WarreDV2004/UCD/Images/testen prototype 2 test 3.jpeg

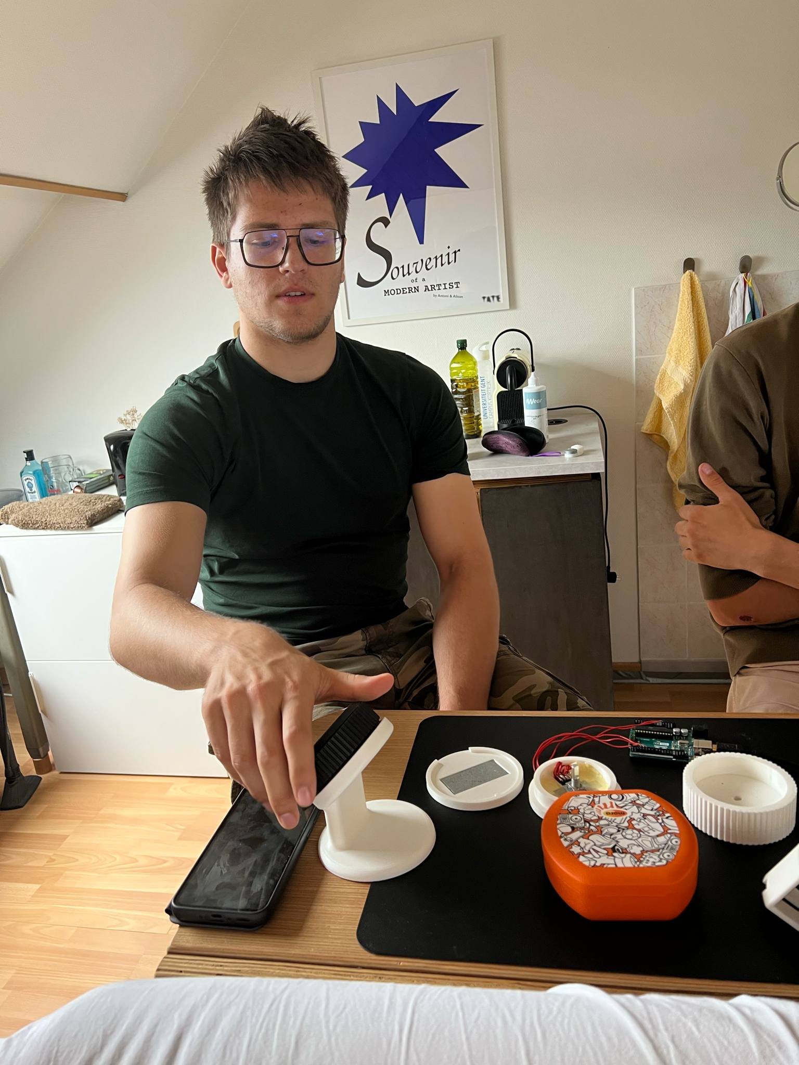
Images/testen prototype 2 test 3.jpeg
