WarreDV2004/UCD/Images/testen prototype test 3.jpeg

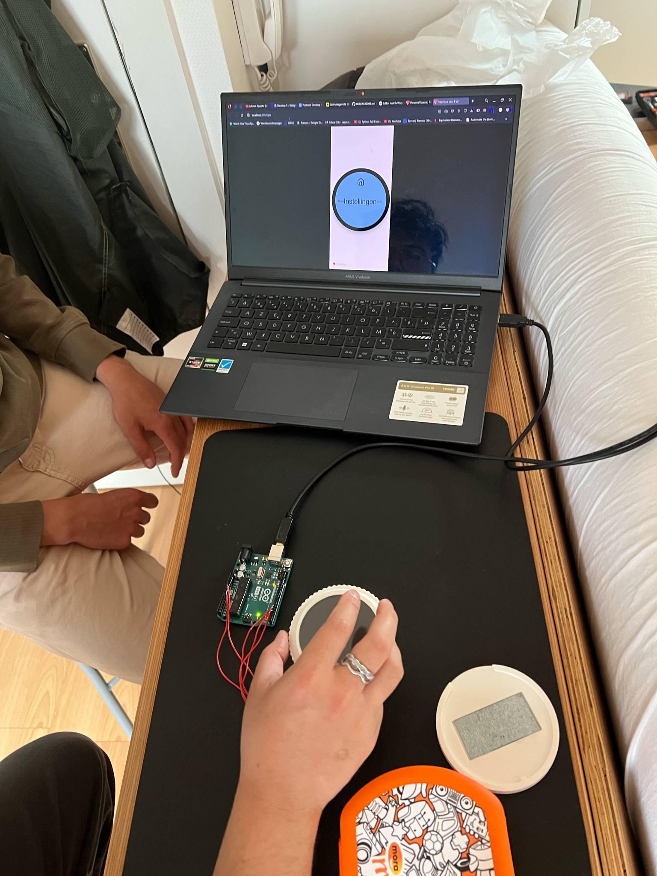
Images/testen prototype test 3.jpeg
