WarreDV2004/UCD/Images/0b0f451a-5053-4762-9009-be1f7eaaebb7.jpeg

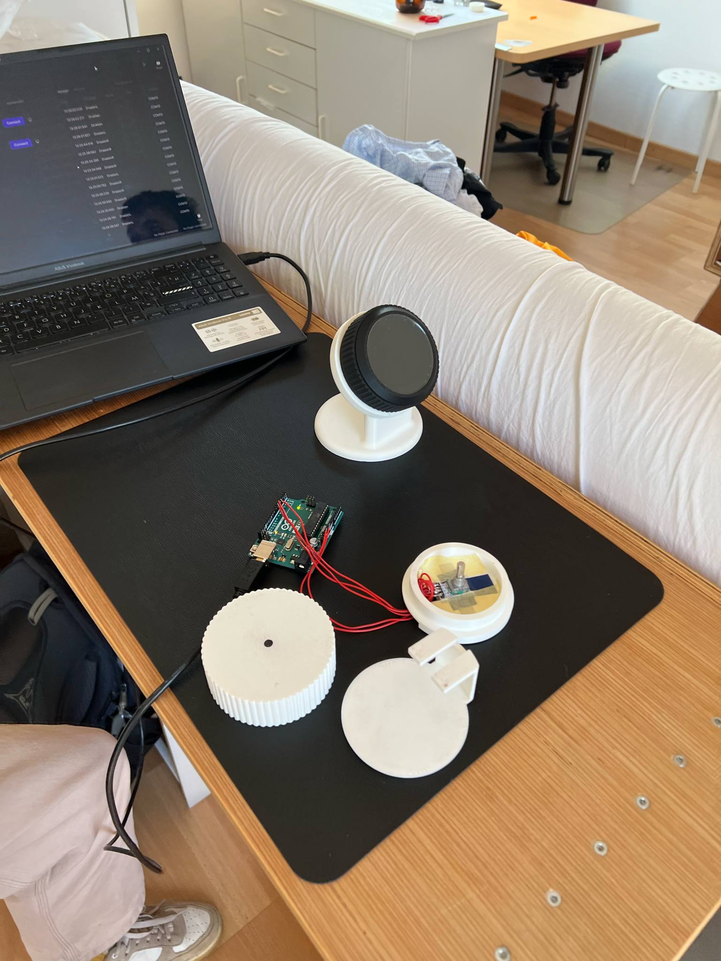
Images/0b0f451a-5053-4762-9009-be1f7eaaebb7.jpeg
