WarreDV2004/UCD/Images/2bf49bff-31a4-4e18-b3c8-147d3d34425b.jpeg

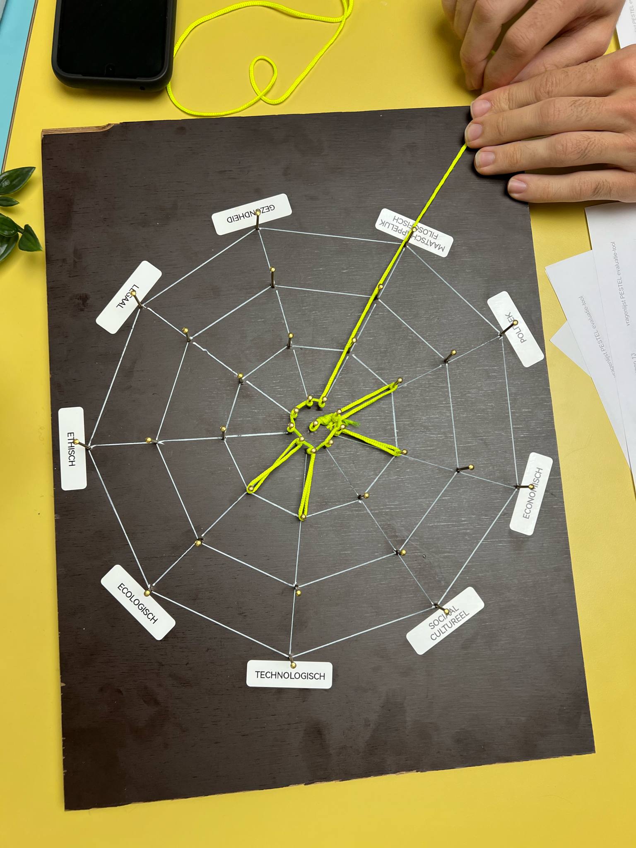
Images/2bf49bff-31a4-4e18-b3c8-147d3d34425b.jpeg
