WarreDV2004/UCD/Images/2db6f0e0-078a-4a34-bcfe-8d26bea21af6.jpeg

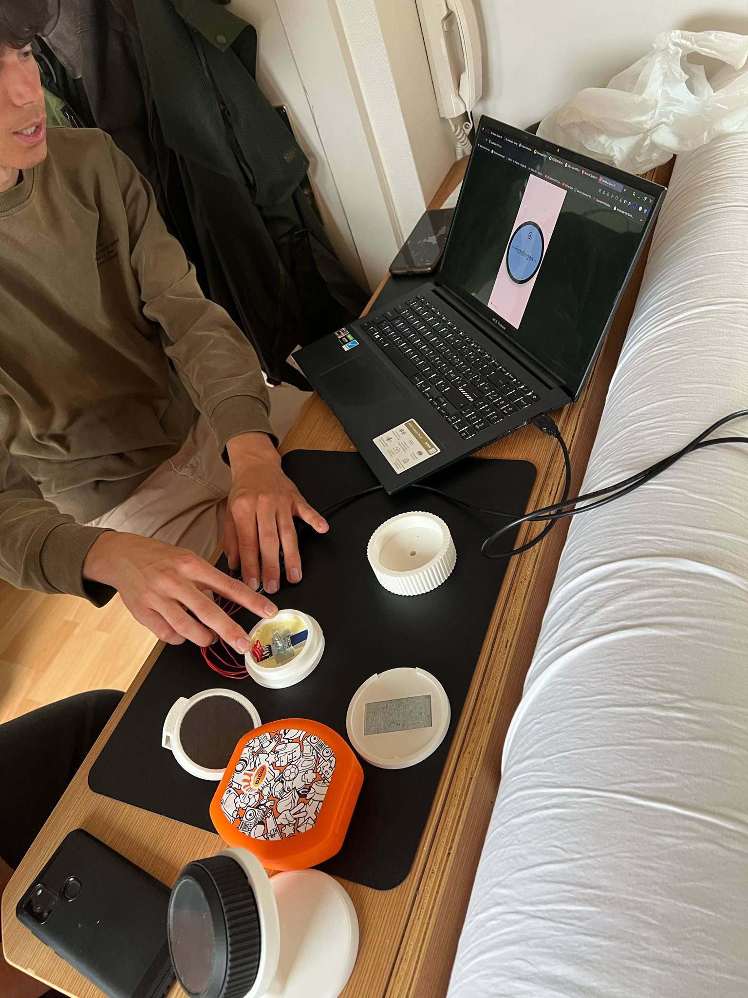
Images/2db6f0e0-078a-4a34-bcfe-8d26bea21af6.jpeg
