WarreDV2004/UCD/Images/4b927118-f5e4-4843-87f0-c27fd5104562.jpeg

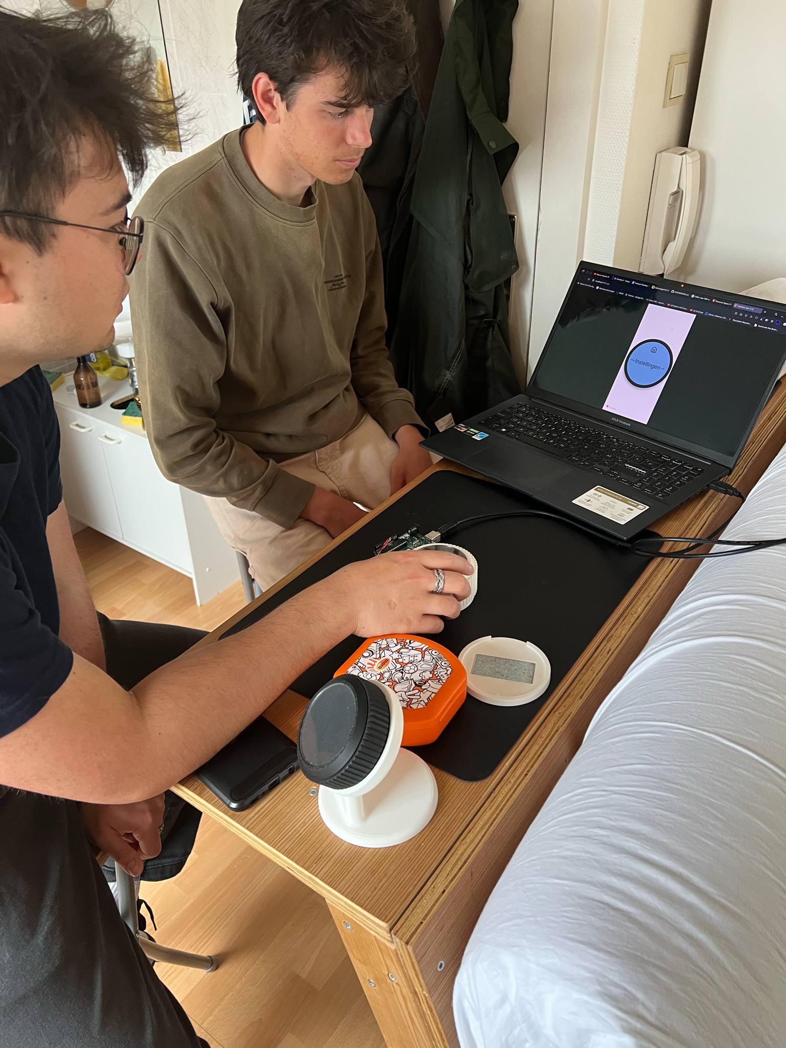
Images/4b927118-f5e4-4843-87f0-c27fd5104562.jpeg
