WarreDV2004/UCD/Images/4e render exploded view.jpg

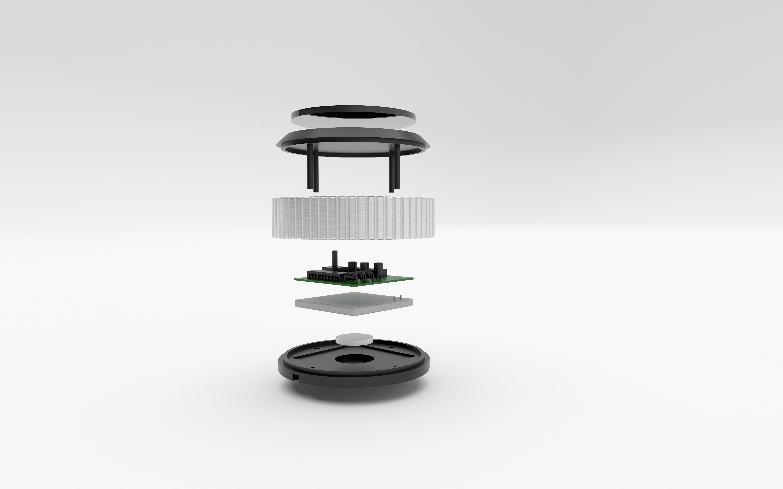
Images/4e render exploded view.jpg
