WarreDV2004/UCD/Images/4fdb726b-e008-48d0-8b07-4f853df536ba.jpeg

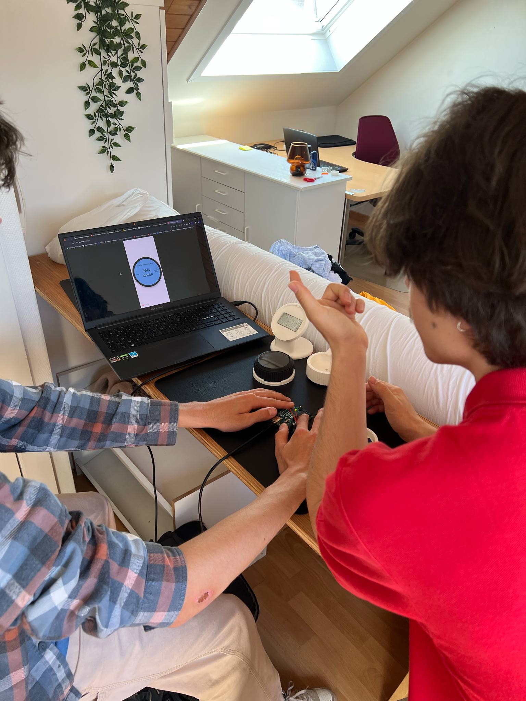
Images/4fdb726b-e008-48d0-8b07-4f853df536ba.jpeg
