WarreDV2004/UCD/Images/8ac05575-f322-4f7c-a051-7a8421dc1b2e.jpeg

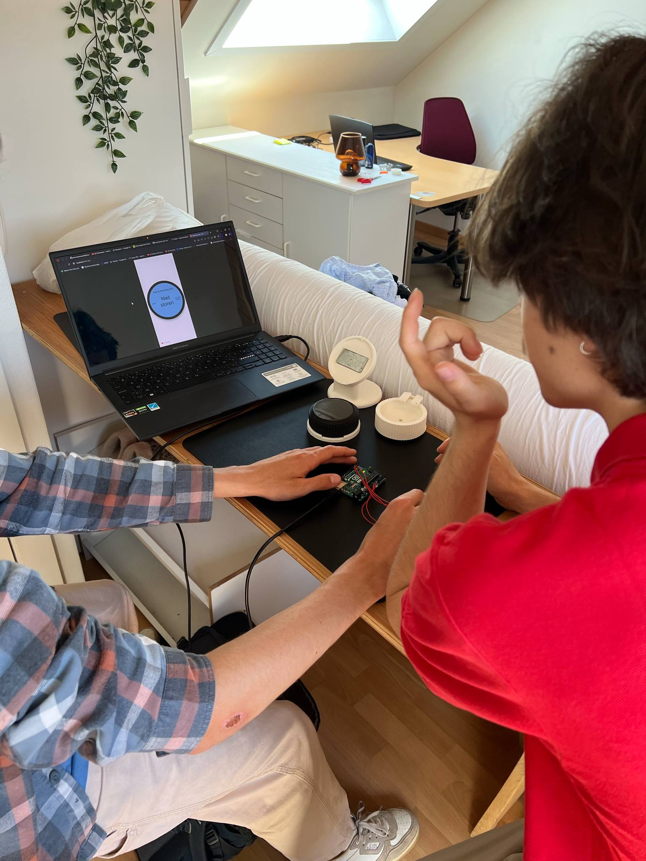
Images/8ac05575-f322-4f7c-a051-7a8421dc1b2e.jpeg
