WarreDV2004/UCD/Images/13f31a89-18ec-47ce-9137-7a15a04f8204.jpeg

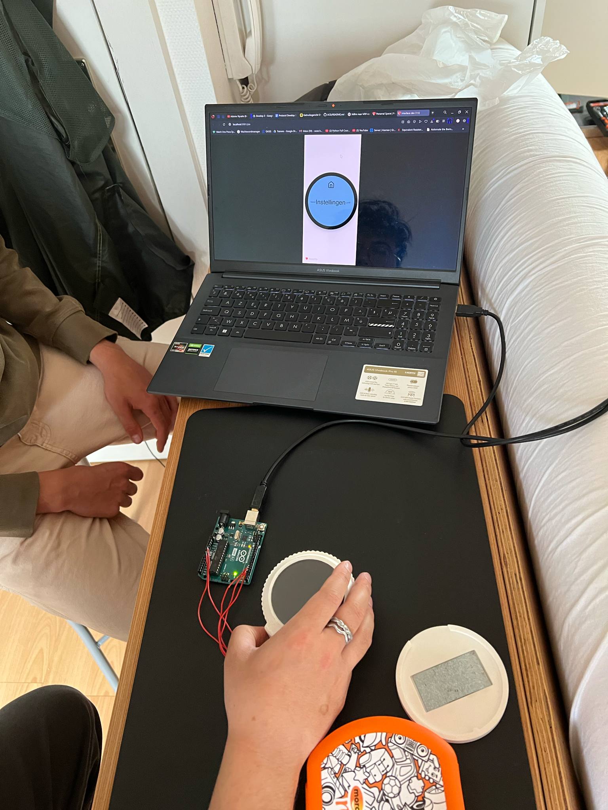
Images/13f31a89-18ec-47ce-9137-7a15a04f8204.jpeg
