WarreDV2004/UCD/Images/45c63ba8-a671-4e61-bb3f-2d00b8ac04eb.jpeg

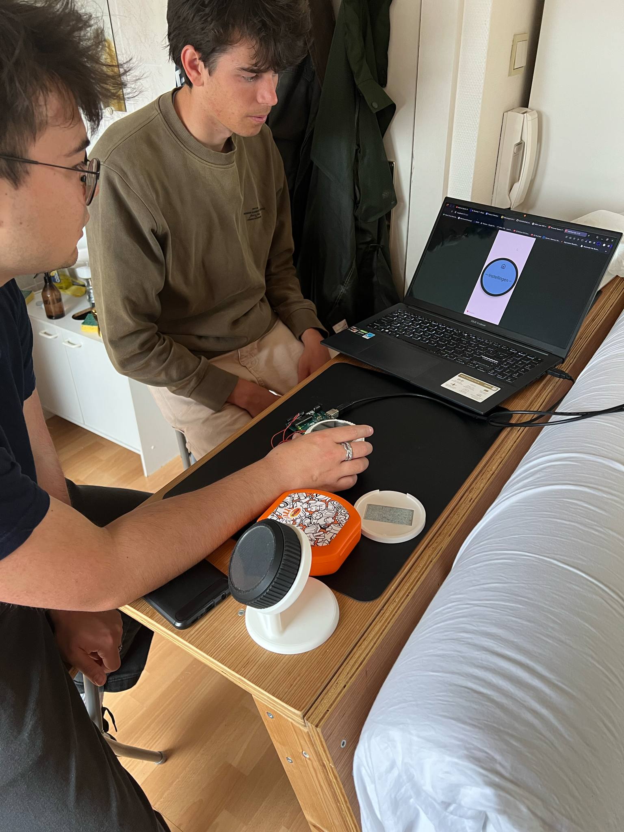
Images/45c63ba8-a671-4e61-bb3f-2d00b8ac04eb.jpeg
