WarreDV2004/UCD/Images/81fb5b29-8a82-44d0-8cb8-3fc07b8e7cfb.jpeg

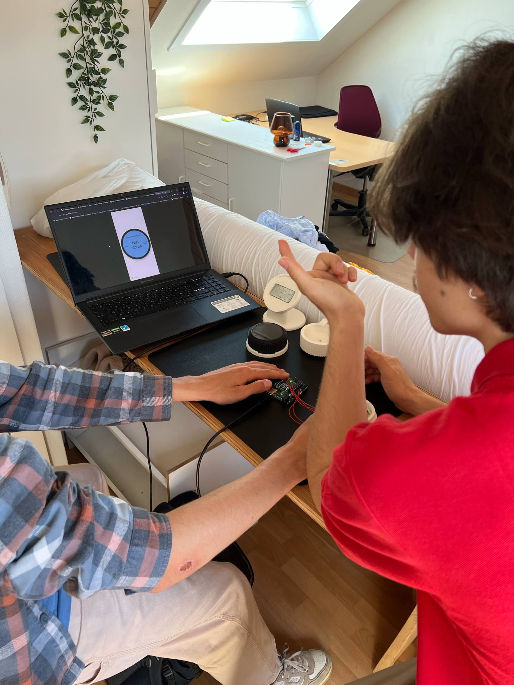
Images/81fb5b29-8a82-44d0-8cb8-3fc07b8e7cfb.jpeg
