WarreDV2004/UCD/Images/103dc806-d890-496e-9fd0-2eff75873912.jpeg

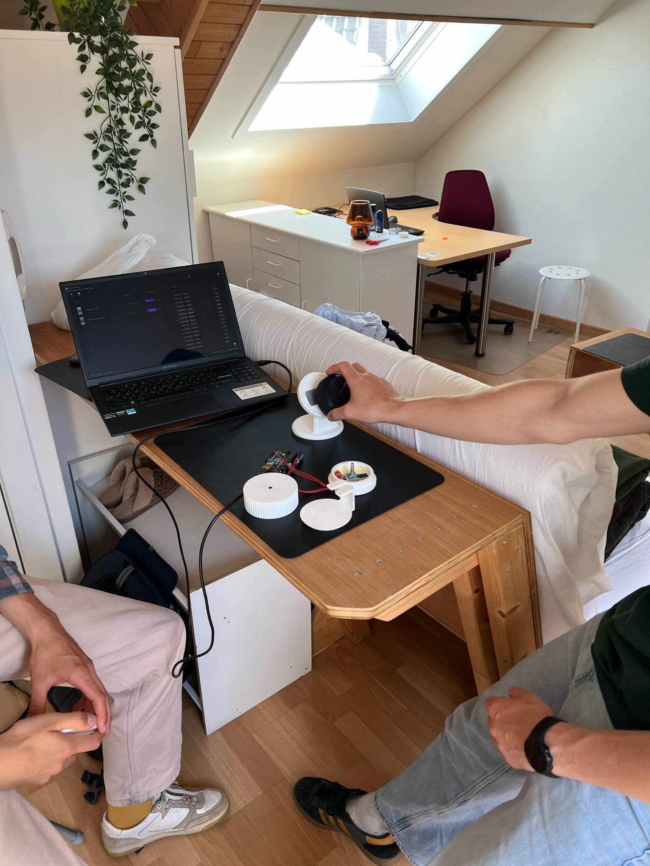
Images/103dc806-d890-496e-9fd0-2eff75873912.jpeg
