WarreDV2004/UCD/Images/169db717-07ae-4d13-a04f-ba3e3b913fad.jpeg

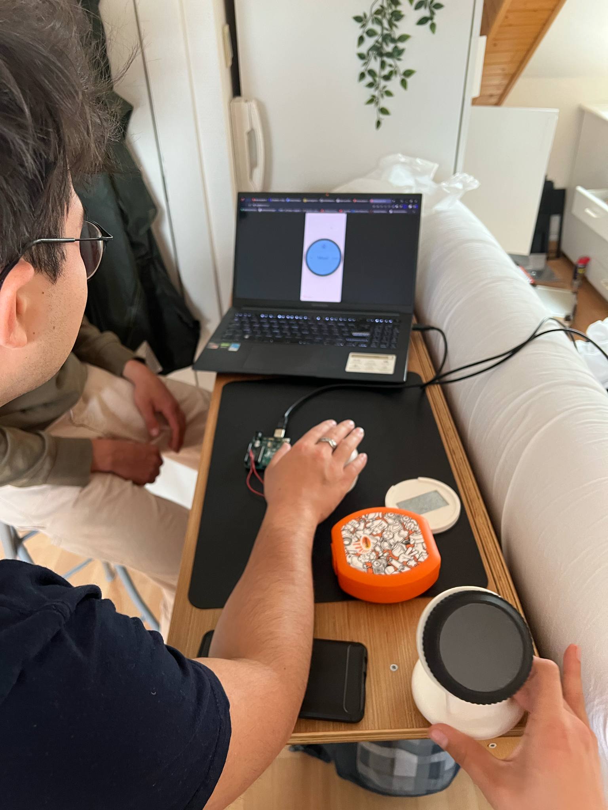
Images/169db717-07ae-4d13-a04f-ba3e3b913fad.jpeg
