WarreDV2004/UCD/Images/230cefa4-2b14-4361-b15c-a140190fd961.jpeg

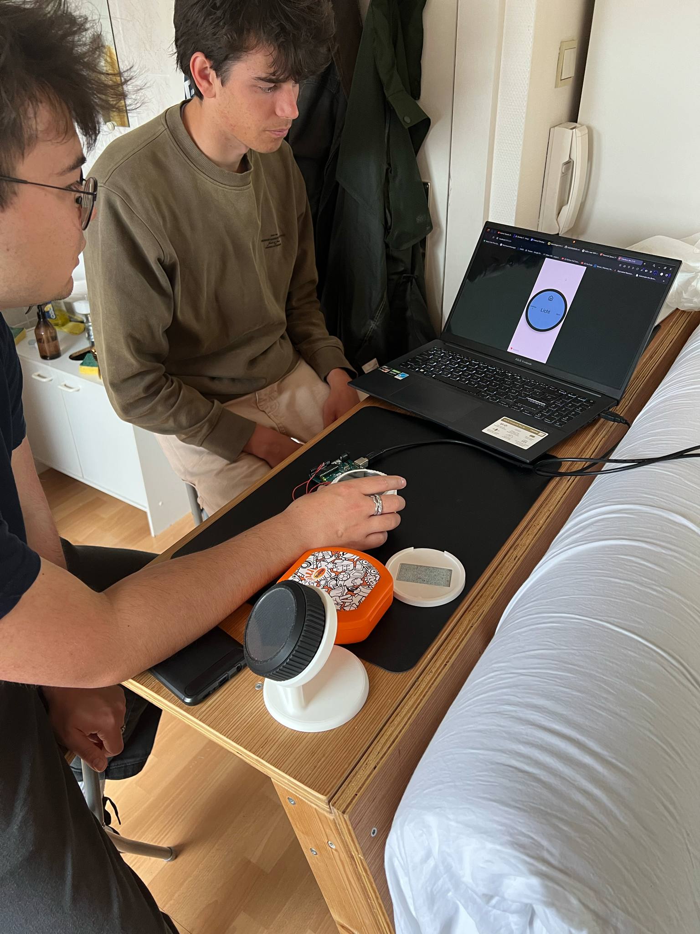
Images/230cefa4-2b14-4361-b15c-a140190fd961.jpeg
