WarreDV2004/UCD/Images/235fdd10-d258-4962-a08e-ac36dd64d68d.jpeg

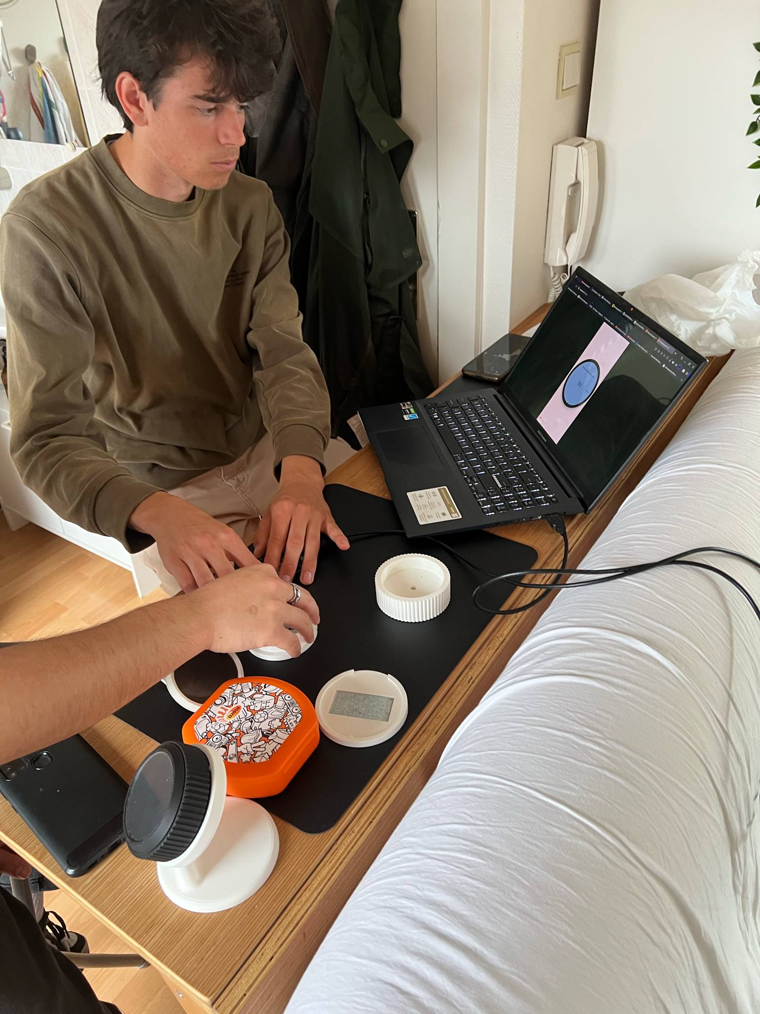
Images/235fdd10-d258-4962-a08e-ac36dd64d68d.jpeg
