WarreDV2004/UCD/Images/516b5541-f568-4937-b32e-dc914a8df41c.jpeg

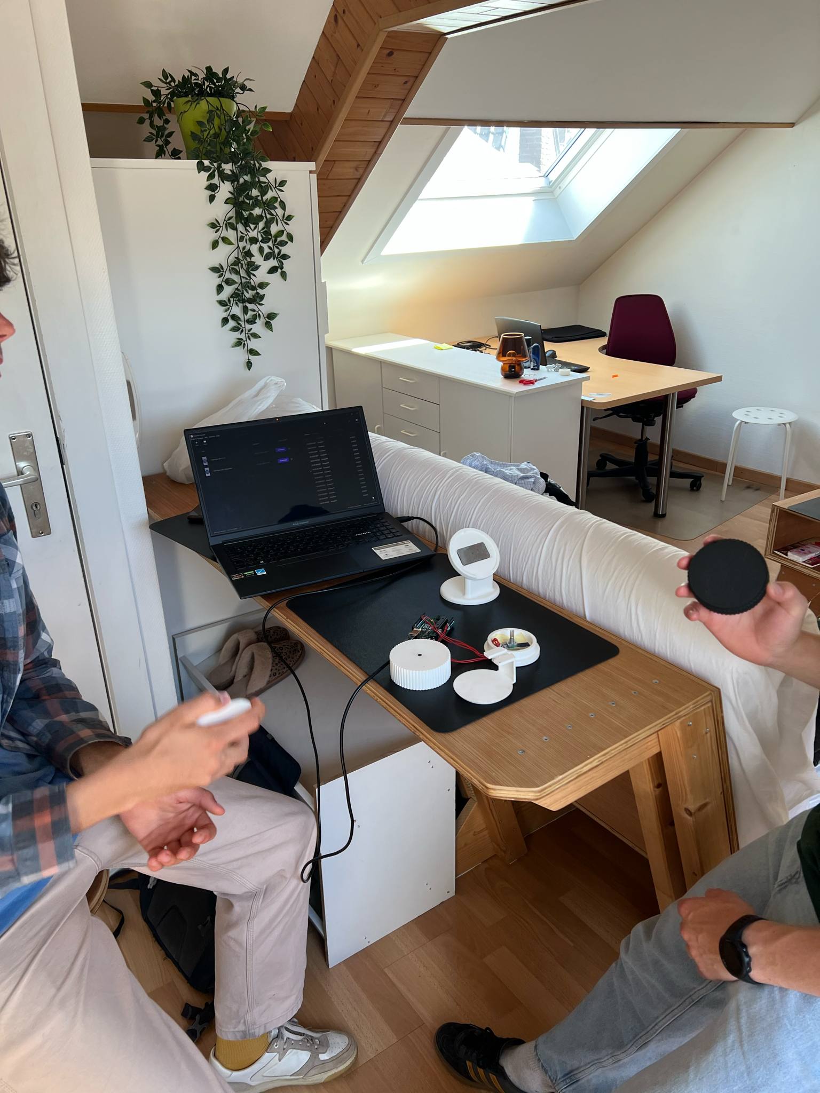
Images/516b5541-f568-4937-b32e-dc914a8df41c.jpeg
