WarreDV2004/UCD/Images/696e4ac5-deb2-44e5-8a80-ce5050431351.jpeg

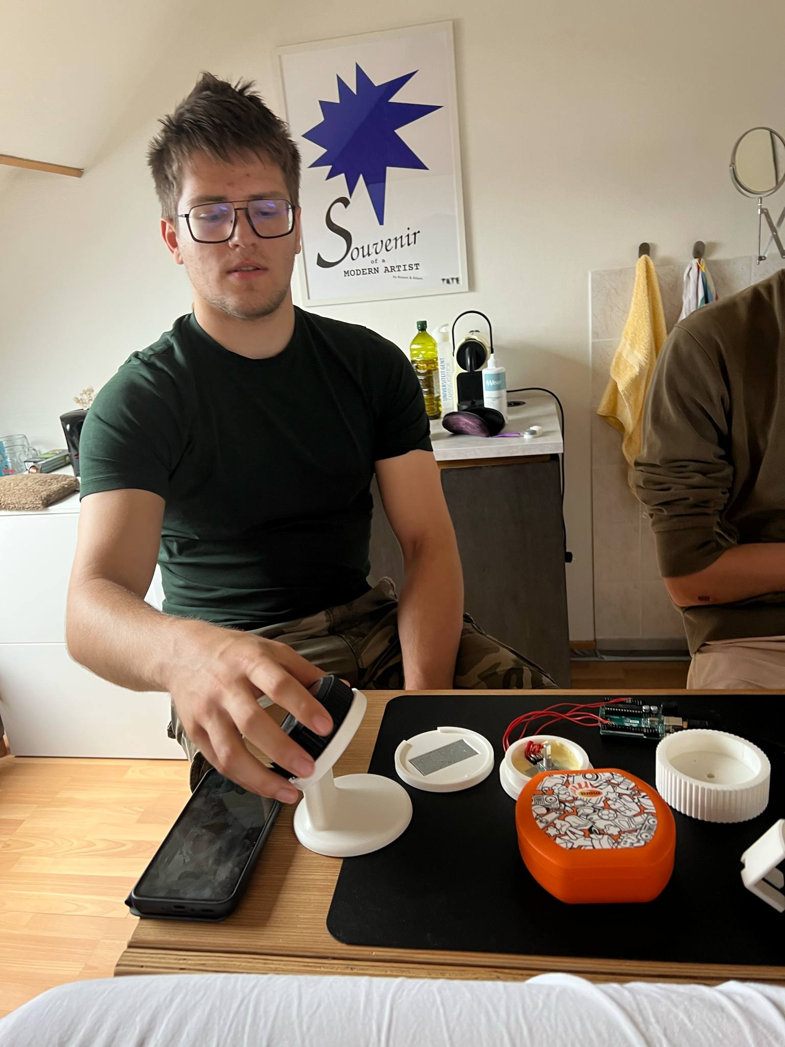
Images/696e4ac5-deb2-44e5-8a80-ce5050431351.jpeg
