WarreDV2004/UCD/Images/876d89a1-647a-4278-9378-e442717ffbb1.jpeg

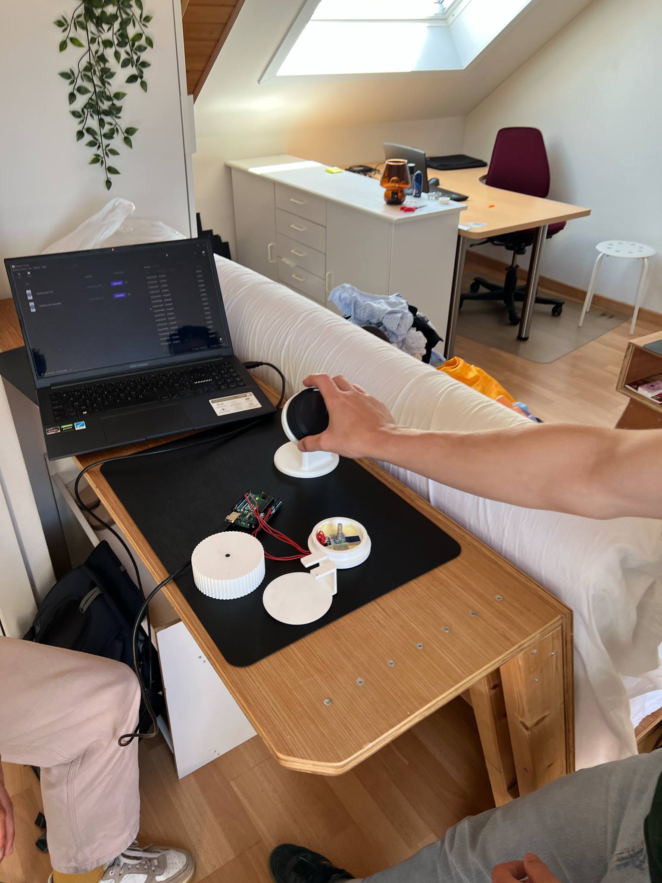
Images/876d89a1-647a-4278-9378-e442717ffbb1.jpeg
