WarreDV2004/UCD/Images/32217a44-98ed-48ee-934f-d554f41f827a.jpeg

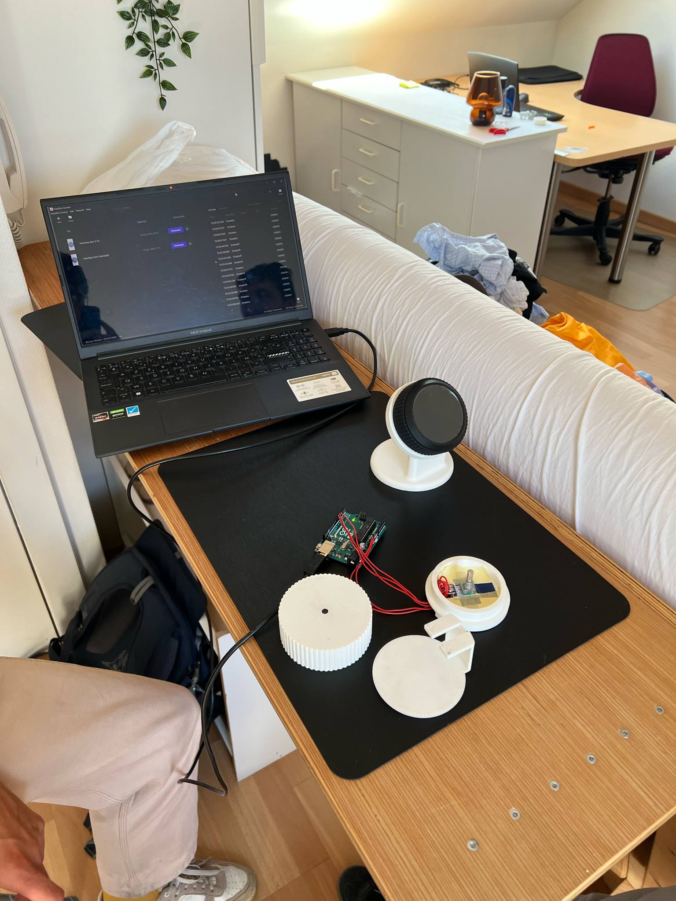
Images/32217a44-98ed-48ee-934f-d554f41f827a.jpeg
