WarreDV2004/UCD/Images/a9bcda80-063e-4bb6-8cd2-c2ead3fb787c.jpeg

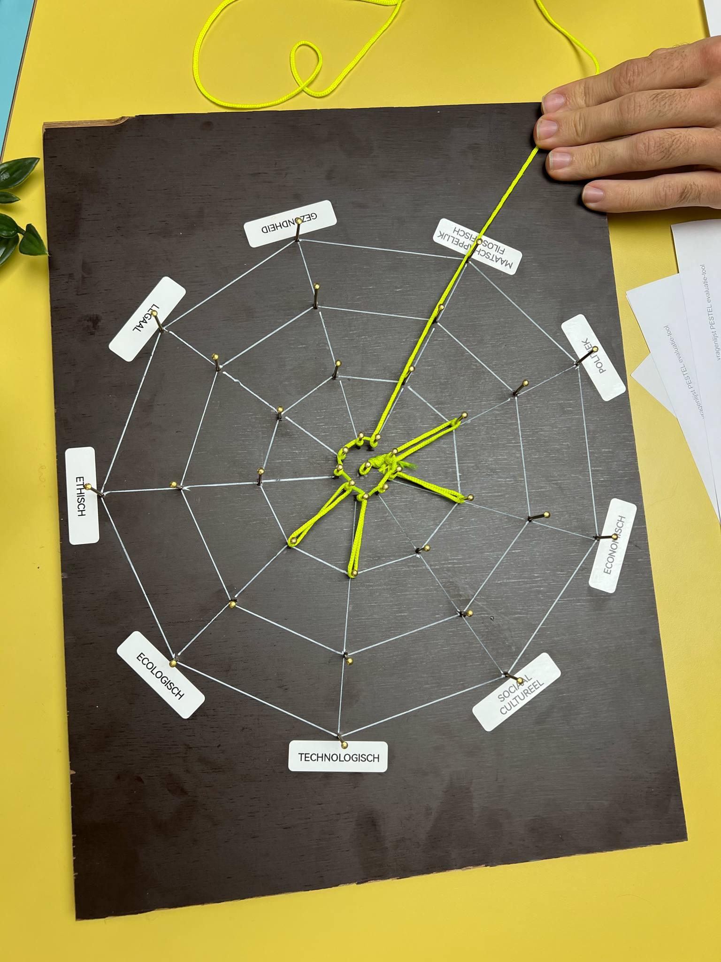
Images/a9bcda80-063e-4bb6-8cd2-c2ead3fb787c.jpeg
