WarreDV2004/UCD/Images/Afbeelding van WhatsApp op 2024-12-26 om 10.37.26_5b0e7dce.jpg

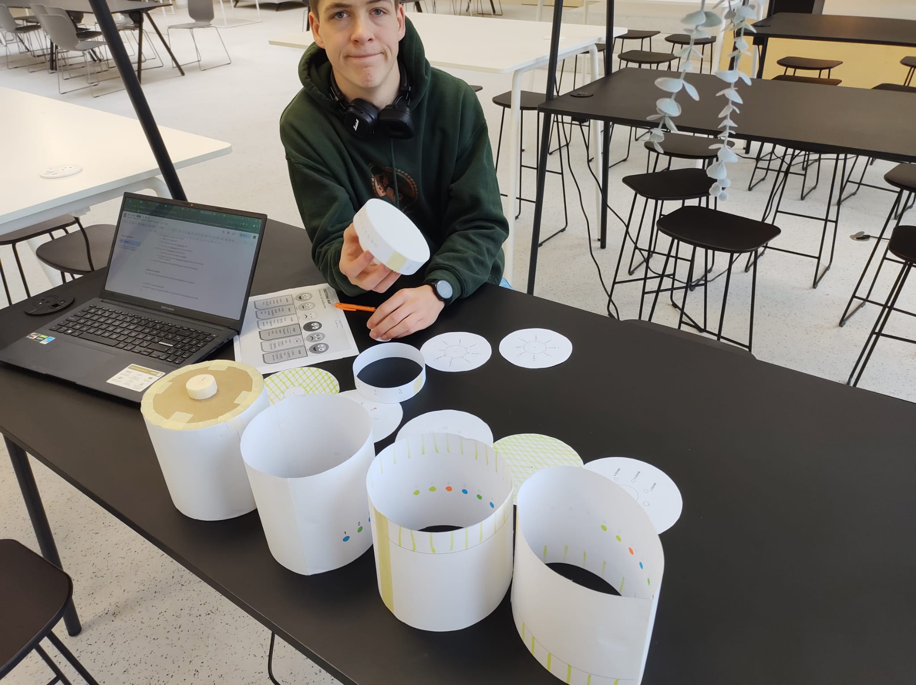
Images/Afbeelding van WhatsApp op 2024-12-26 om 10.37.26_5b0e7dce.jpg
