WarreDV2004/UCD/Images/Afbeelding van WhatsApp op 2025-03-13 om 10.50.53_343796fd.jpg

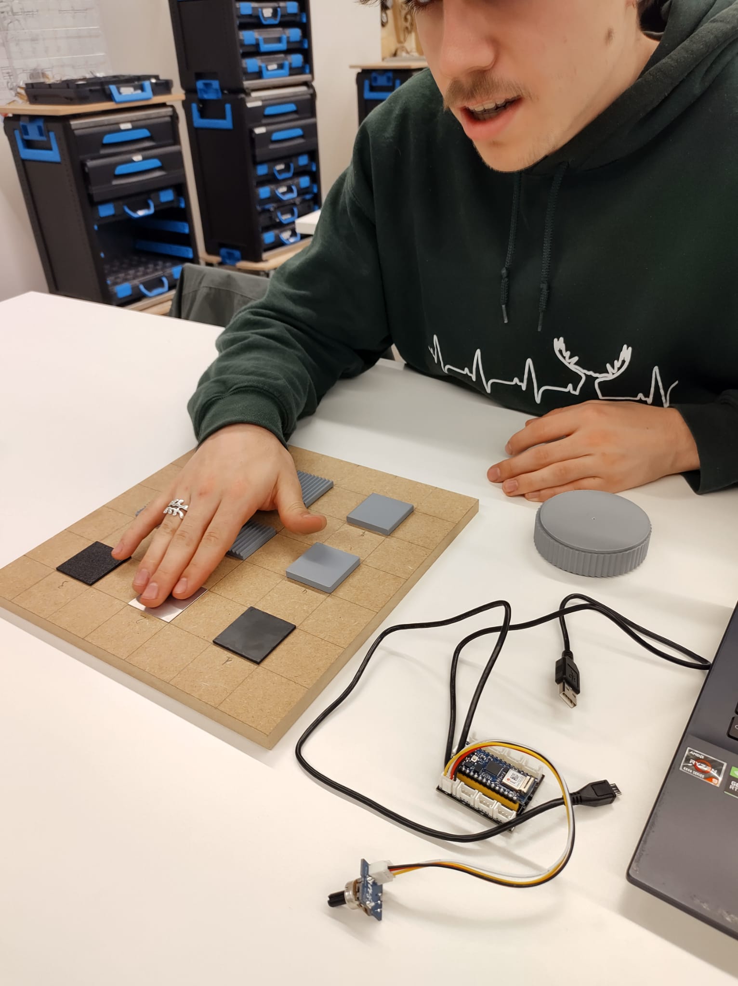
Images/Afbeelding van WhatsApp op 2025-03-13 om 10.50.53_343796fd.jpg
