WarreDV2004/UCD/Images/comfort analyse Met kader.png

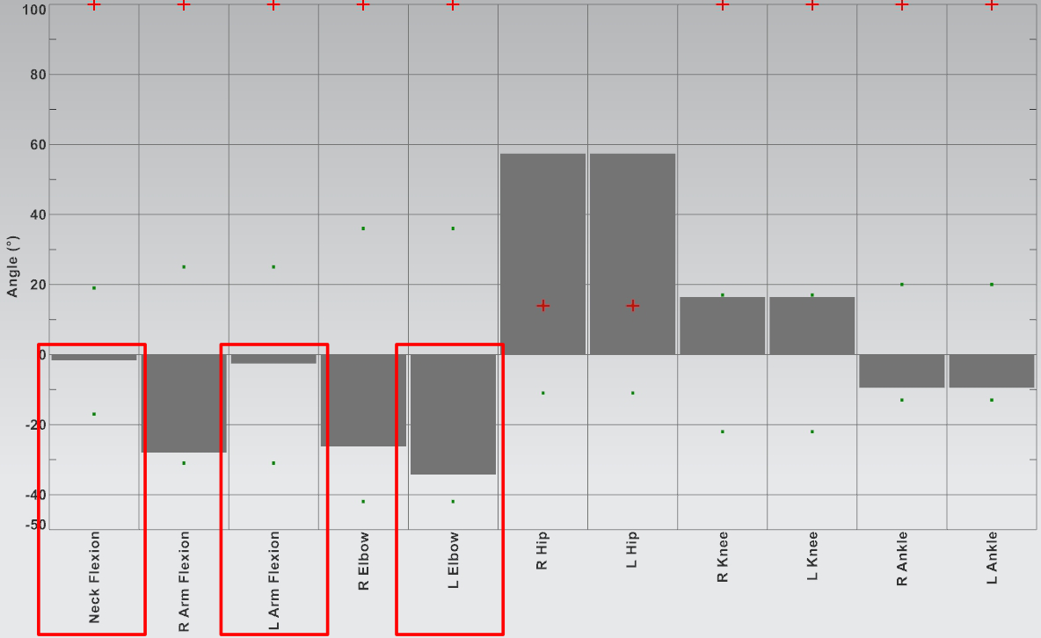
Images/comfort analyse Met kader.png
