WarreDV2004/UCD/Images/e36cca00-fef1-404c-8d76-1b665b50a3e8.jpeg

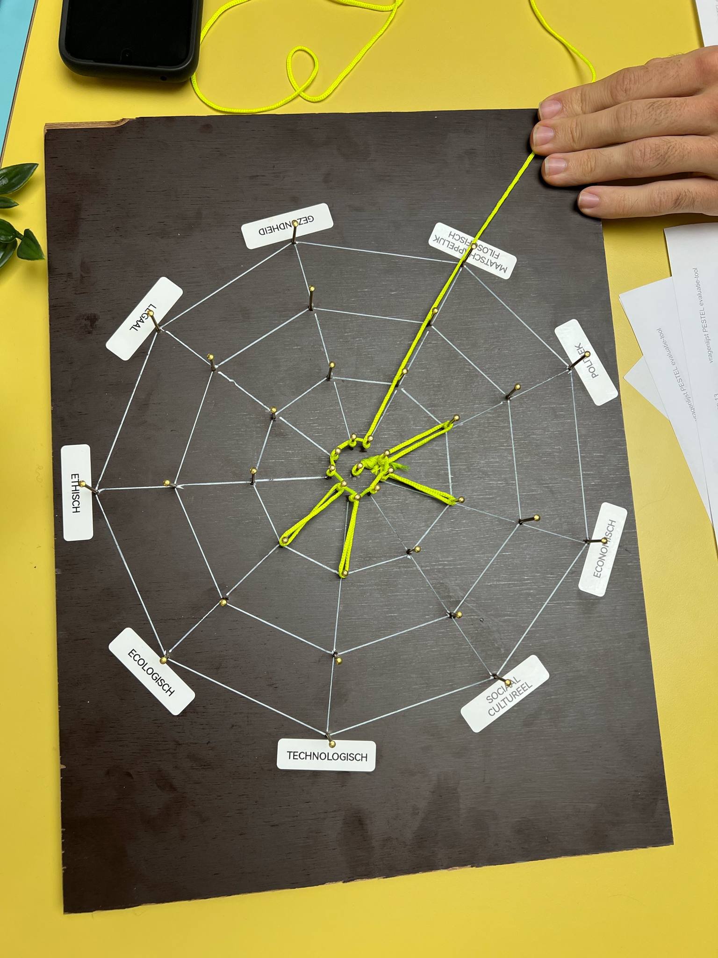
Images/e36cca00-fef1-404c-8d76-1b665b50a3e8.jpeg
