WarreDV2004/UCD/Images/e7774b88-3000-45da-9ccf-a76e1e3f5f13.jpeg

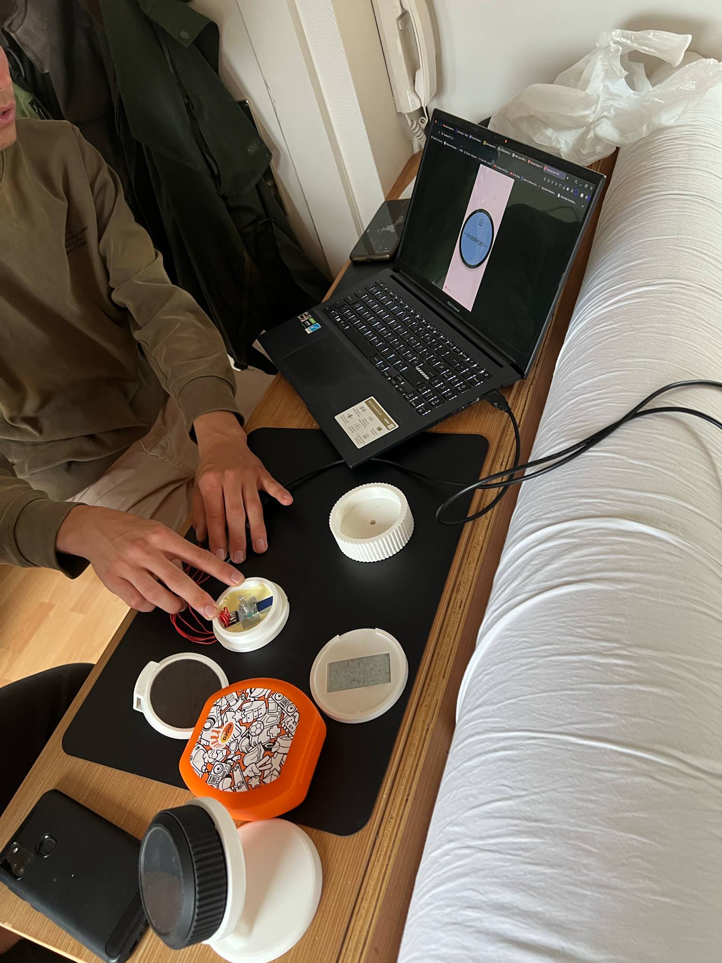
Images/e7774b88-3000-45da-9ccf-a76e1e3f5f13.jpeg
