WarreDV2004/UCD/Images/IMG-20241212-WA0003.jpg

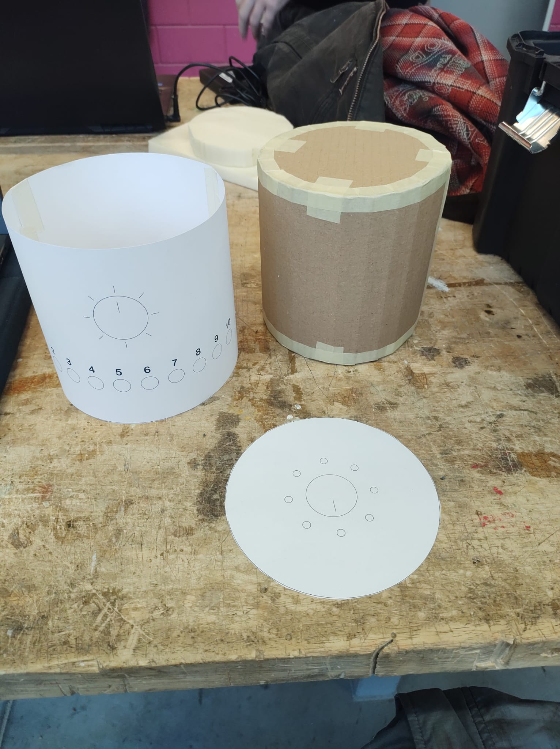
Images/IMG-20241212-WA0003.jpg
