WarreDV2004/UCD/Images/IMG-20241226-WA0004.jpg

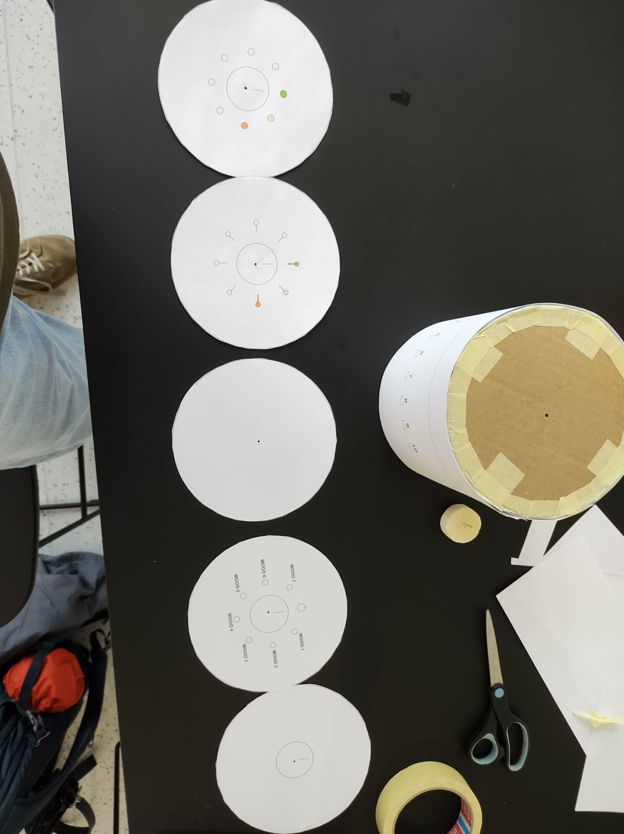
Images/IMG-20241226-WA0004.jpg
