WarreDV2004/UCD/Images/IMG-20241226-WA0006.jpg

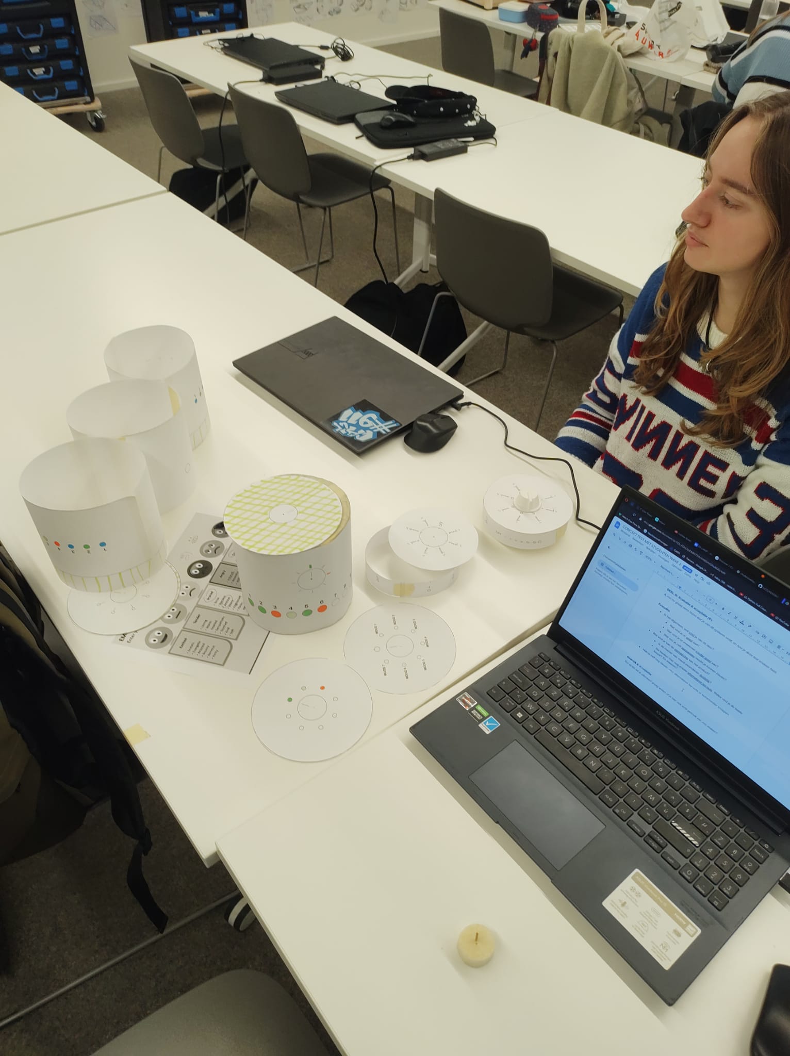
Images/IMG-20241226-WA0006.jpg
