WarreDV2004/UCD/Images/IMG-20241226-WA0007.jpg

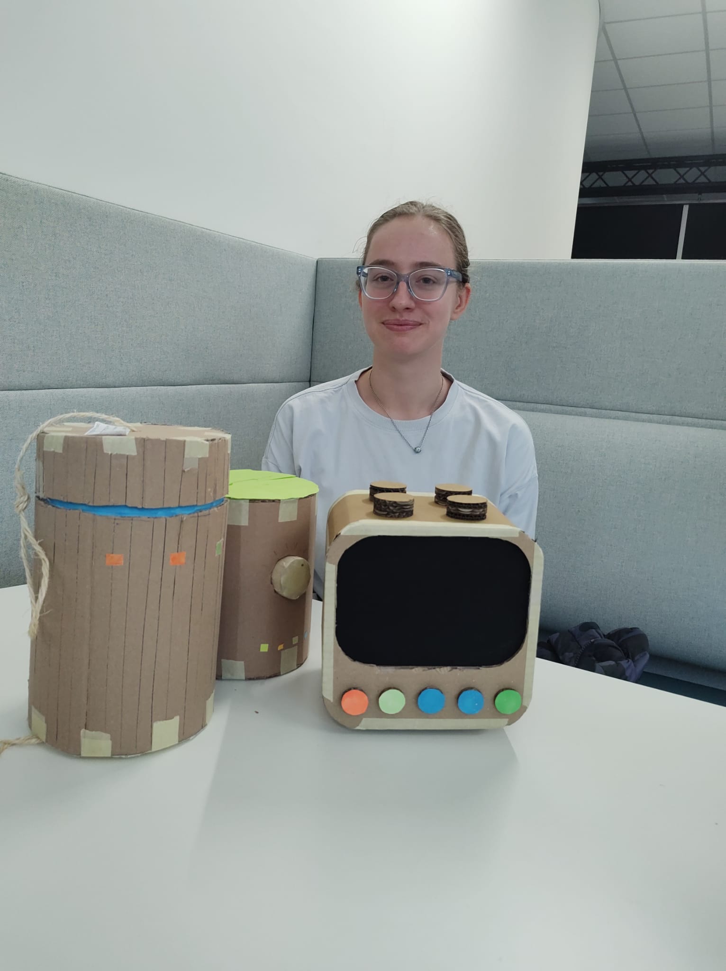
Images/IMG-20241226-WA0007.jpg
