WarreDV2004/UCD/Images/IMG-20241226-WA0008.jpg

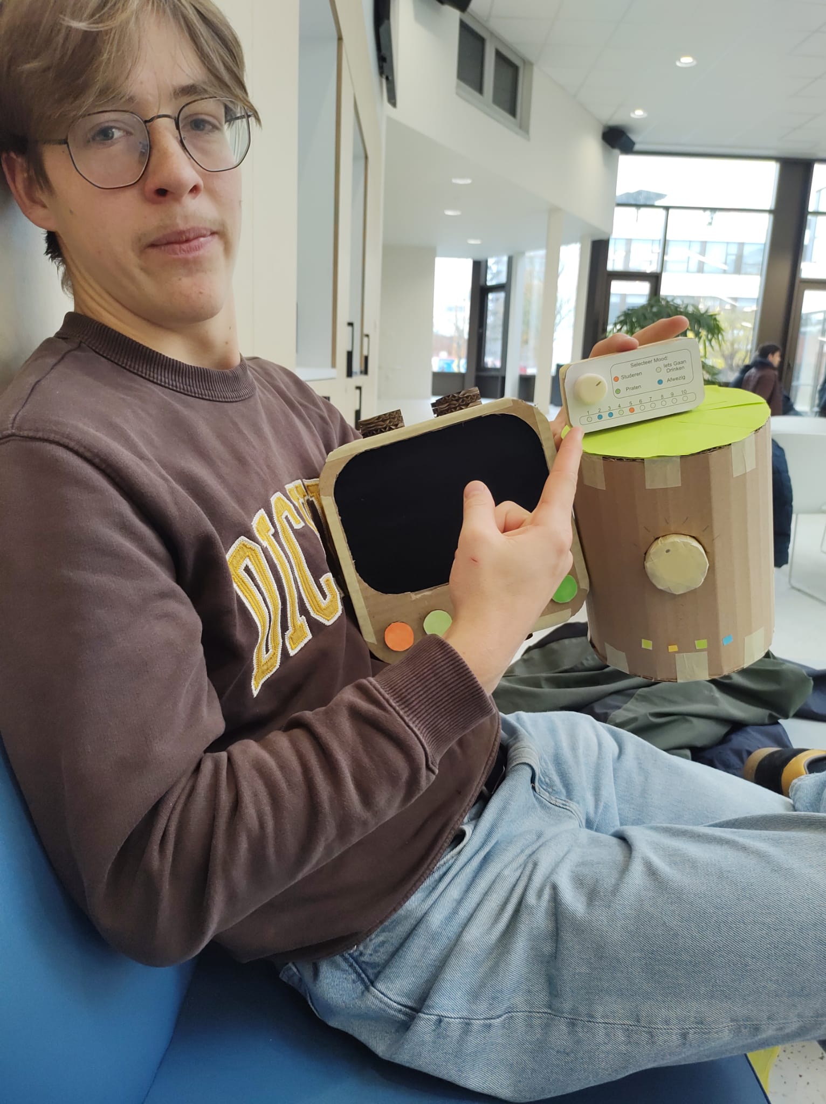
Images/IMG-20241226-WA0008.jpg
