WarreDV2004/UCD/Images/IMG-20250311-WA0006.jpg

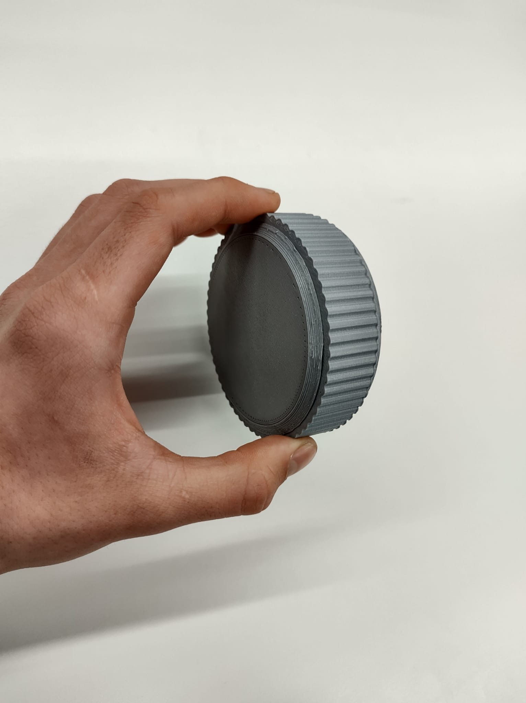
Images/IMG-20250311-WA0006.jpg
