WarreDV2004/UCD/Images/IMG-20250311-WA0008.jpg

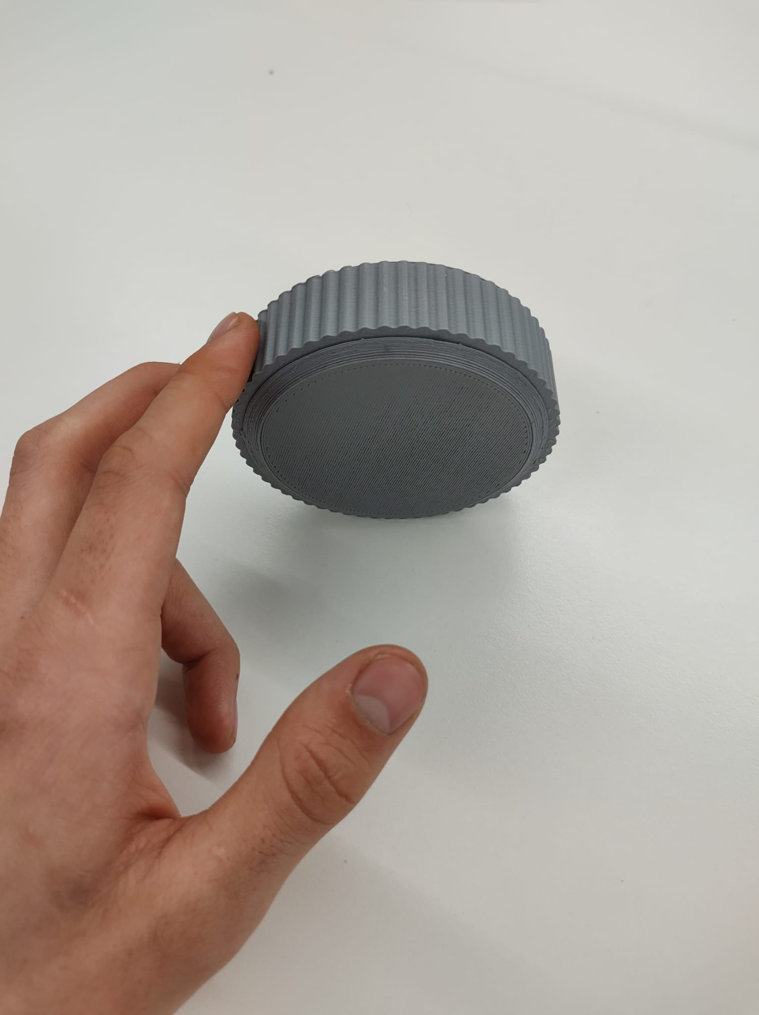
Images/IMG-20250311-WA0008.jpg
