WarreDV2004/UCD/Images/IMG-20250313-WA0004.jpg

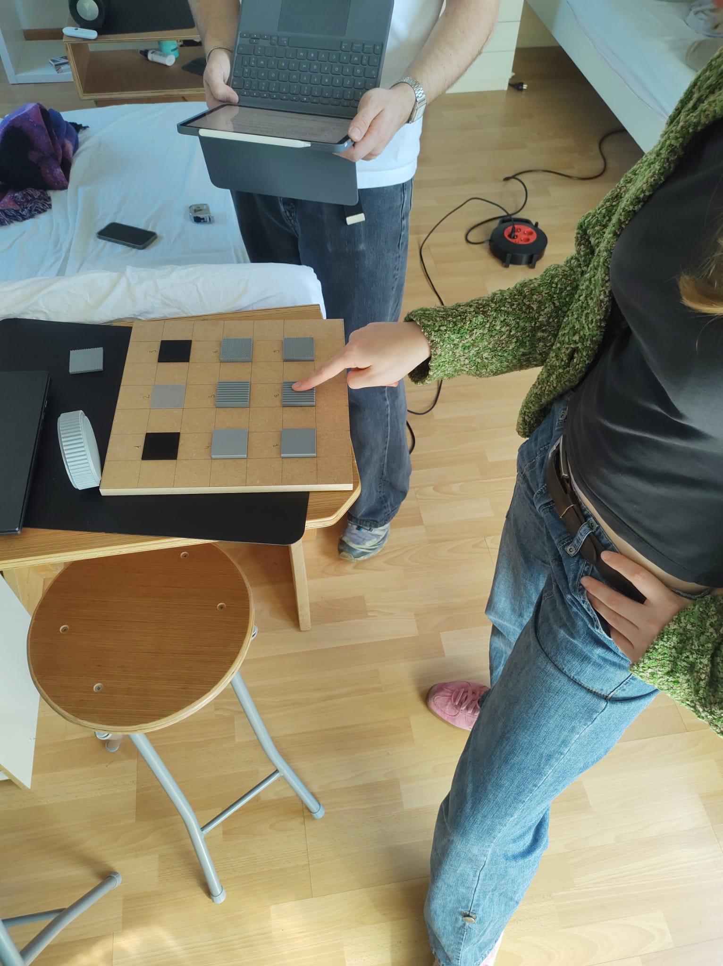
Images/IMG-20250313-WA0004.jpg
