WarreDV2004/UCD/Images/IMG-20250313-WA0005.jpg

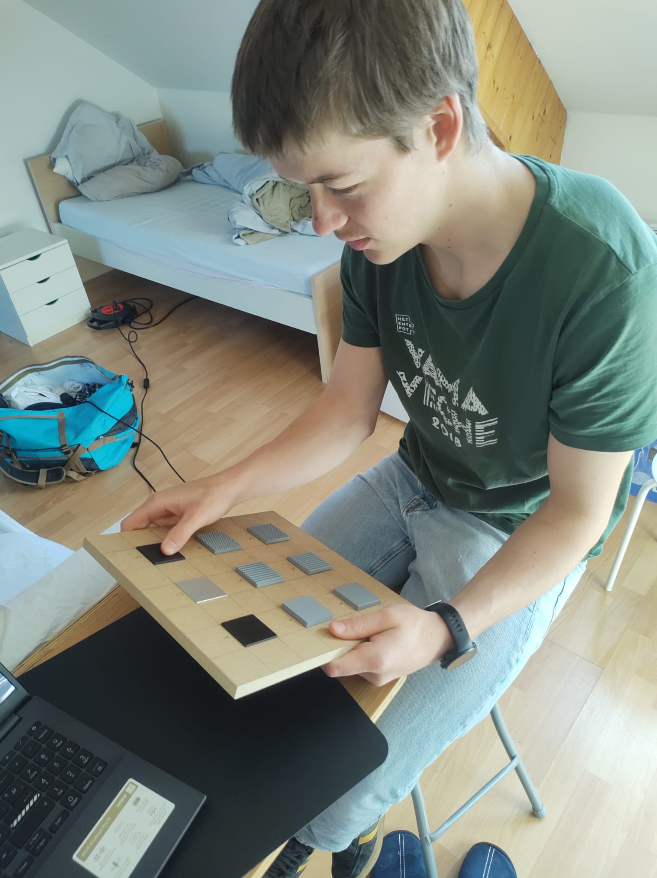
Images/IMG-20250313-WA0005.jpg
