WarreDV2004/UCD/Images/IMG-20250522-WA0004.jpg

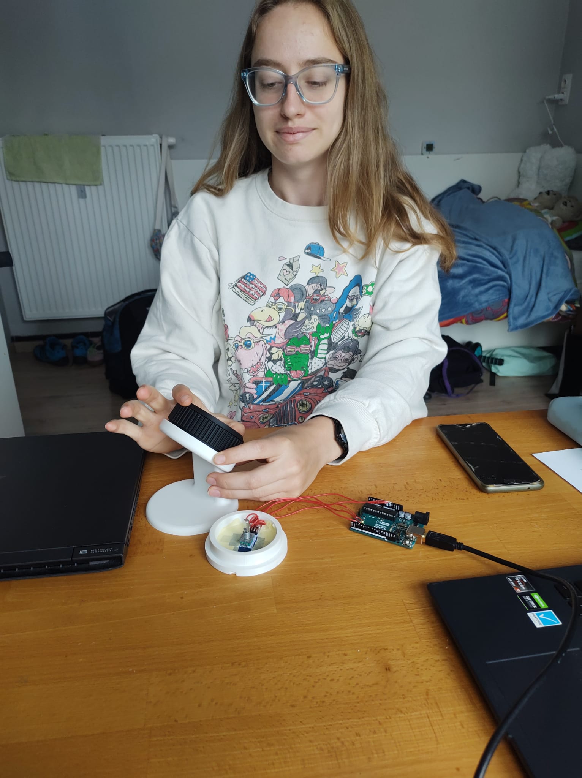
Images/IMG-20250522-WA0004.jpg
