WarreDV2004/UCD/Images/IMG-20250522-WA0005.jpg

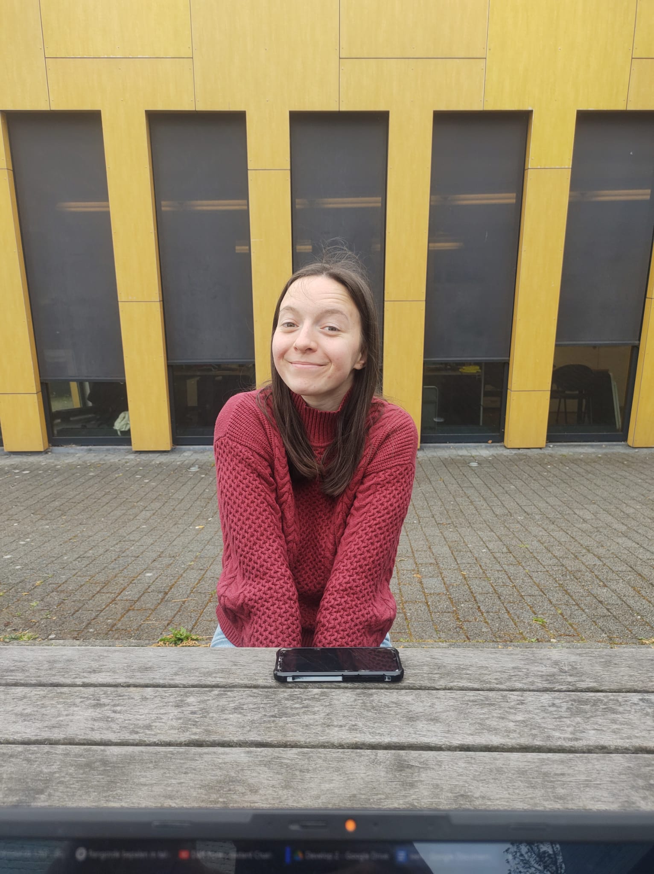
Images/IMG-20250522-WA0005.jpg
