WarreDV2004/UCD/Images/IMG_6328.jpg

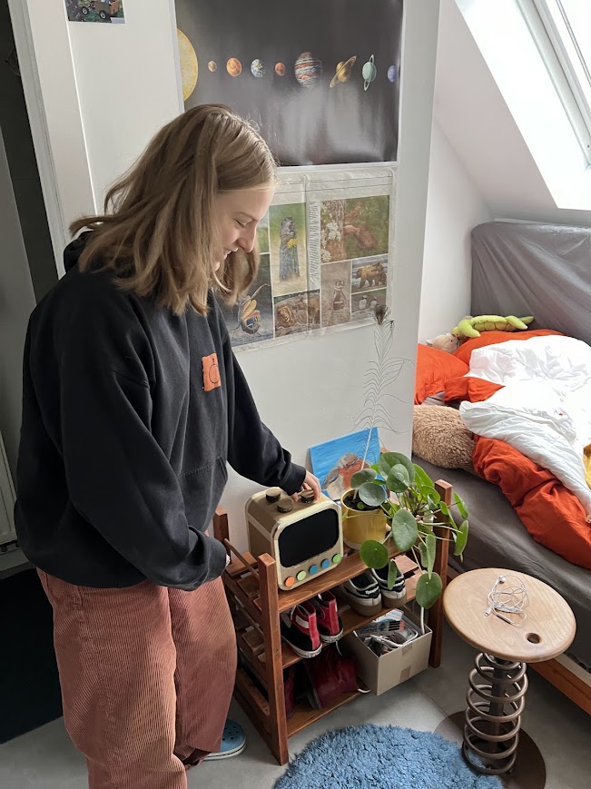
Images/IMG_6328.jpg
