WarreDV2004/UCD/Images/IMG_6329.jpg

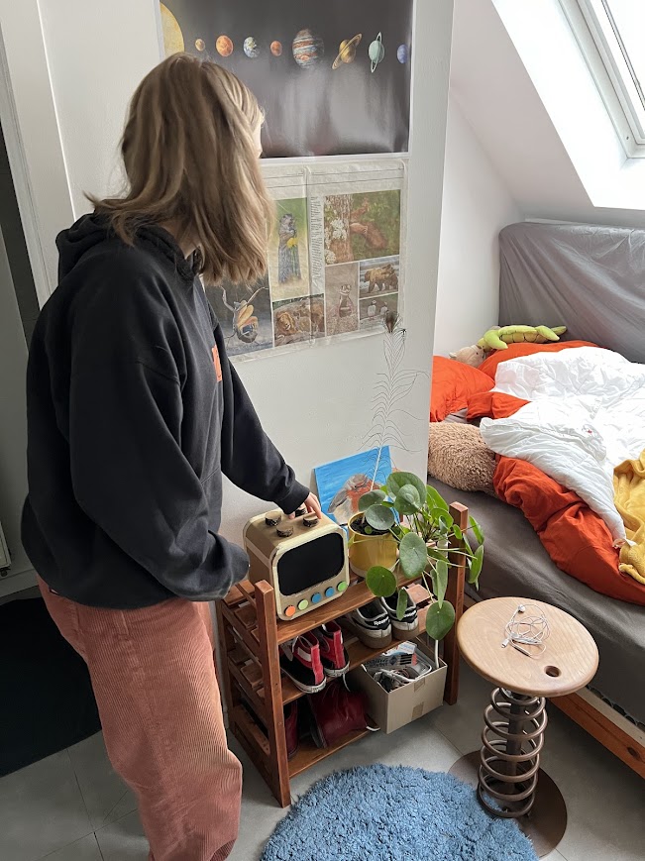
Images/IMG_6329.jpg
