WarreDV2004/UCD/Images/IMG_6330.jpg

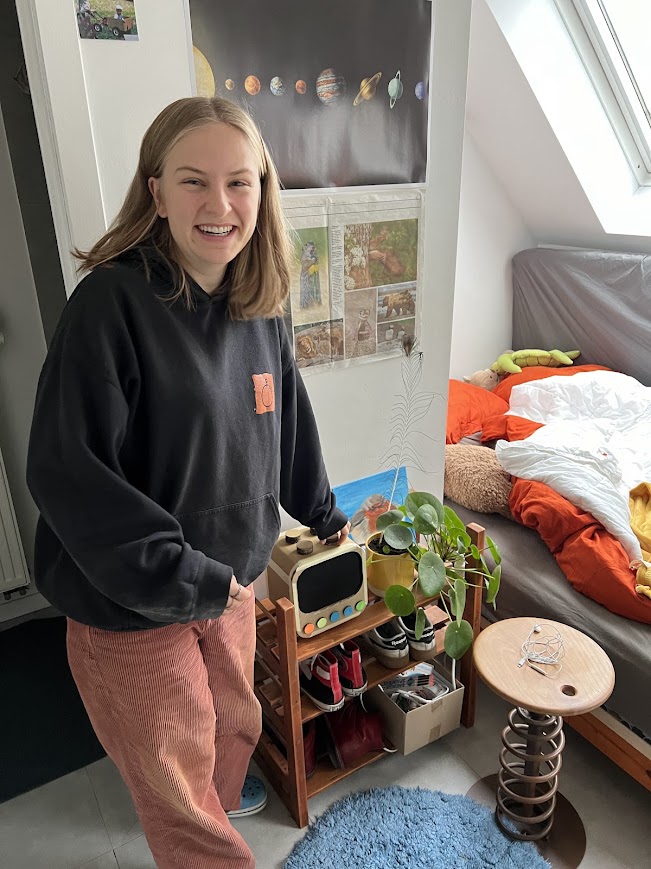
Images/IMG_6330.jpg
