WarreDV2004/UCD/Images/IMG_6331.jpg

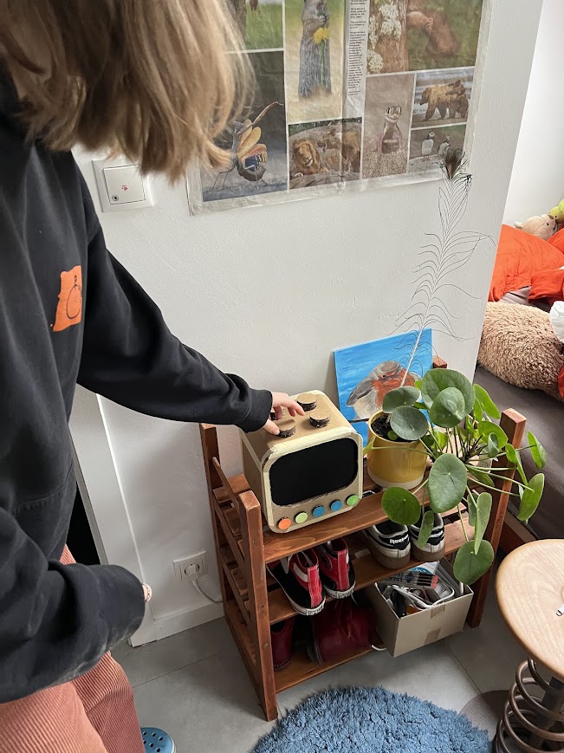
Images/IMG_6331.jpg
