WarreDV2004/UCD/Images/IMG_6332.jpg

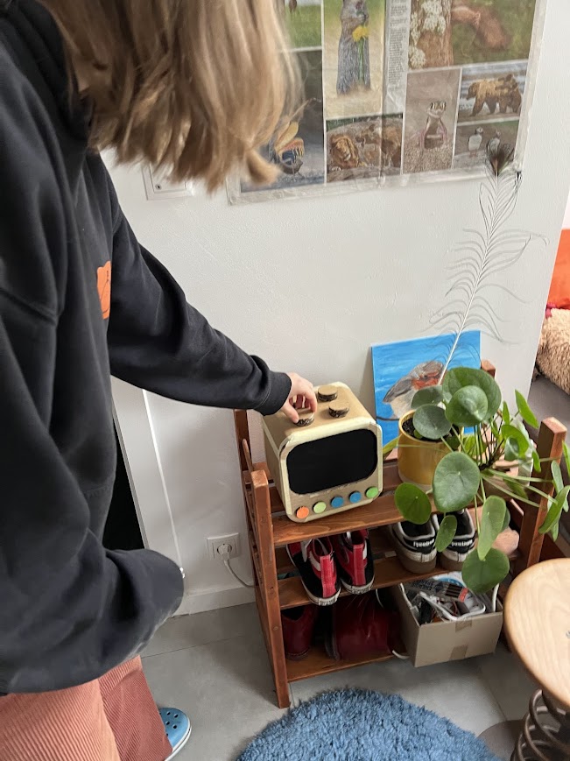
Images/IMG_6332.jpg
