WarreDV2004/UCD/Images/IMG_6333.jpg

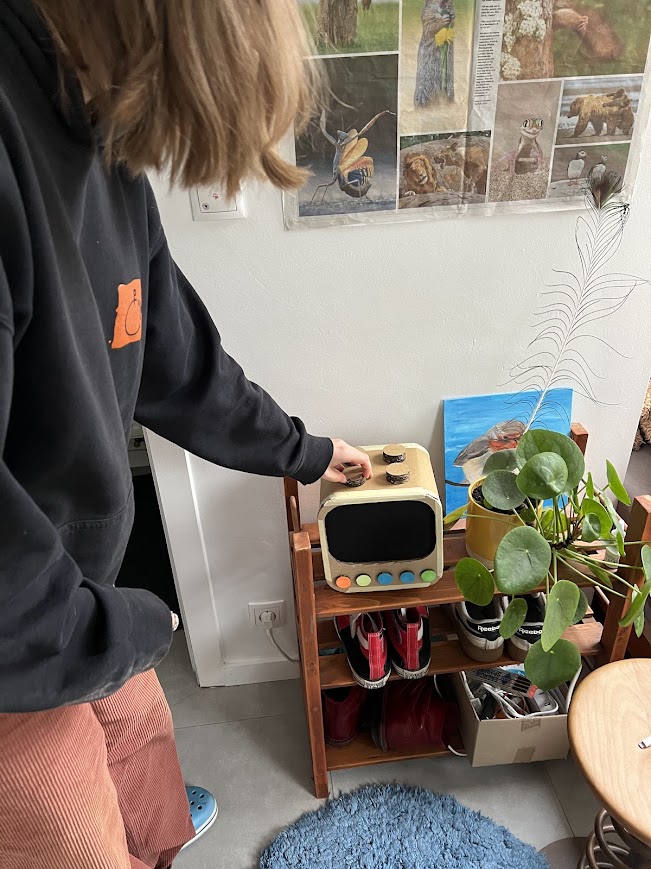
Images/IMG_6333.jpg
