WarreDV2004/UCD/Images/IMG_6334.jpg

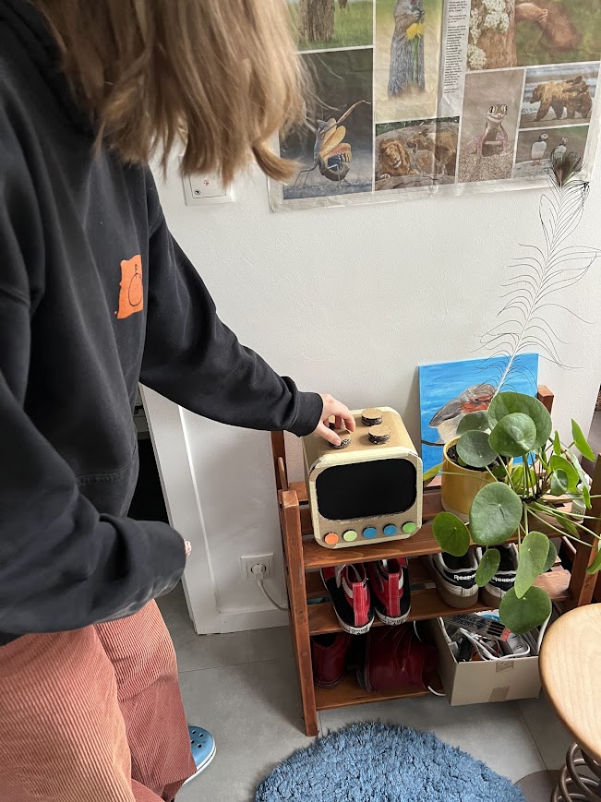
Images/IMG_6334.jpg
