WarreDV2004/UCD/Images/IMG_6335.jpg

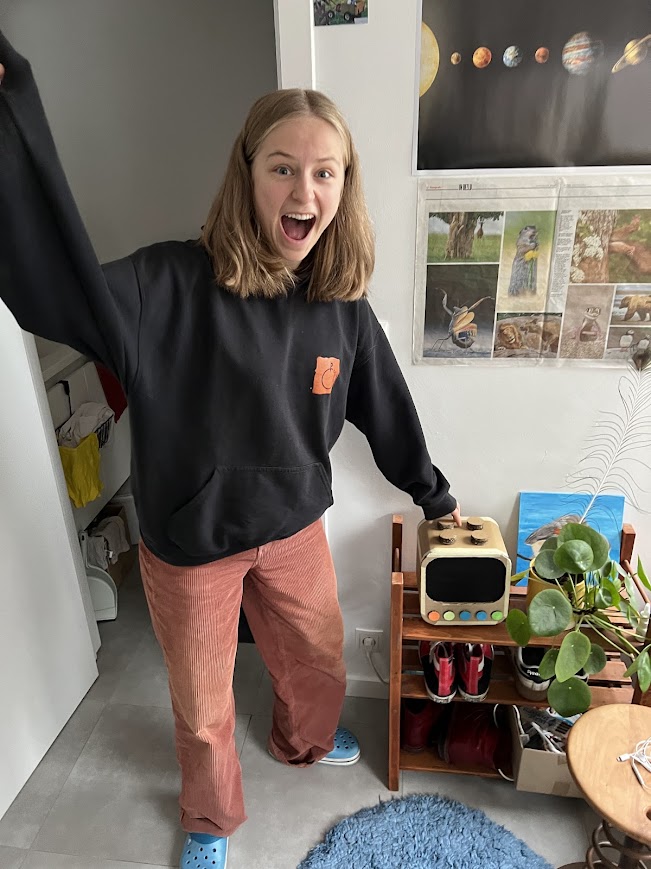
Images/IMG_6335.jpg
