WarreDV2004/UCD/Images/IMG_6336.jpg

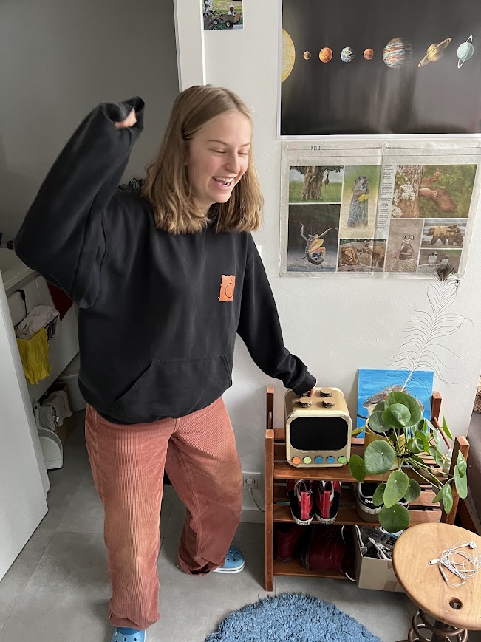
Images/IMG_6336.jpg
