WarreDV2004/UCD/Images/IMG_6337.jpg

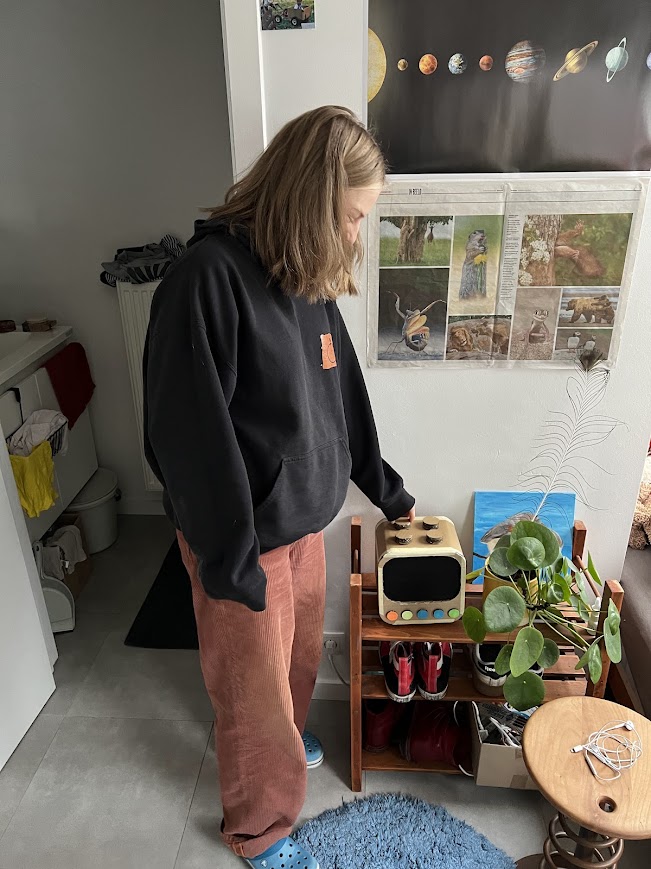
Images/IMG_6337.jpg
