WarreDV2004/UCD/Images/IMG_6338.jpg

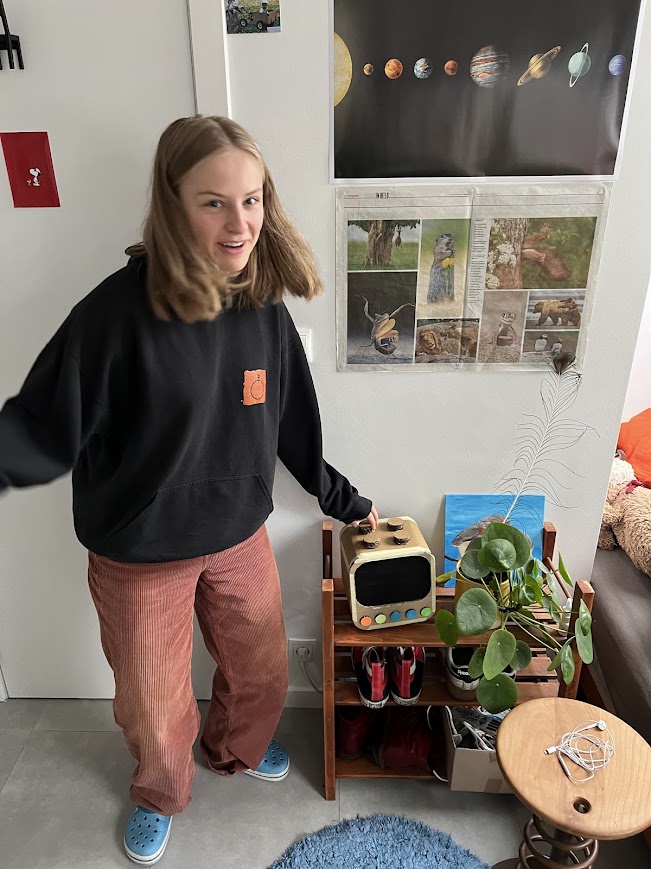
Images/IMG_6338.jpg
