WarreDV2004/UCD/Images/IMG_6339.jpg

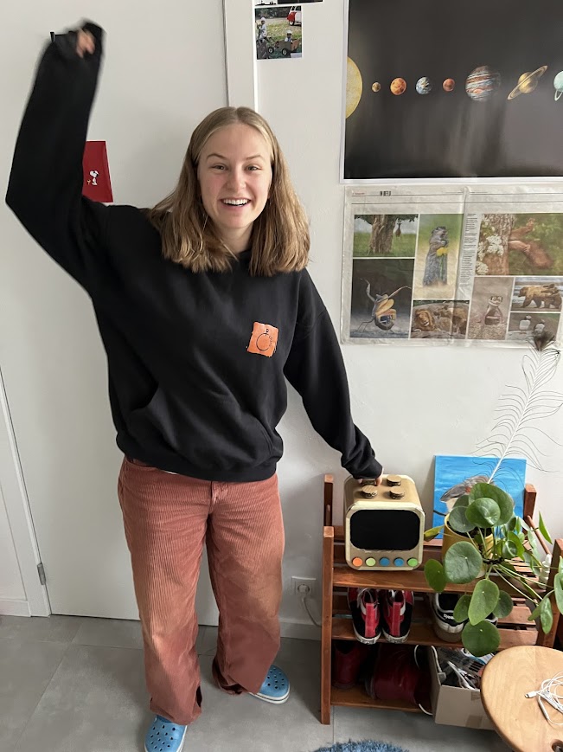
Images/IMG_6339.jpg
