WarreDV2004/UCD/Images/IMG_6340.jpg

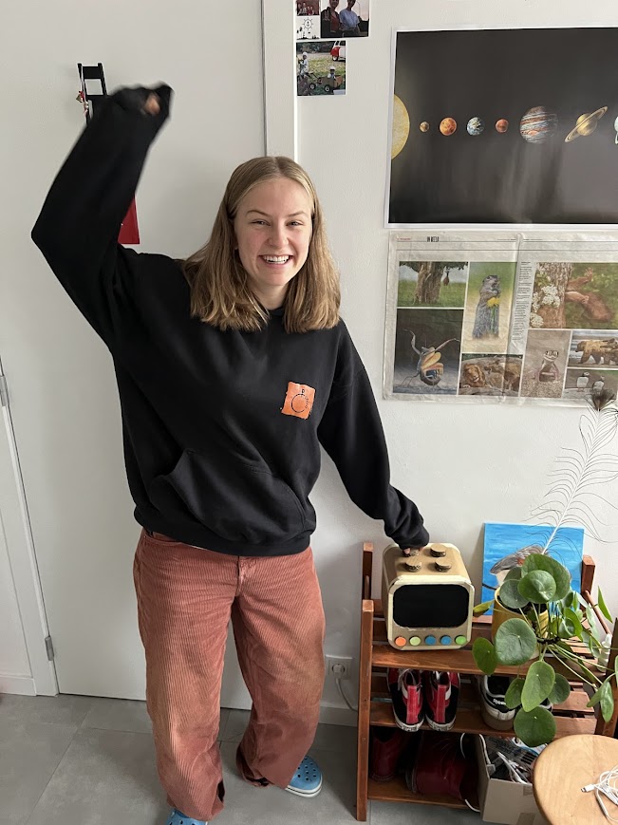
Images/IMG_6340.jpg
