WarreDV2004/UCD/Images/IMG_6341.jpg

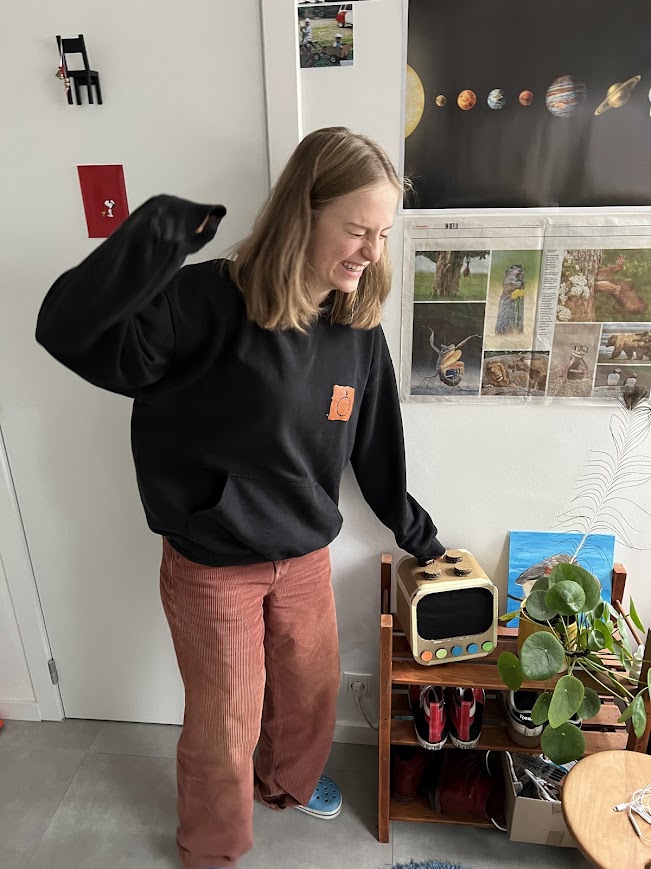
Images/IMG_6341.jpg
