WarreDV2004/UCD/Images/IMG_6342.jpg

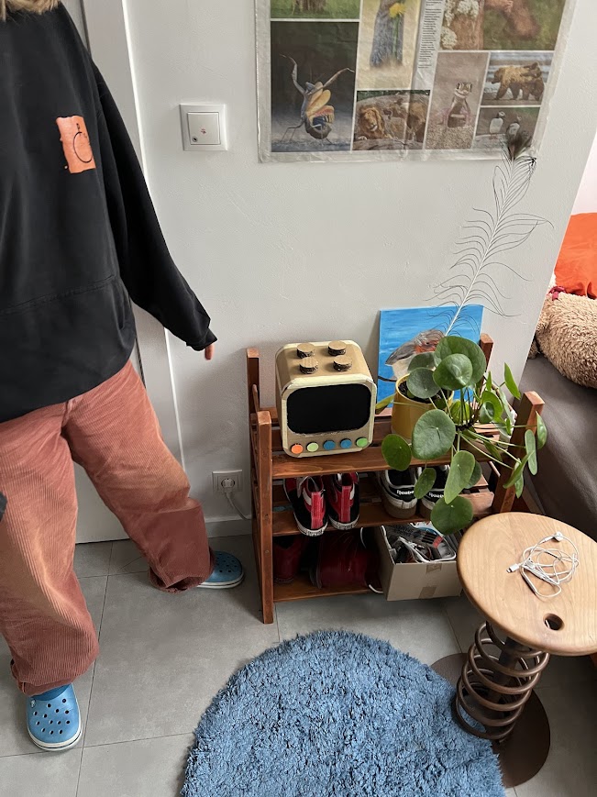
Images/IMG_6342.jpg
