WarreDV2004/UCD/Images/IMG_6343.jpg

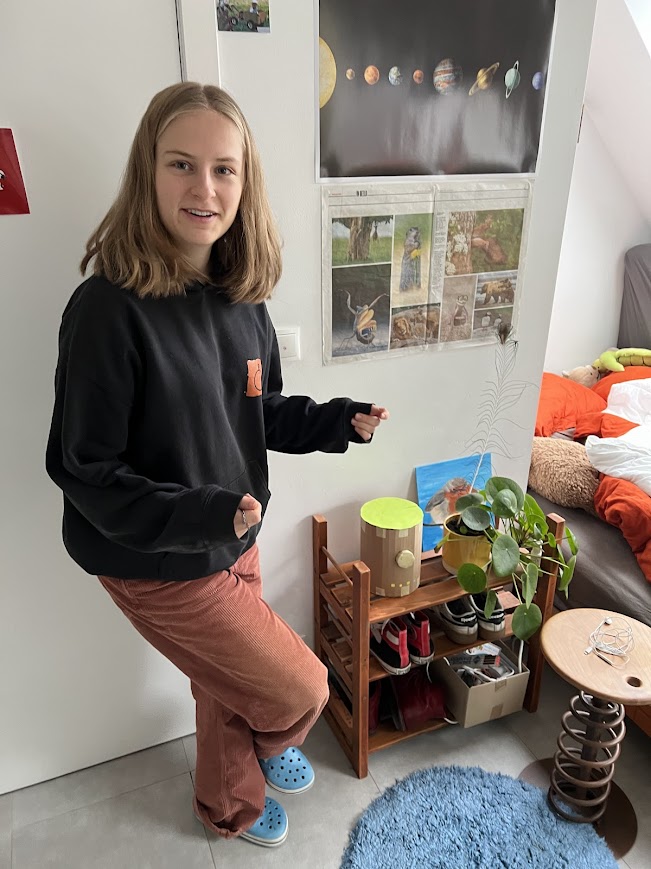
Images/IMG_6343.jpg
