WarreDV2004/UCD/Images/IMG_6344.jpg

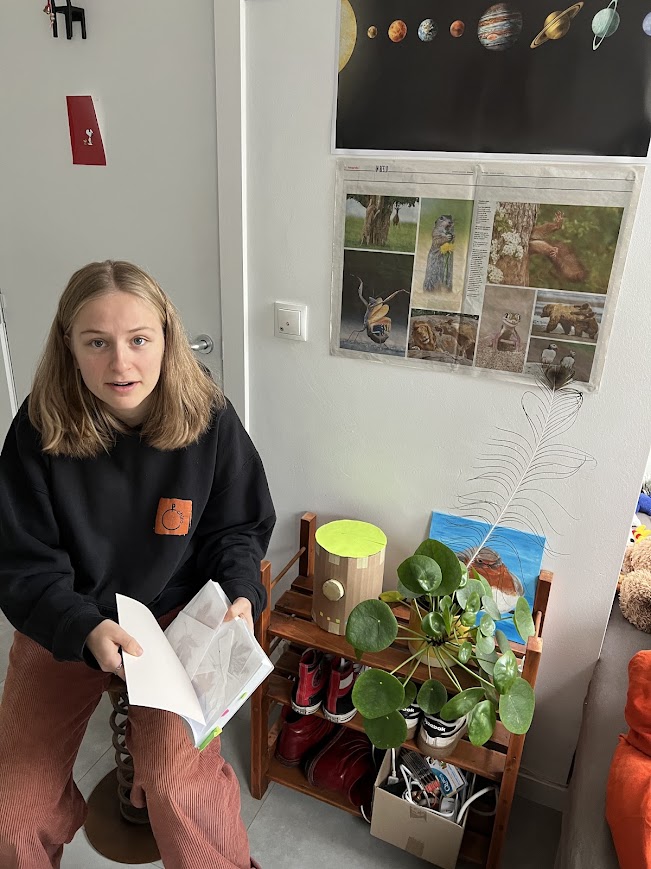
Images/IMG_6344.jpg
