WarreDV2004/UCD/Images/IMG_6345.jpg

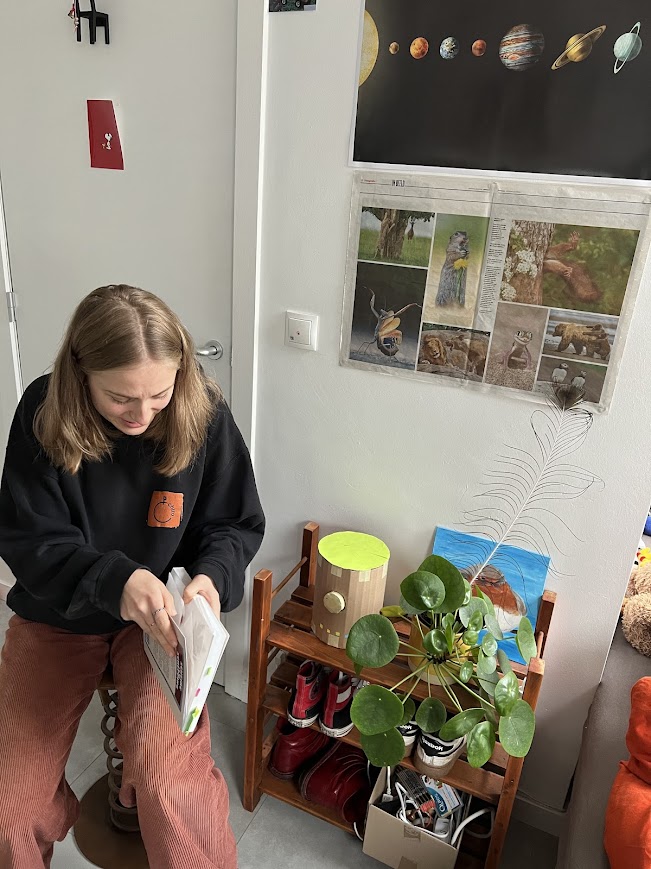
Images/IMG_6345.jpg
