WarreDV2004/UCD/Images/IMG_6346.jpg

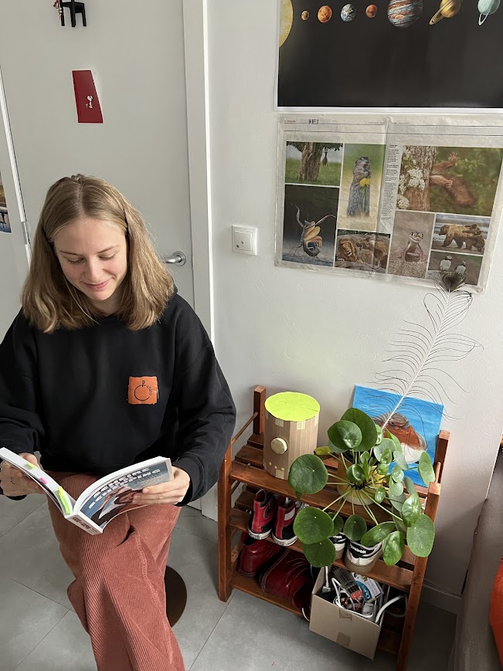
Images/IMG_6346.jpg
