WarreDV2004/UCD/Images/IMG_6347.jpg

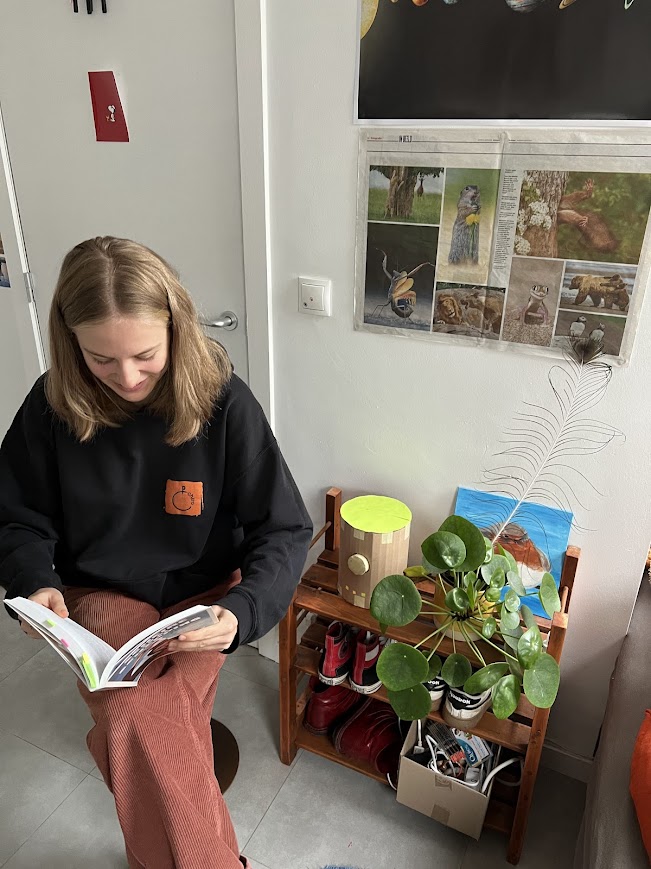
Images/IMG_6347.jpg
