WarreDV2004/UCD/Images/IMG_6348.jpg

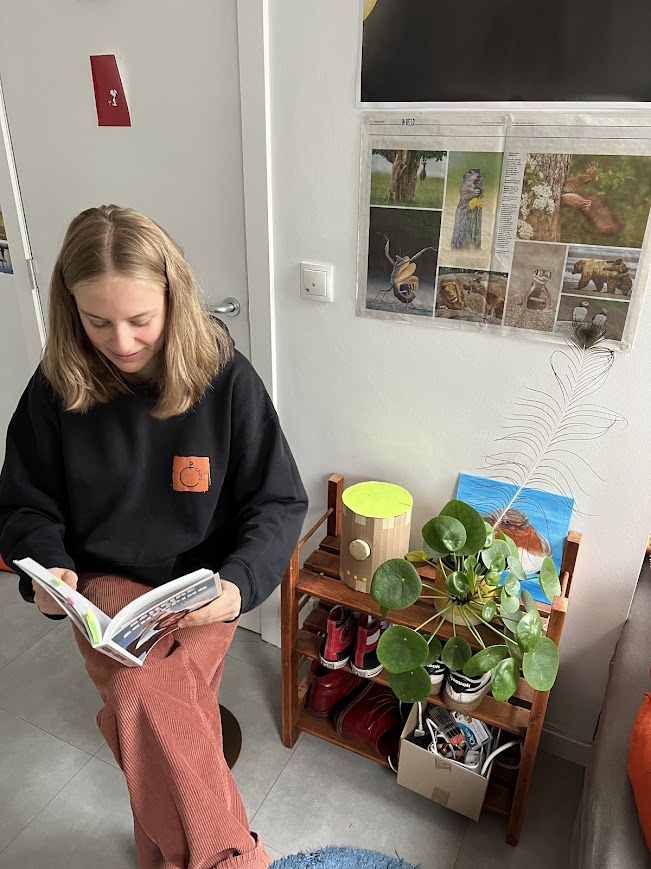
Images/IMG_6348.jpg
