WarreDV2004/UCD/Images/IMG_6349.jpg

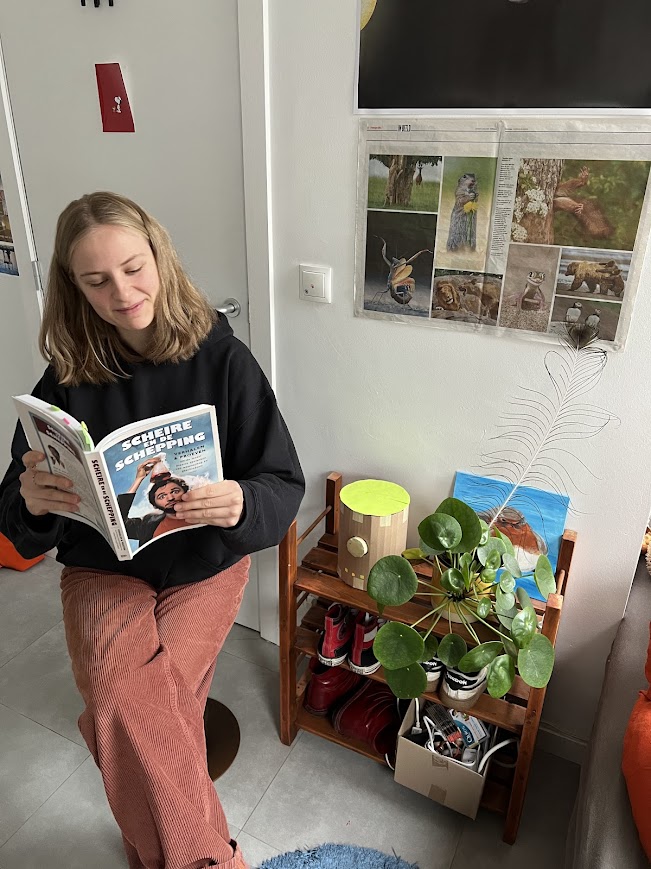
Images/IMG_6349.jpg
