WarreDV2004/UCD/Images/IMG_6351.jpg

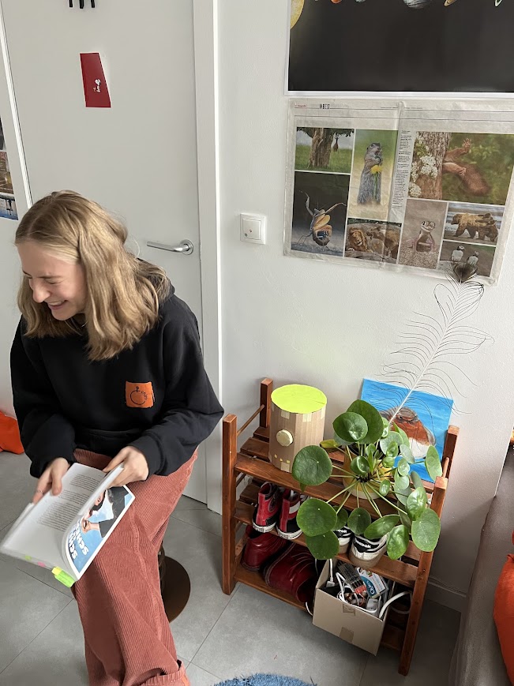
Images/IMG_6351.jpg
