WarreDV2004/UCD/Images/IMG_6352.jpg

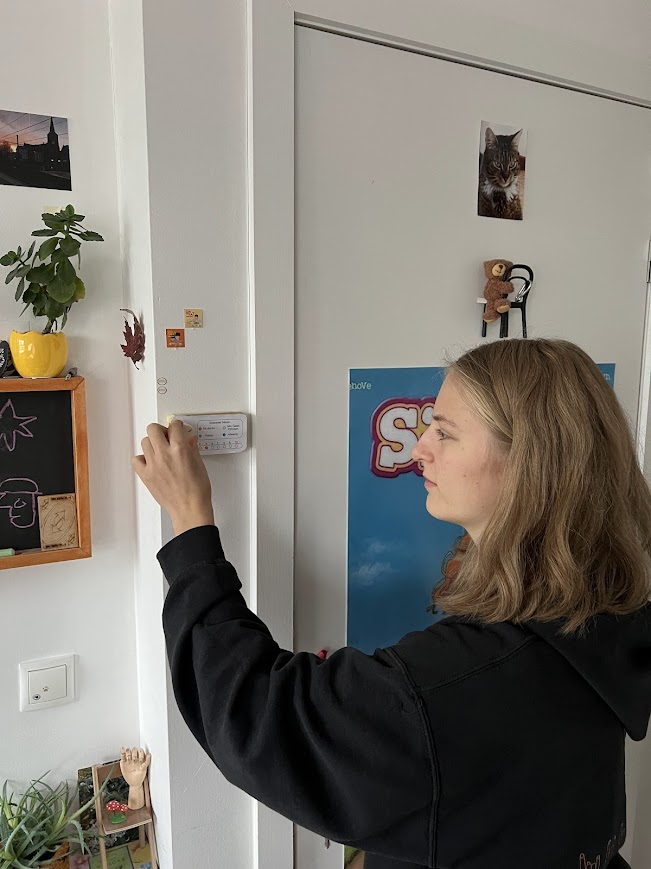
Images/IMG_6352.jpg
