WarreDV2004/UCD/Images/IMG_6353.jpg

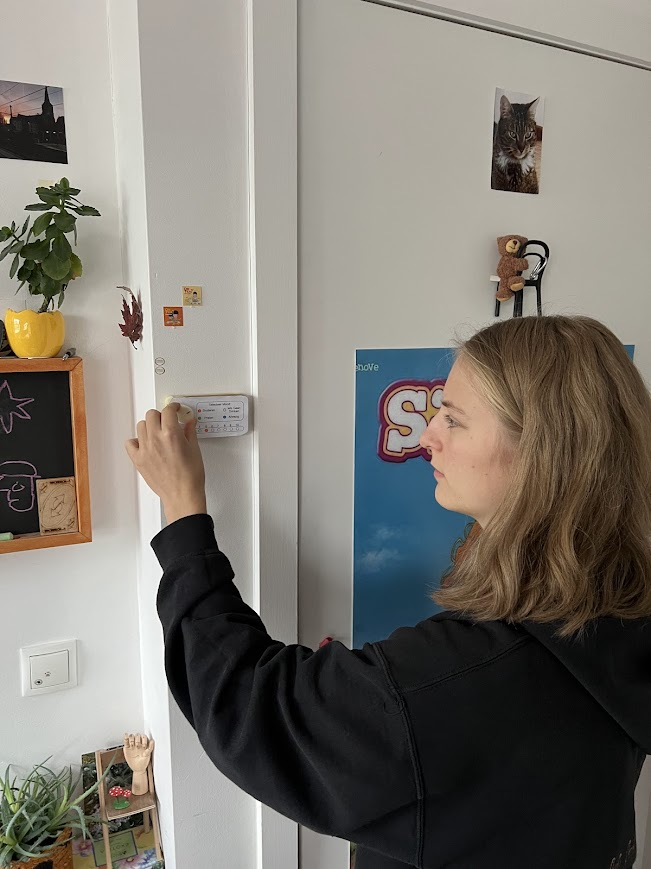
Images/IMG_6353.jpg
