WarreDV2004/UCD/Images/IMG_6354.jpg

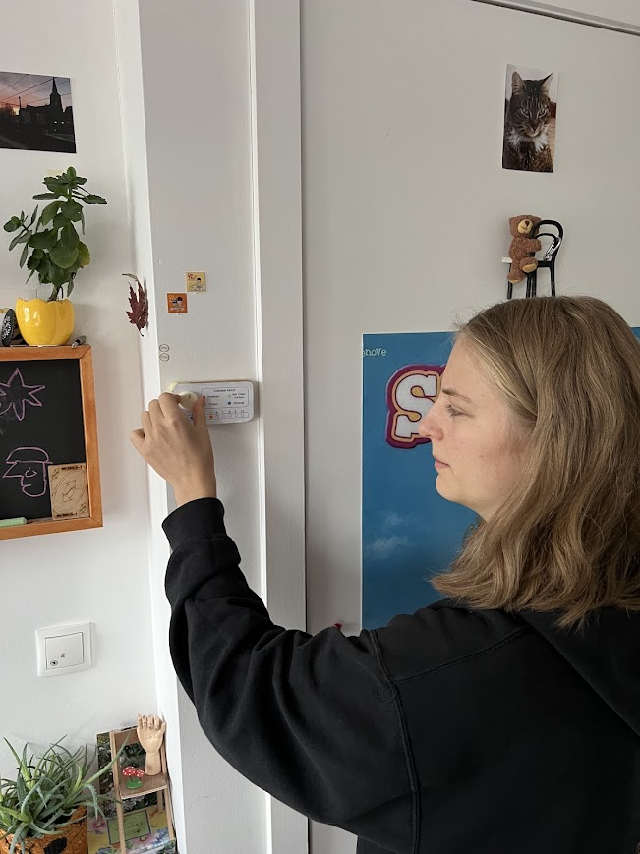
Images/IMG_6354.jpg
