WarreDV2004/UCD/Images/IMG_6355.jpg

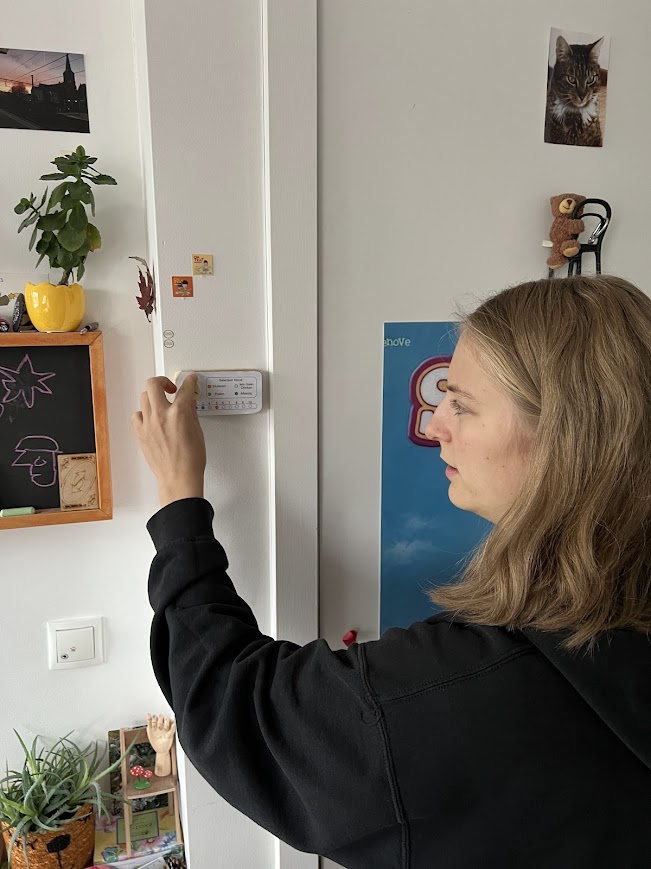
Images/IMG_6355.jpg
