WarreDV2004/UCD/Images/IMG_6356.jpg

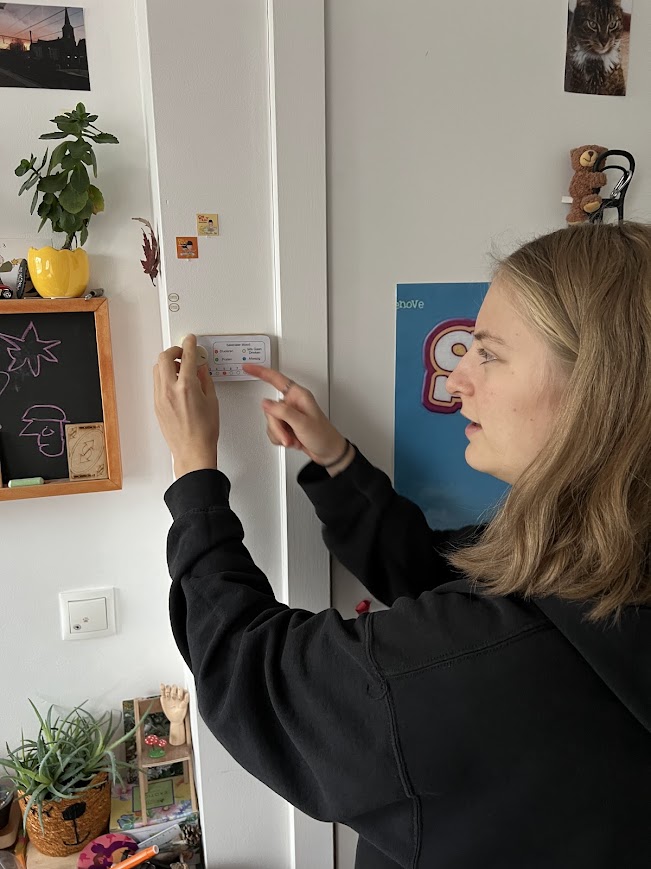
Images/IMG_6356.jpg
