WarreDV2004/UCD/Images/IMG_6357.jpg

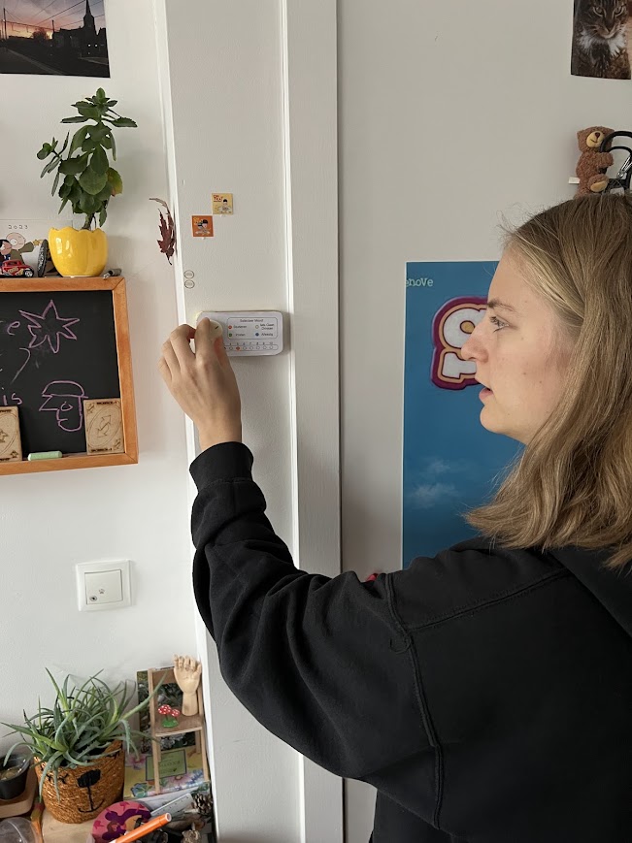
Images/IMG_6357.jpg
