WarreDV2004/UCD/Images/IMG_6358.jpg

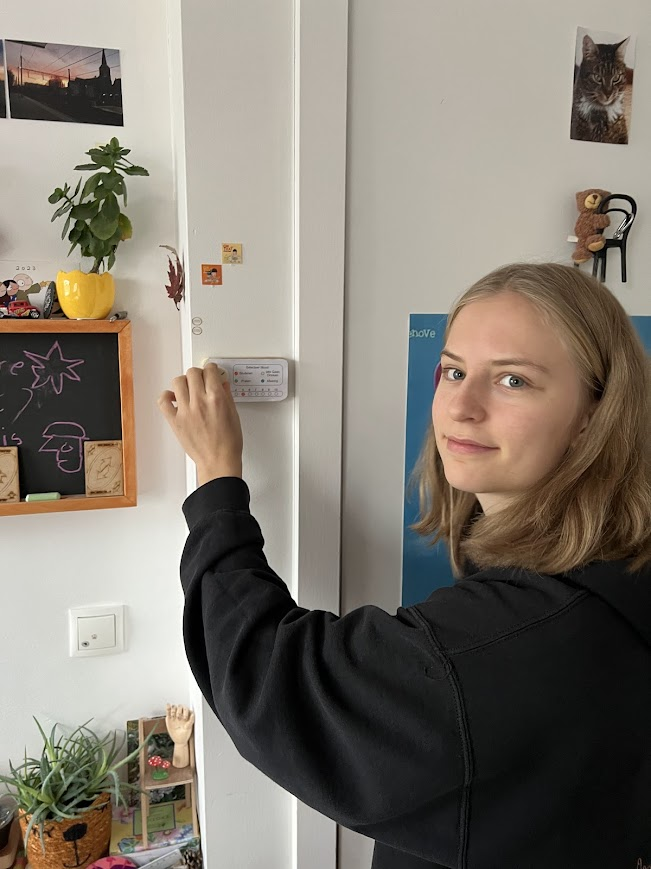
Images/IMG_6358.jpg
