WarreDV2004/UCD/Images/IMG_6359.jpg

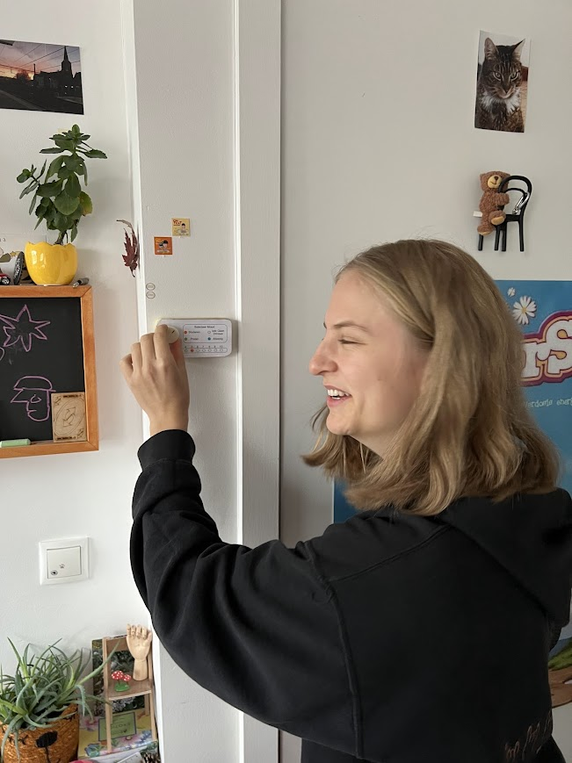
Images/IMG_6359.jpg
