WarreDV2004/UCD/Images/IMG_6360.jpg

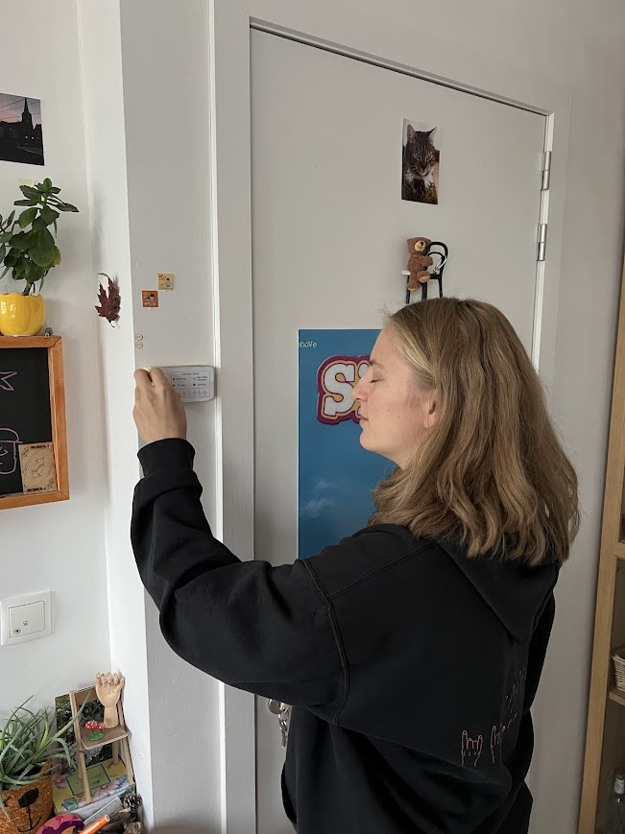
Images/IMG_6360.jpg
