WarreDV2004/UCD/Images/IMG_6361.jpg

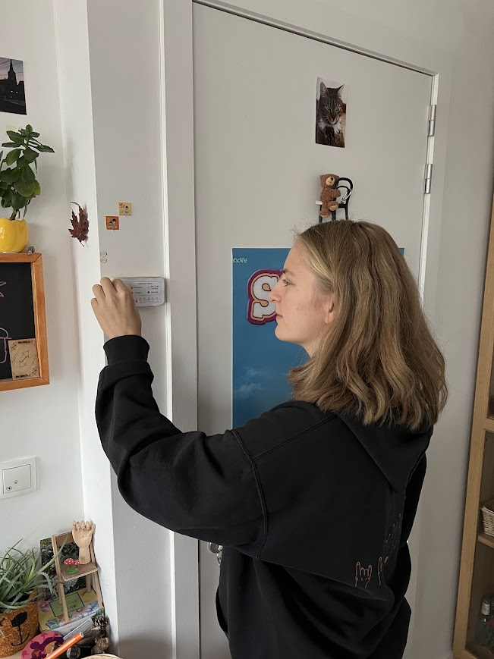
Images/IMG_6361.jpg
