WarreDV2004/UCD/Images/IMG_6362.jpg

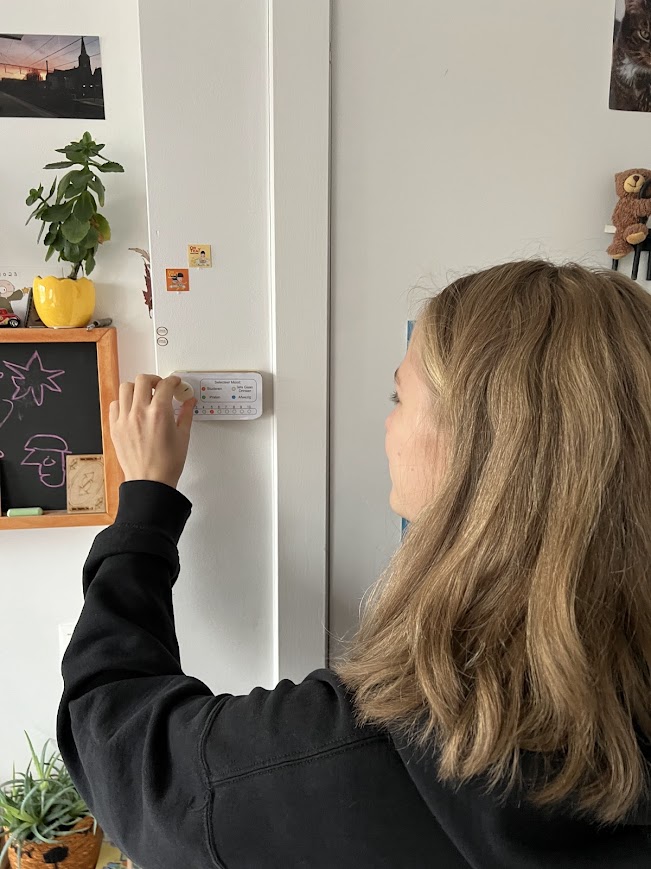
Images/IMG_6362.jpg
