WarreDV2004/UCD/Images/IMG_6363.jpg

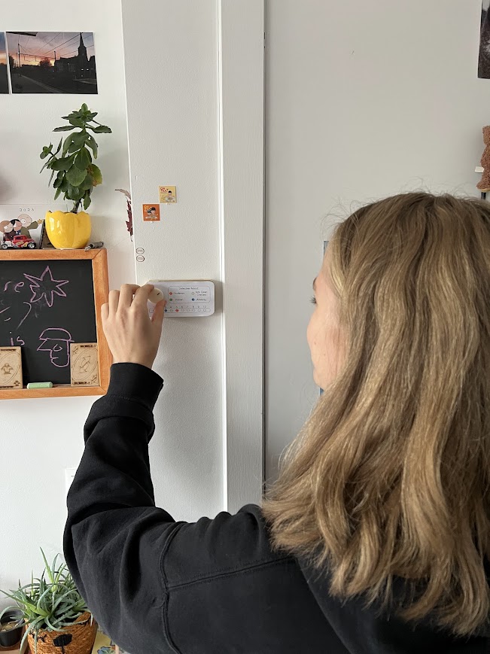
Images/IMG_6363.jpg
