WarreDV2004/UCD/Images/IMG_6365.jpg

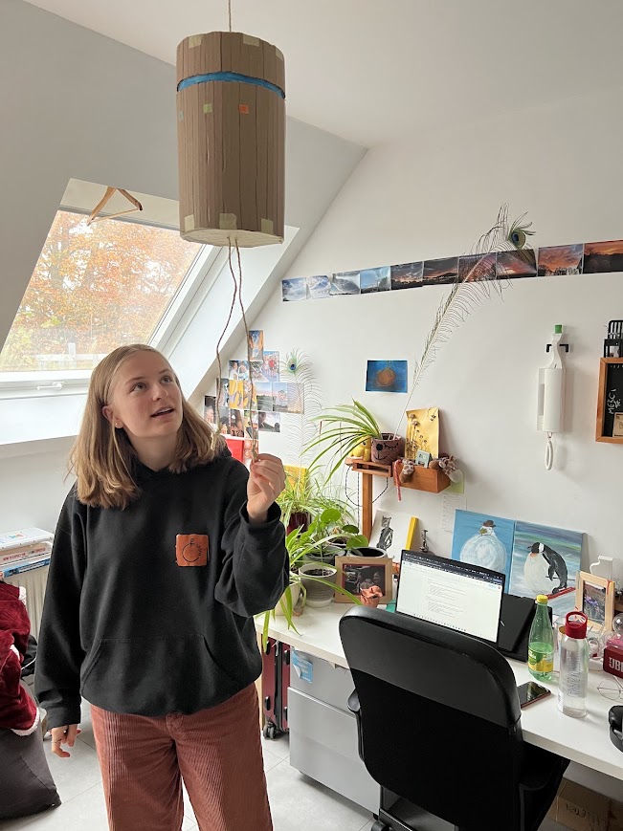
Images/IMG_6365.jpg
