WarreDV2004/UCD/Images/IMG_6367.jpg

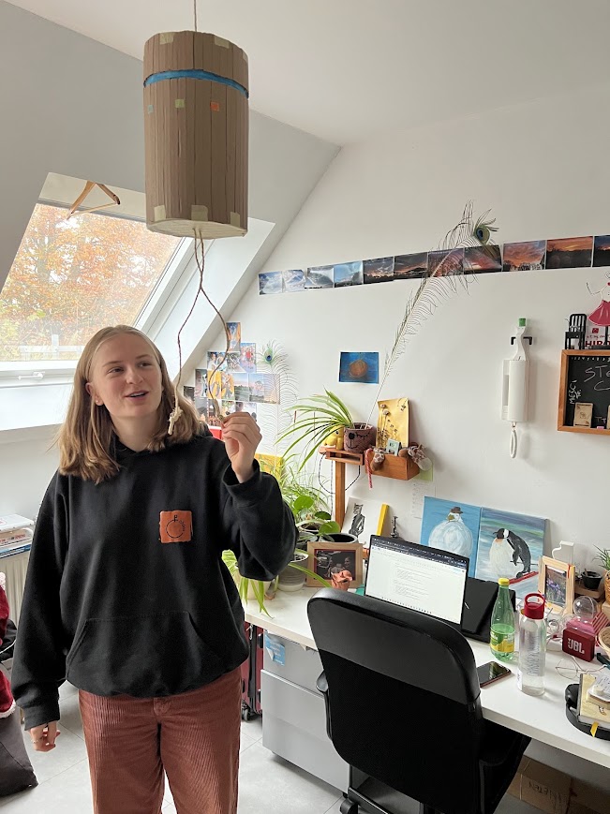
Images/IMG_6367.jpg
