WarreDV2004/UCD/Images/IMG_6369.jpg

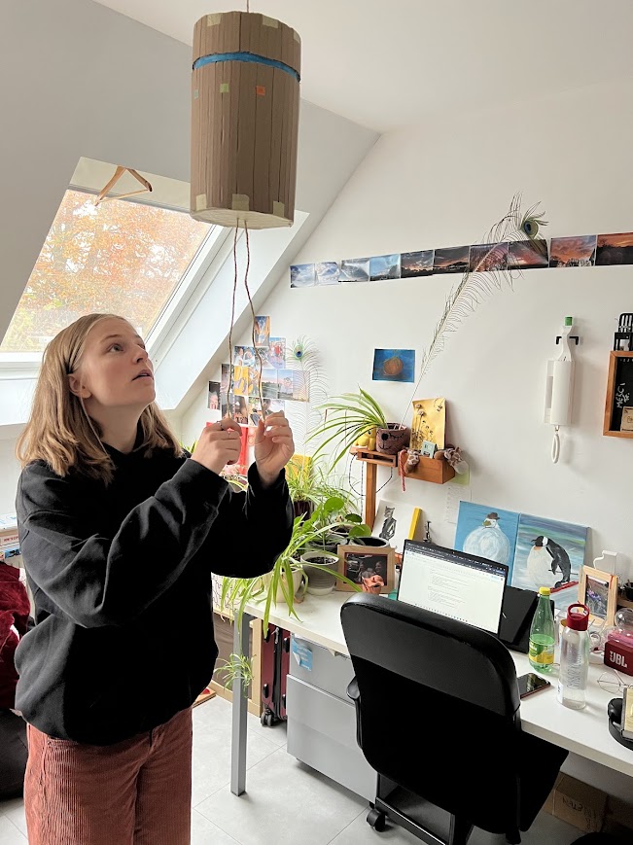
Images/IMG_6369.jpg
