WarreDV2004/UCD/Images/IMG_6373.jpg

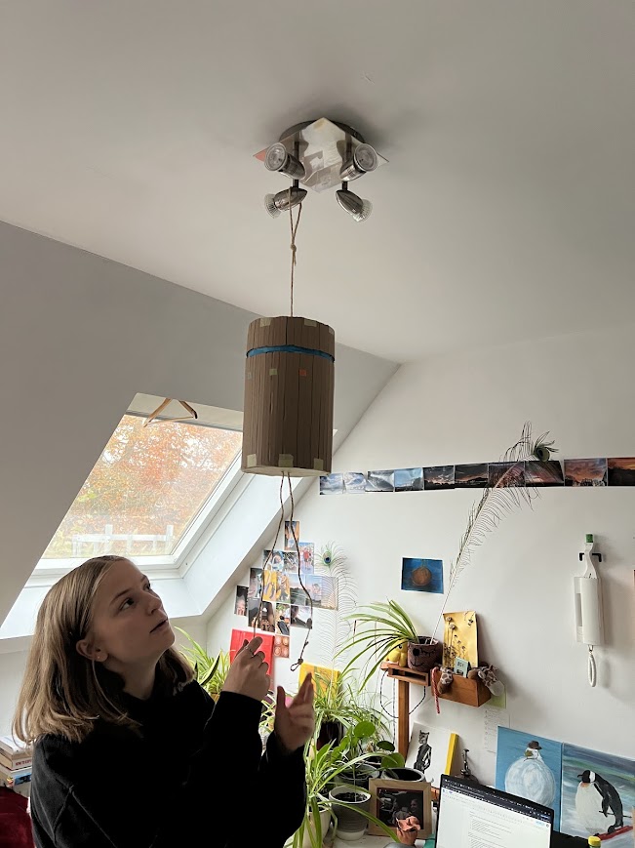
Images/IMG_6373.jpg
