WarreDV2004/UCD/Images/IMG_6374.jpg

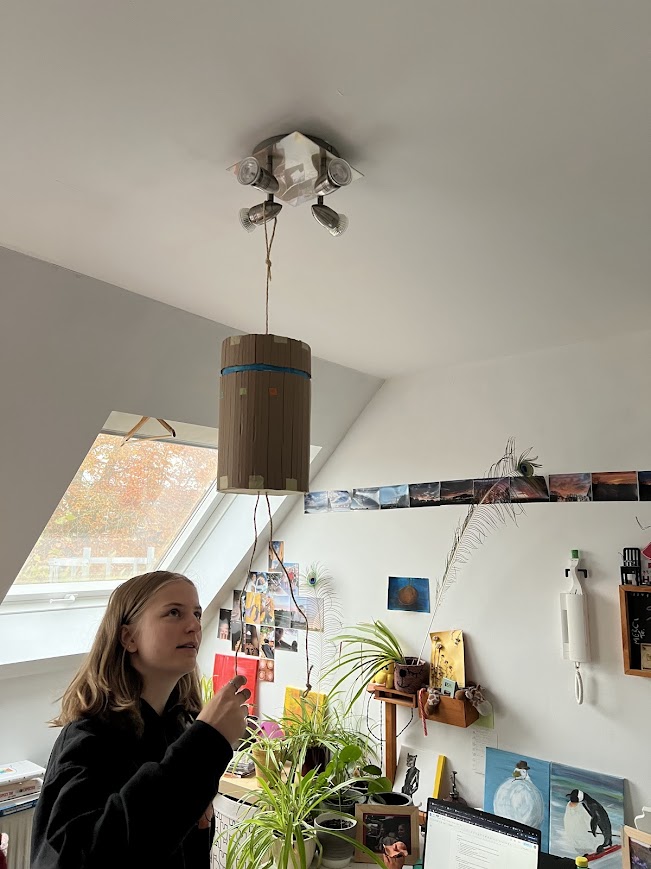
Images/IMG_6374.jpg
