WarreDV2004/UCD/Images/IMG_6375.jpg

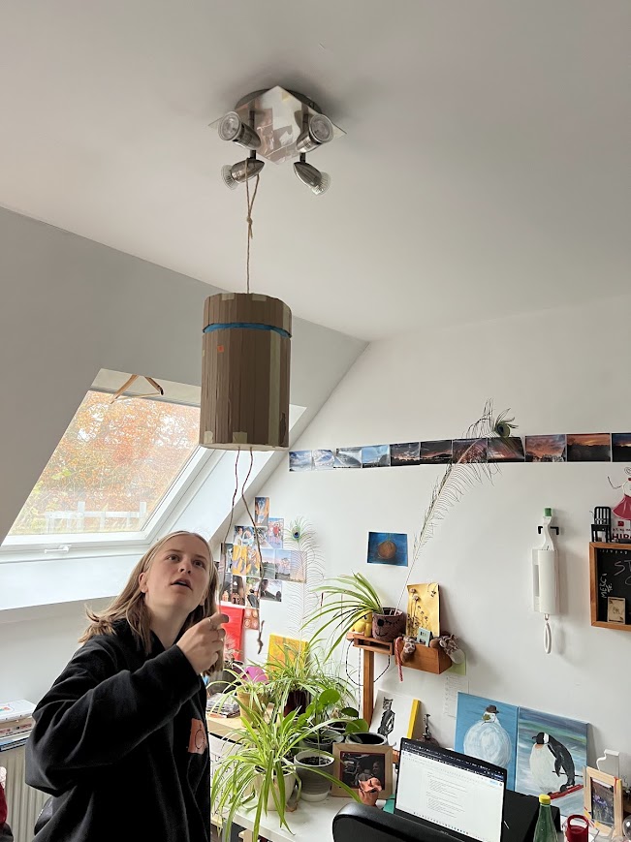
Images/IMG_6375.jpg
