WarreDV2004/UCD/Images/IMG_6376.jpg

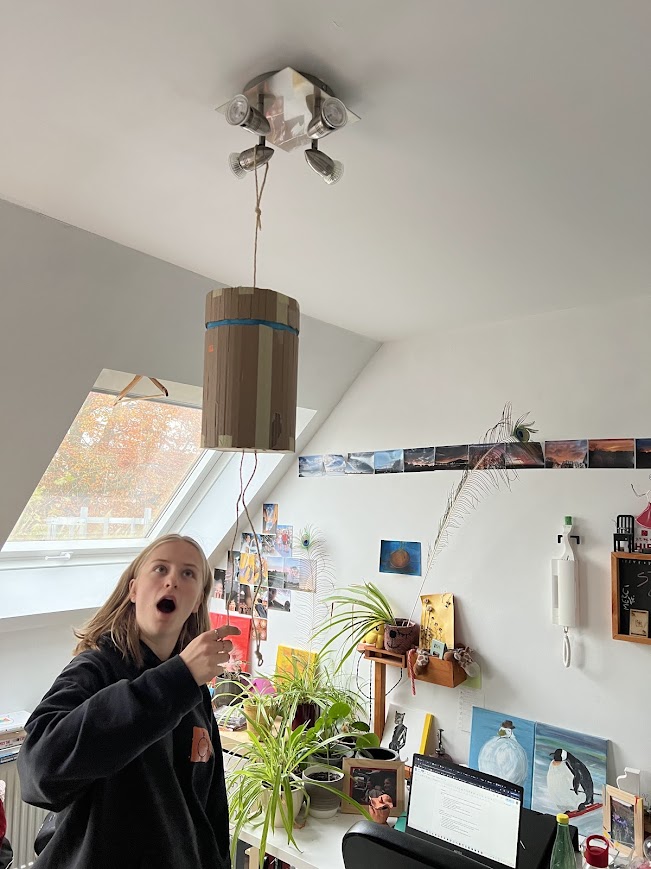
Images/IMG_6376.jpg
