WarreDV2004/UCD/Images/IMG_6377.jpg

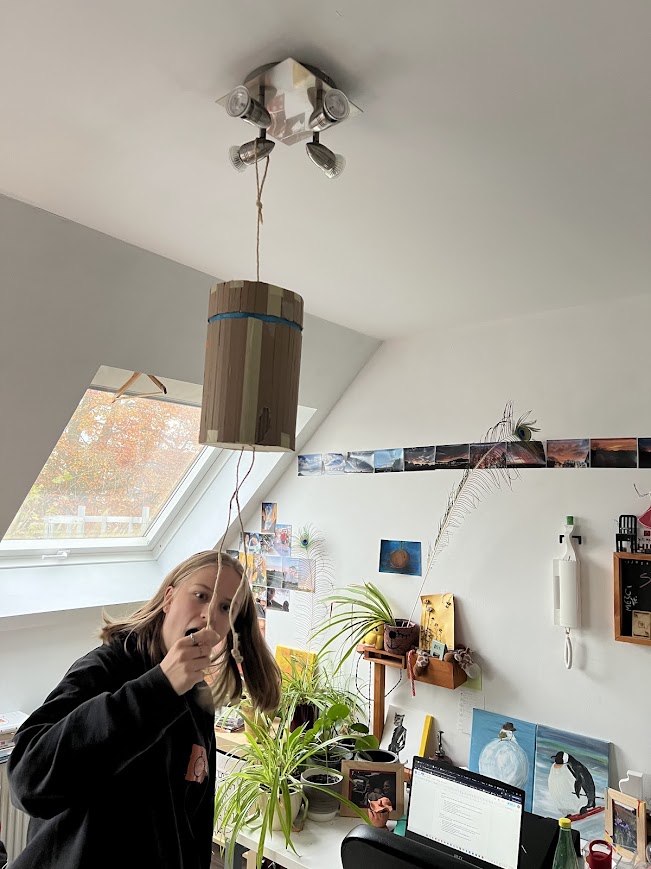
Images/IMG_6377.jpg
