WarreDV2004/UCD/Images/IMG_6378.jpg

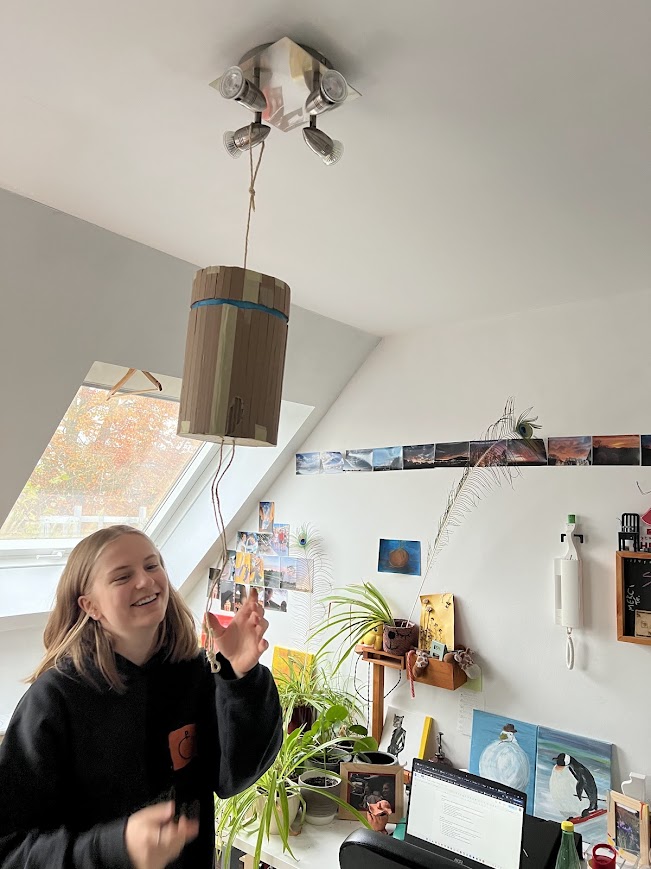
Images/IMG_6378.jpg
