WarreDV2004/UCD/Images/IMG_6431.jpg

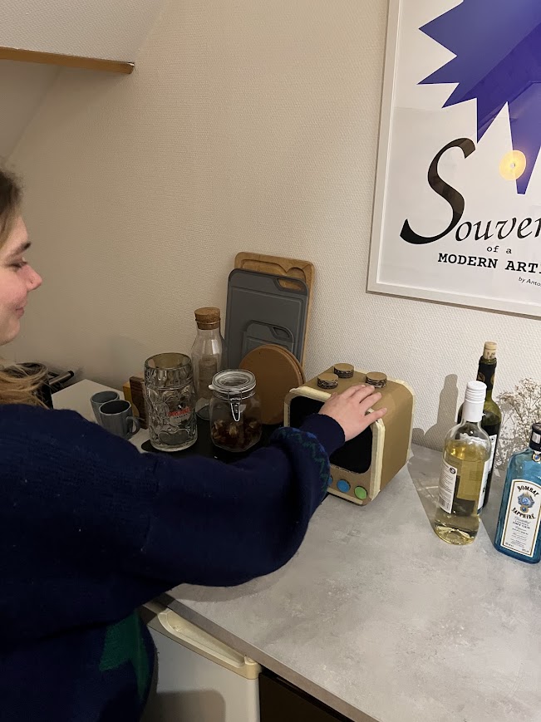
Images/IMG_6431.jpg
