WarreDV2004/UCD/Images/IMG_6432.jpg

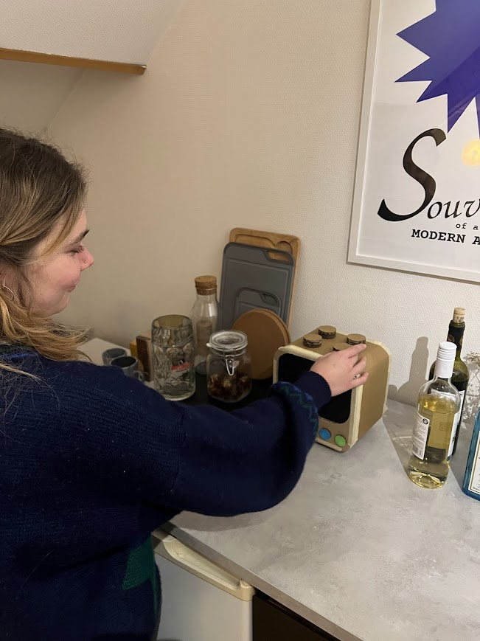
Images/IMG_6432.jpg
