WarreDV2004/UCD/Images/IMG_6436.jpg

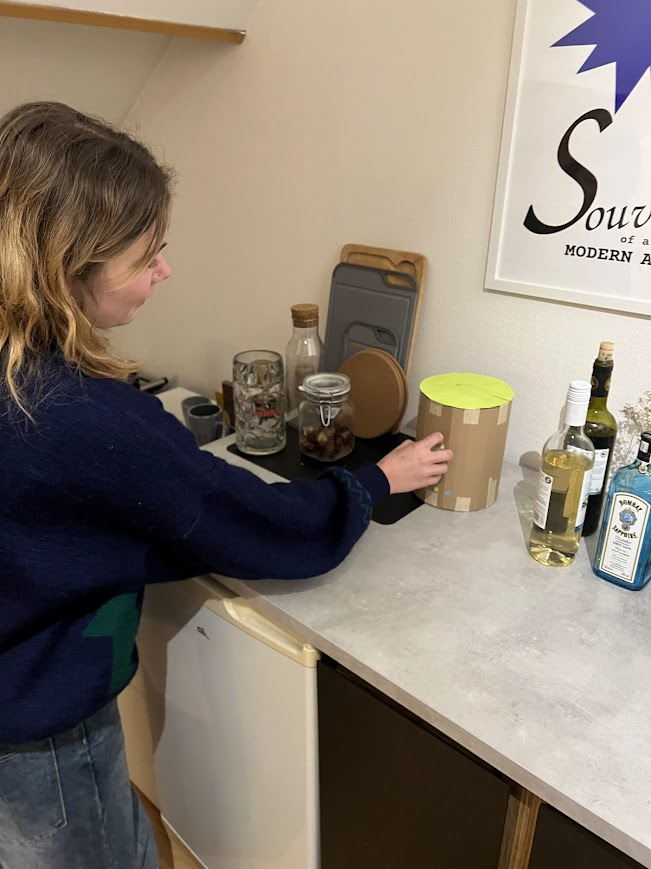
Images/IMG_6436.jpg
