WarreDV2004/UCD/Images/IMG_6437.jpg

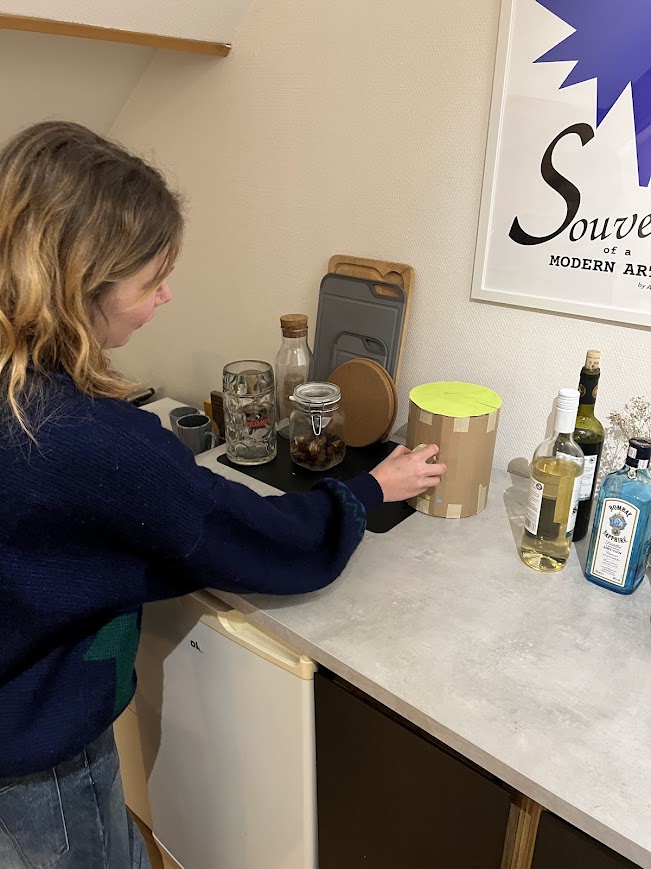
Images/IMG_6437.jpg
