WarreDV2004/UCD/Images/IMG_6438.jpg

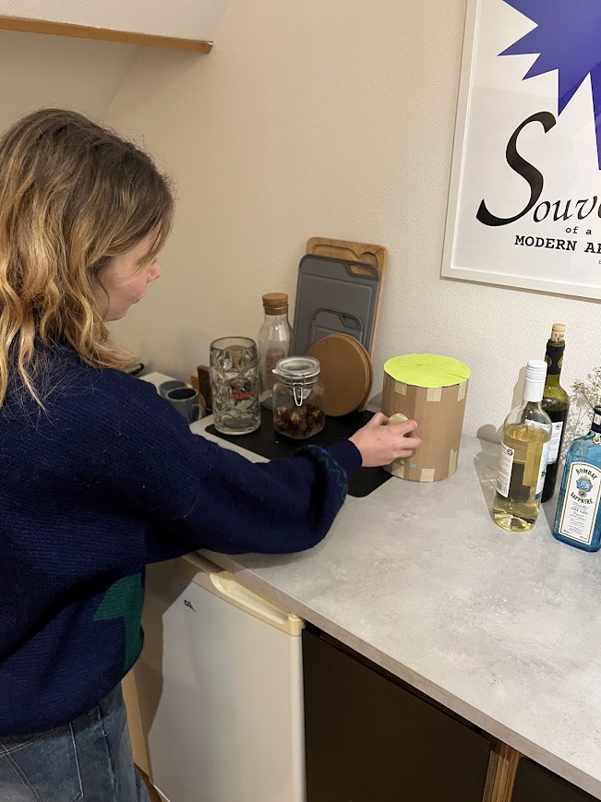
Images/IMG_6438.jpg
