WarreDV2004/UCD/Images/IMG_6440.jpg

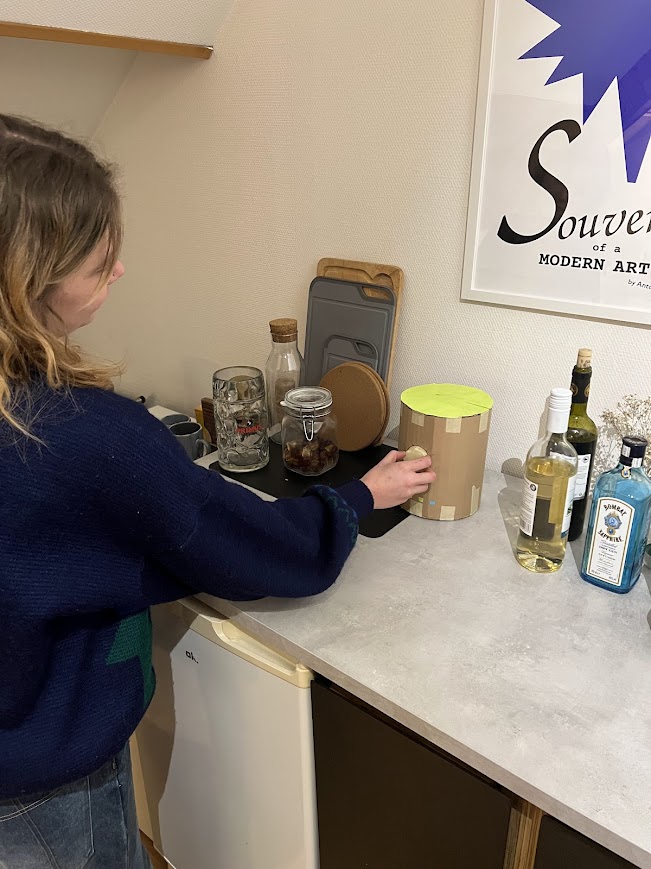
Images/IMG_6440.jpg
