WarreDV2004/UCD/Images/IMG_6444.jpg

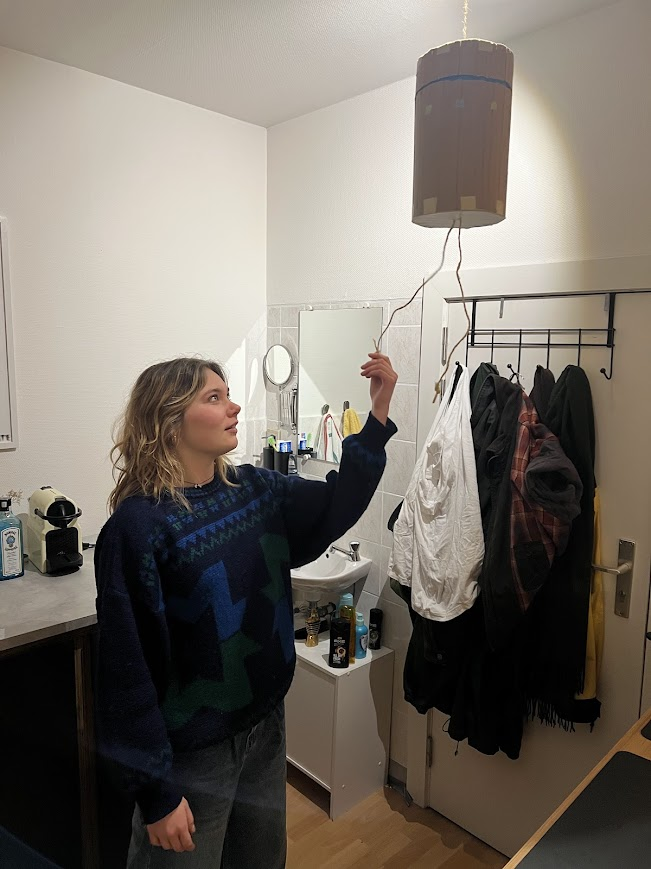
Images/IMG_6444.jpg
