WarreDV2004/UCD/Images/IMG_6445.jpg

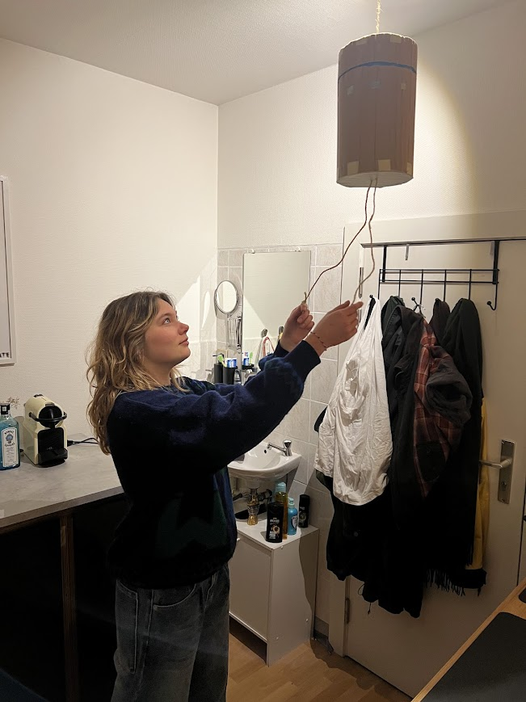
Images/IMG_6445.jpg
