WarreDV2004/UCD/Images/IMG_6448.jpg

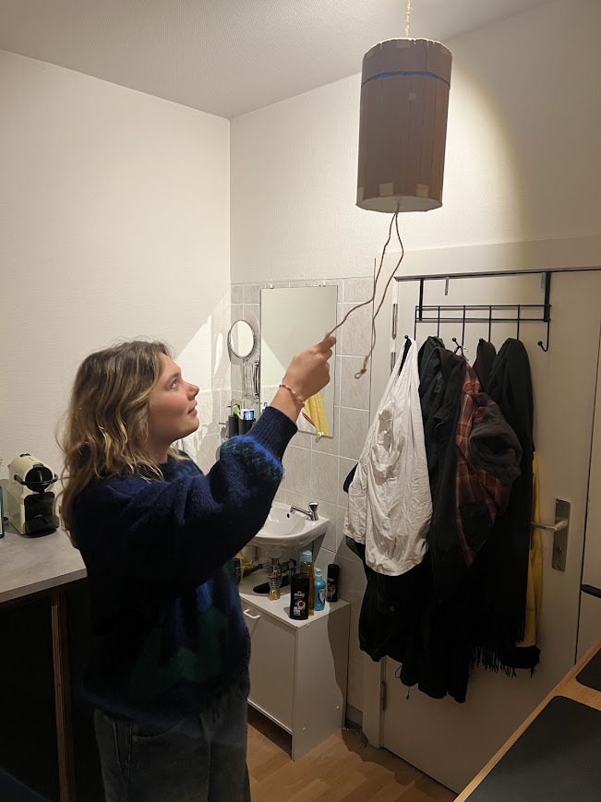
Images/IMG_6448.jpg
