WarreDV2004/UCD/Images/IMG_6452.jpg

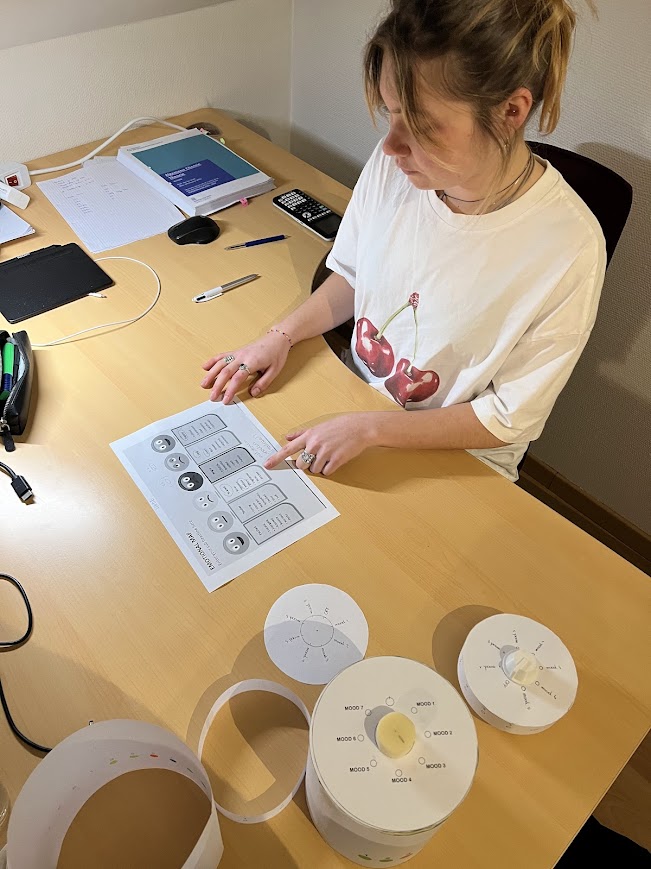
Images/IMG_6452.jpg
