WarreDV2004/UCD/Images/IMG_6455.jpg

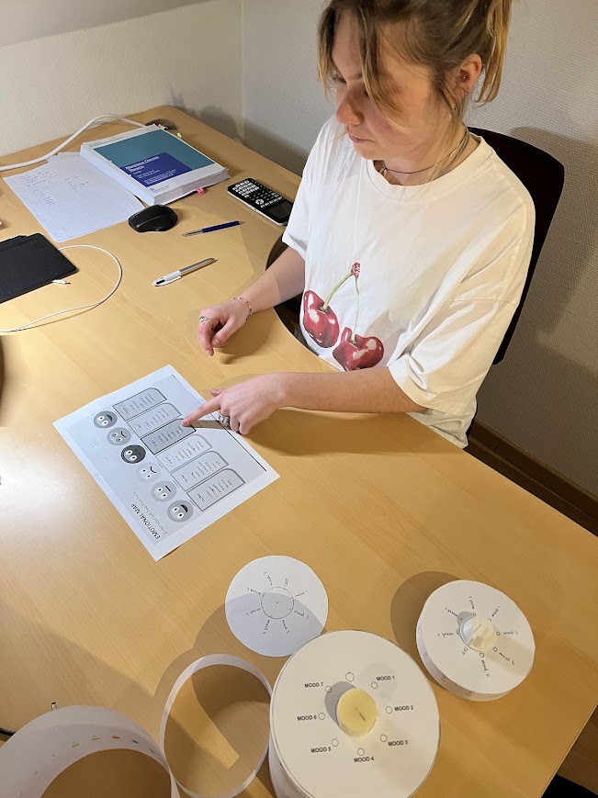
Images/IMG_6455.jpg
