WarreDV2004/UCD/Images/IMG_6460.jpg

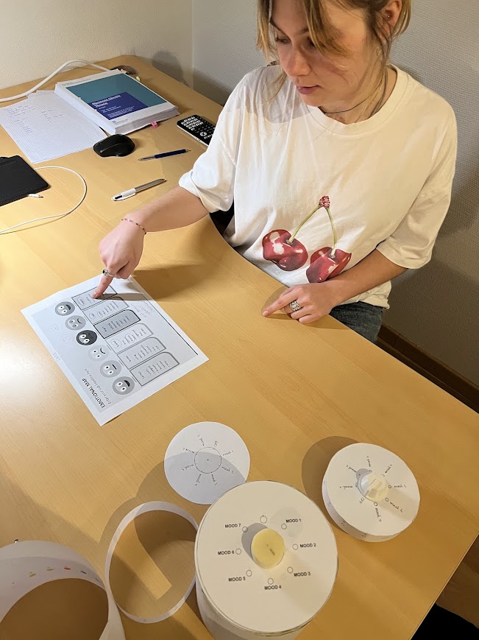
Images/IMG_6460.jpg
