WarreDV2004/UCD/Images/IMG_6462.jpg

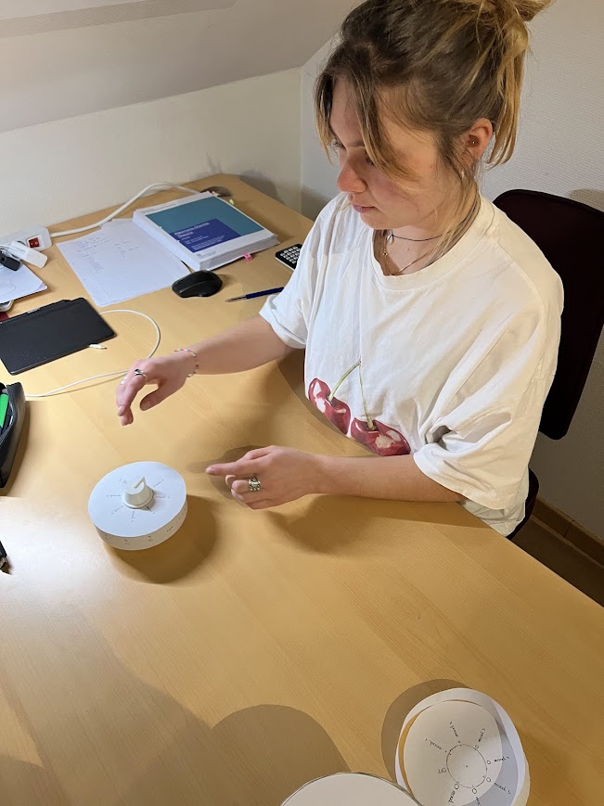
Images/IMG_6462.jpg
