WarreDV2004/UCD/Images/IMG_6463.jpg

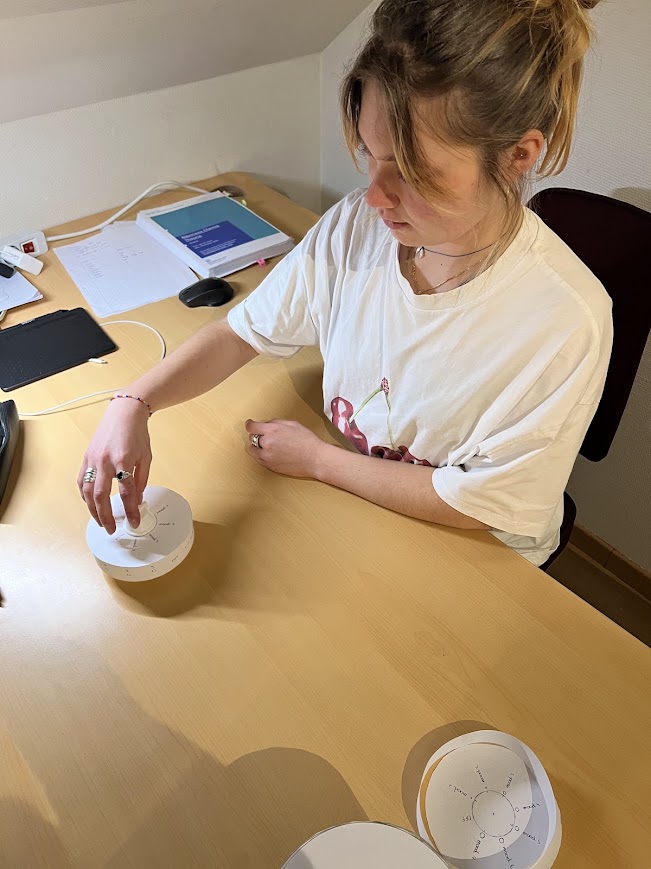
Images/IMG_6463.jpg
