WarreDV2004/UCD/Images/IMG_6464.jpg

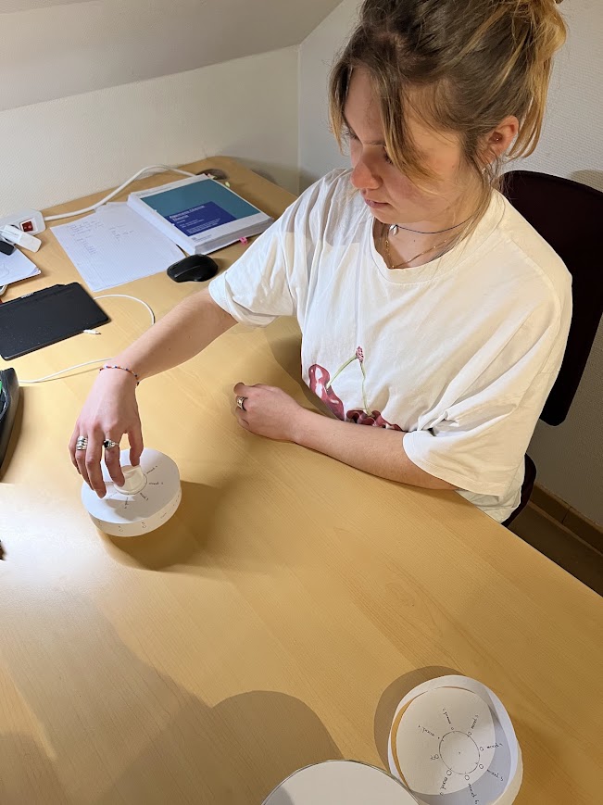
Images/IMG_6464.jpg
