WarreDV2004/UCD/Images/IMG_6465.jpg

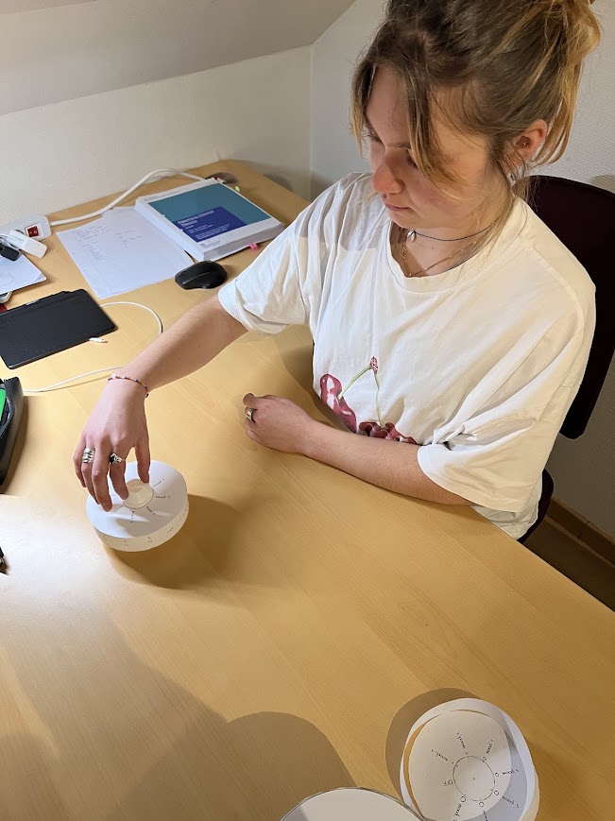
Images/IMG_6465.jpg
