WarreDV2004/UCD/Images/IMG_6466.jpg

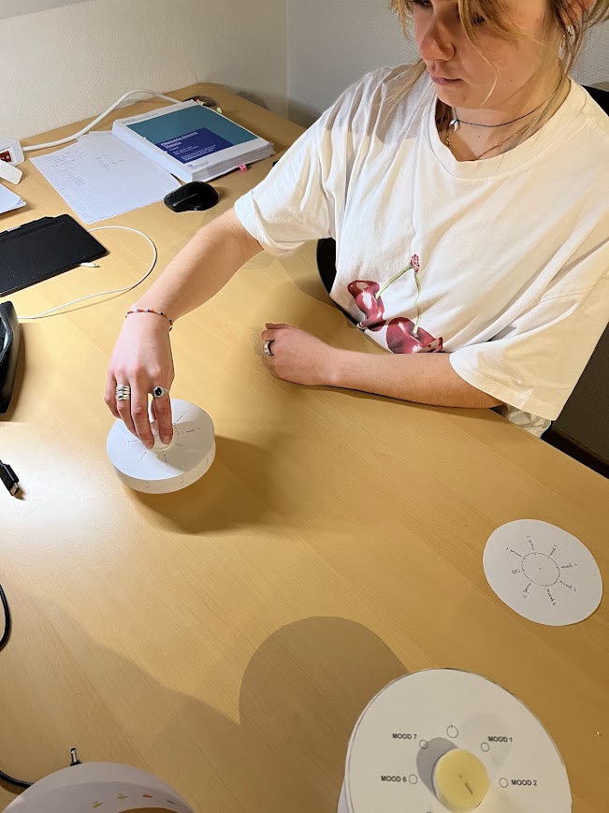
Images/IMG_6466.jpg
