WarreDV2004/UCD/Images/IMG_6467.jpg

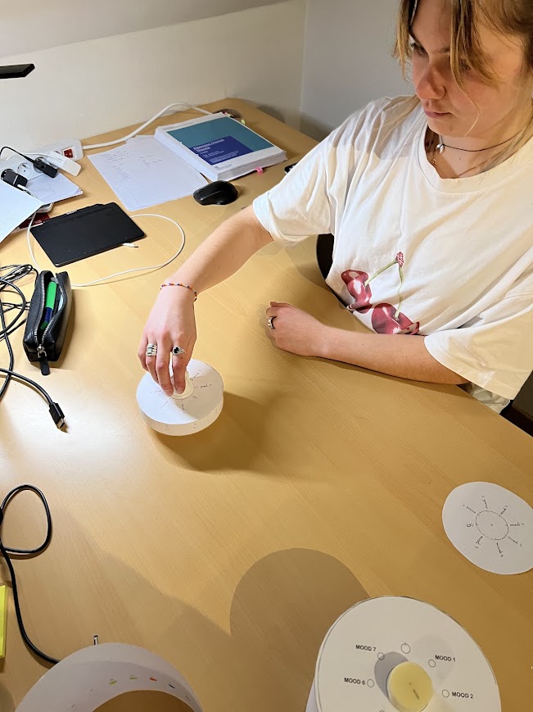
Images/IMG_6467.jpg
