WarreDV2004/UCD/Images/IMG_6468.jpg

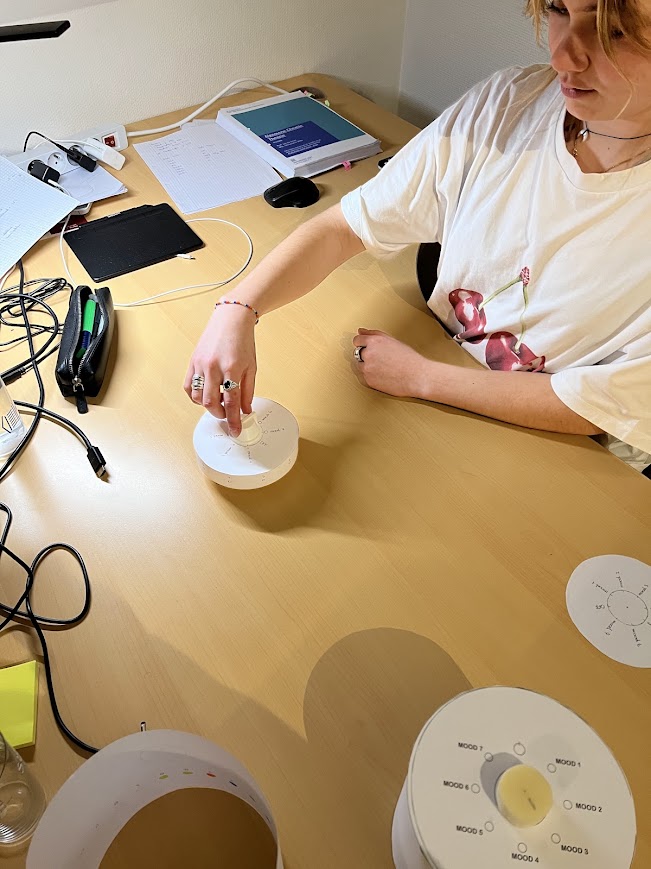
Images/IMG_6468.jpg
