WarreDV2004/UCD/Images/IMG_6469.jpg

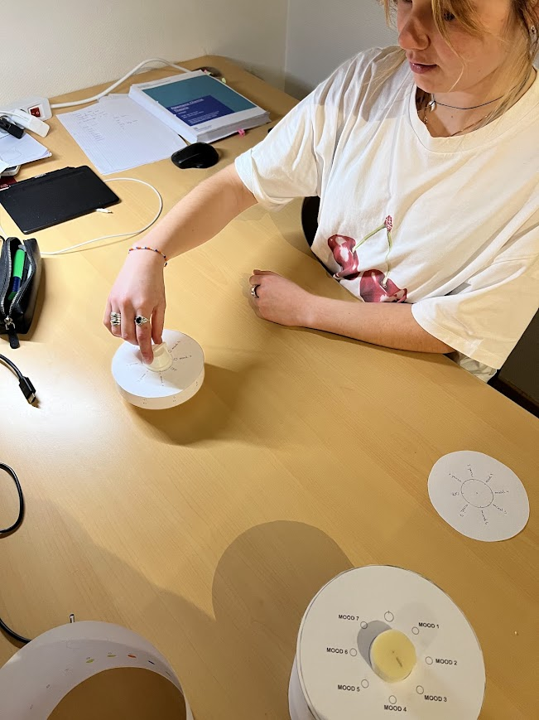
Images/IMG_6469.jpg
