WarreDV2004/UCD/Images/IMG_6470.jpg

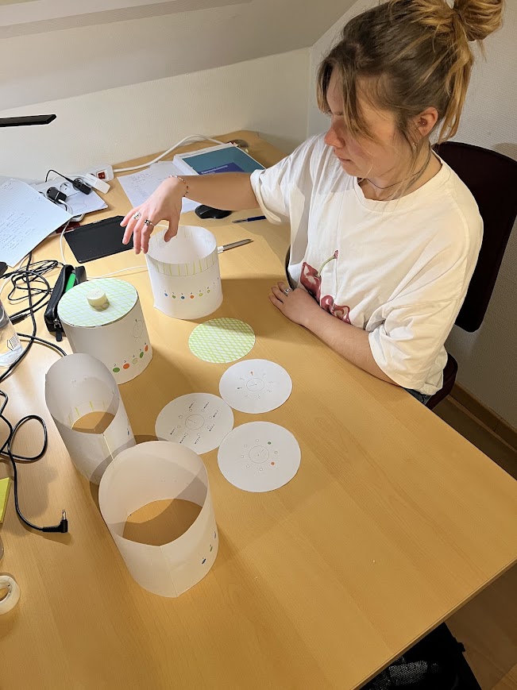
Images/IMG_6470.jpg
