WarreDV2004/UCD/Images/IMG_6471.jpg

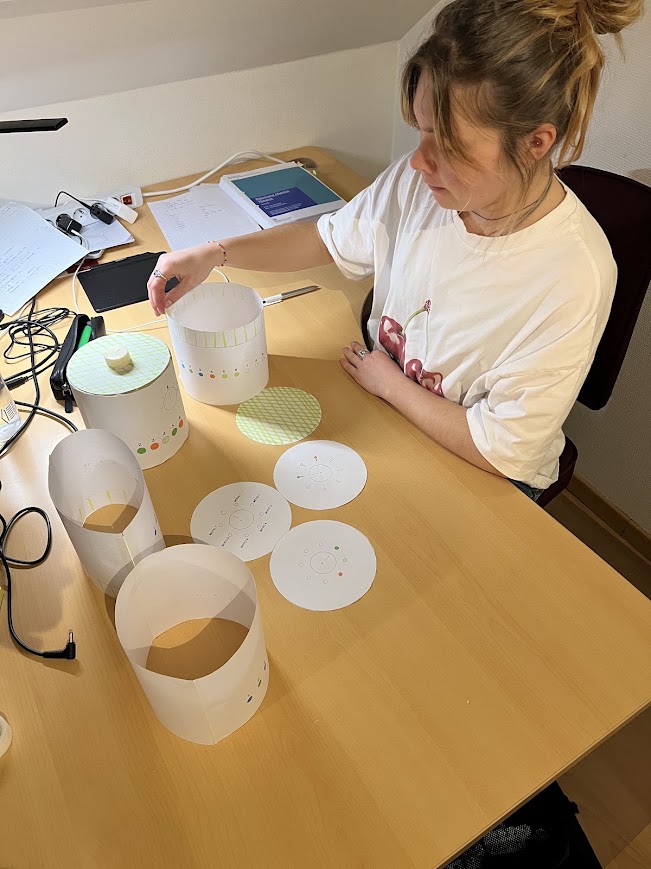
Images/IMG_6471.jpg
