WarreDV2004/UCD/Images/IMG_6472.jpg

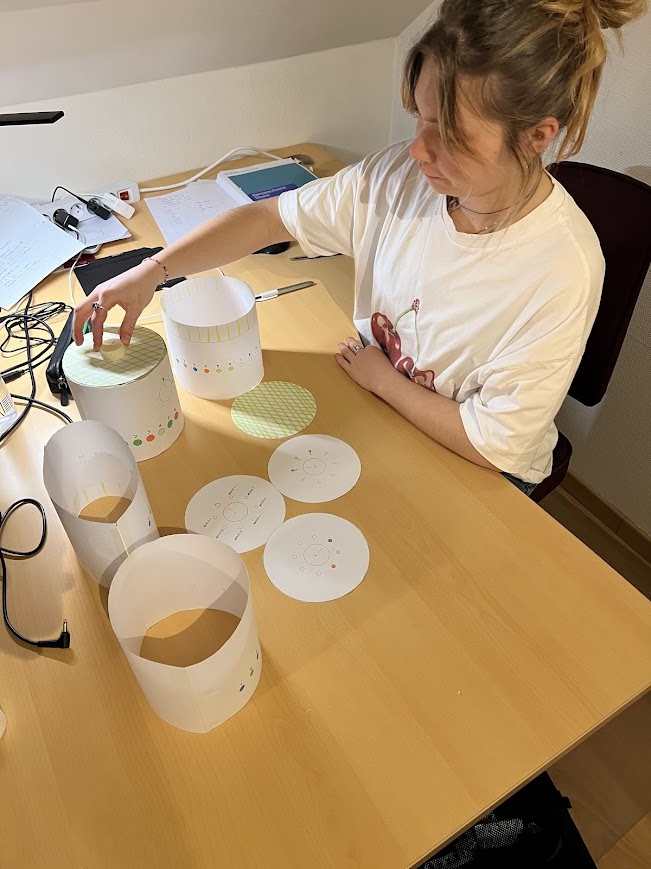
Images/IMG_6472.jpg
