WarreDV2004/UCD/Images/IMG_6473.jpg

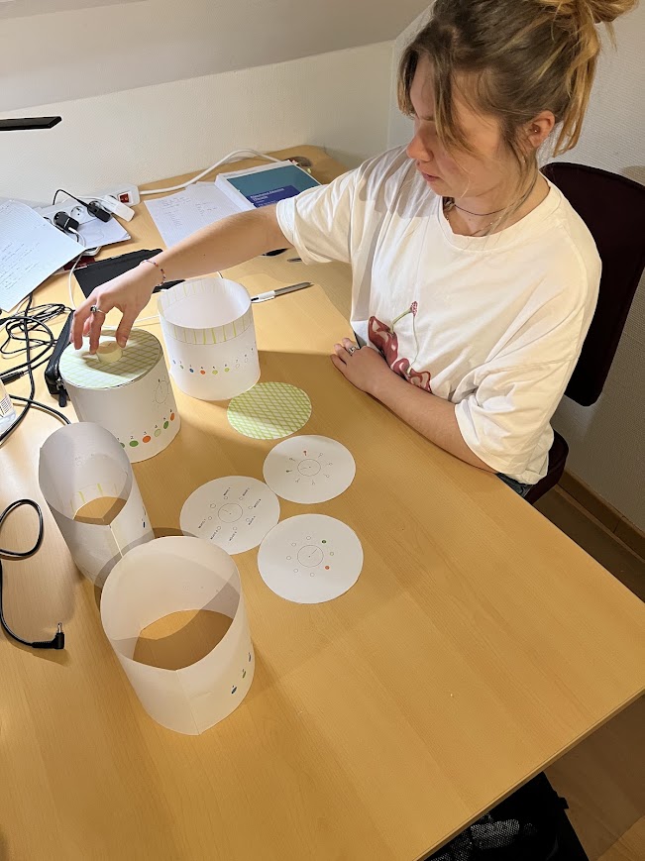
Images/IMG_6473.jpg
