WarreDV2004/UCD/Images/IMG_6474.jpg

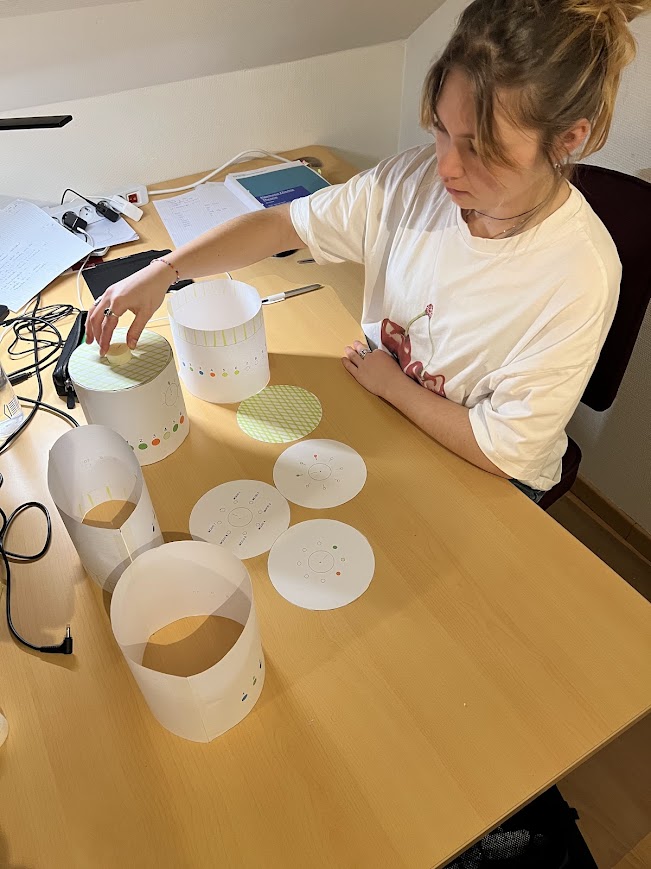
Images/IMG_6474.jpg
