WarreDV2004/UCD/Images/IMG_6476.jpg

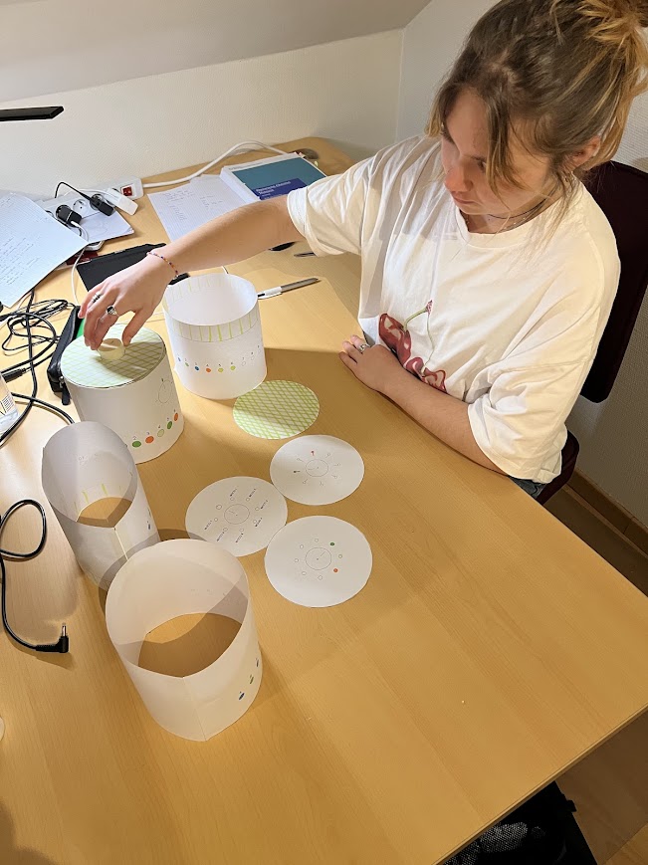
Images/IMG_6476.jpg
