WarreDV2004/UCD/Images/IMG_6477.jpg

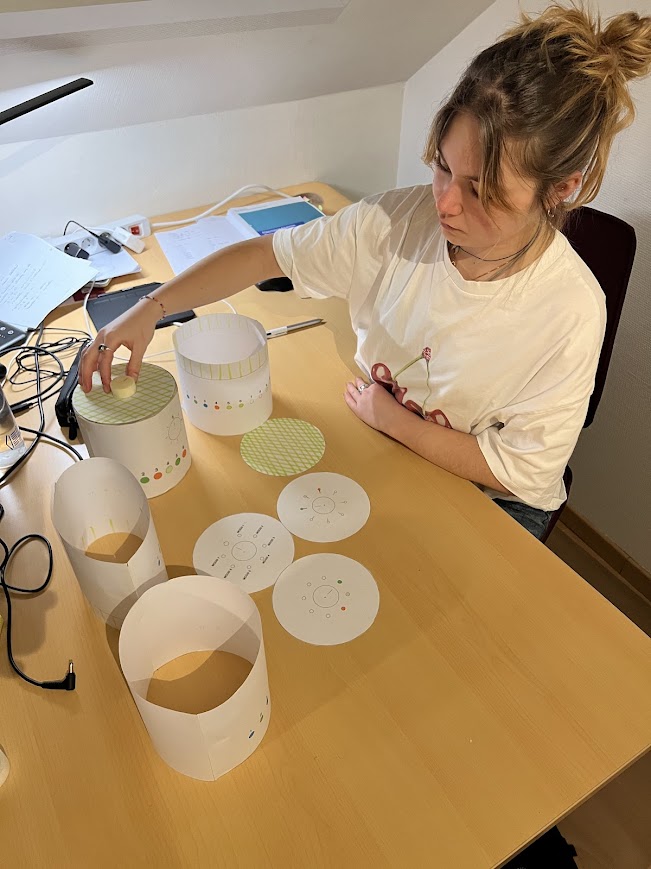
Images/IMG_6477.jpg
