WarreDV2004/UCD/Images/IMG_6478.jpg

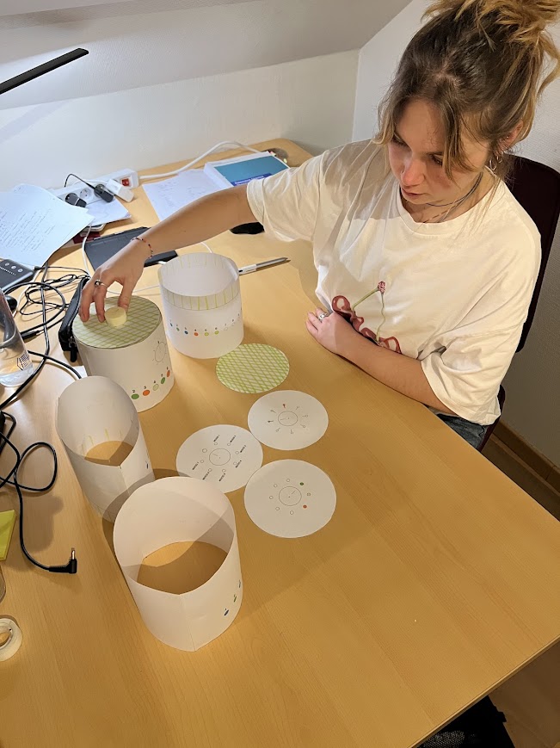
Images/IMG_6478.jpg
