WarreDV2004/UCD/Images/IMG_6516.jpg

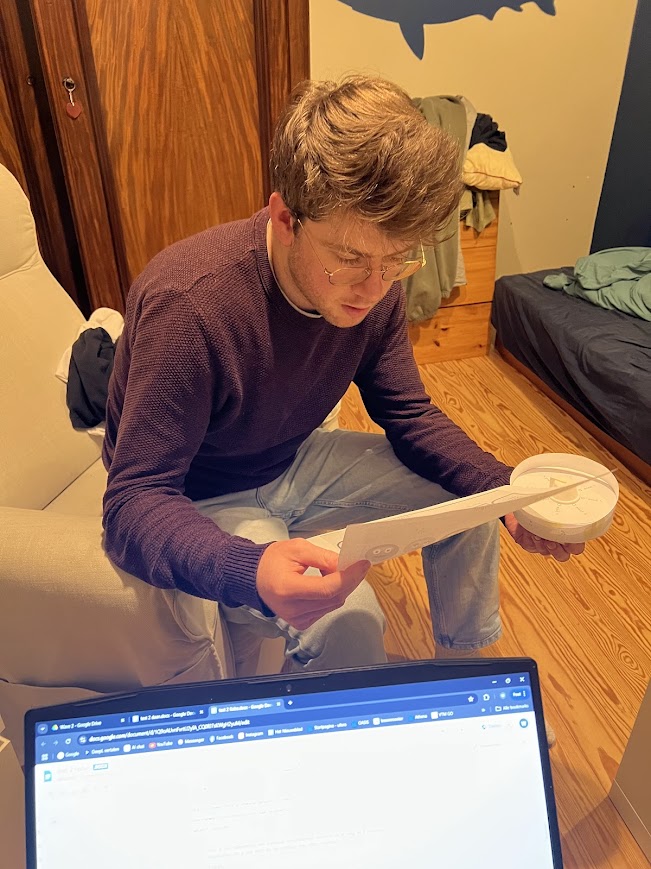
Images/IMG_6516.jpg
