WarreDV2004/UCD/Images/IMG_6518.jpg

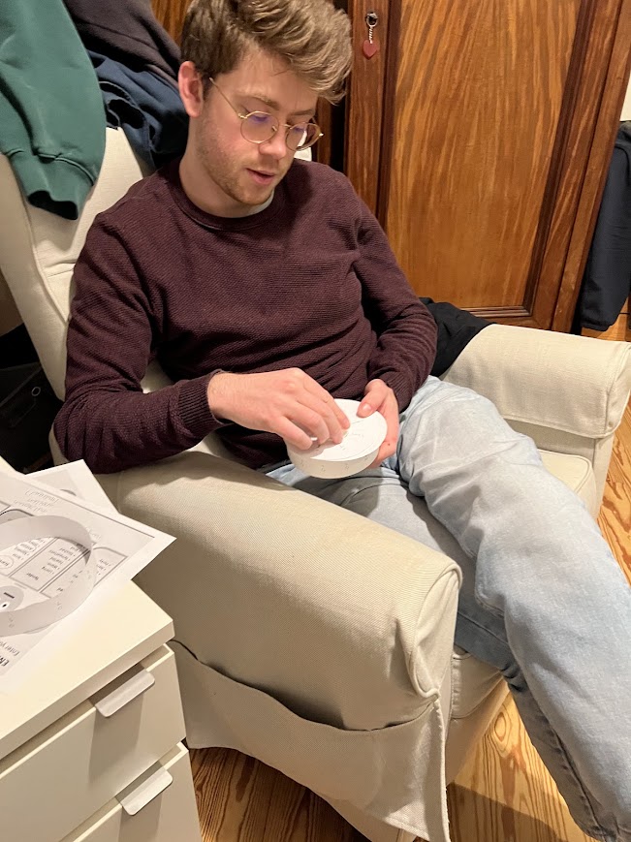
Images/IMG_6518.jpg
