WarreDV2004/UCD/Images/IMG_6519.jpg

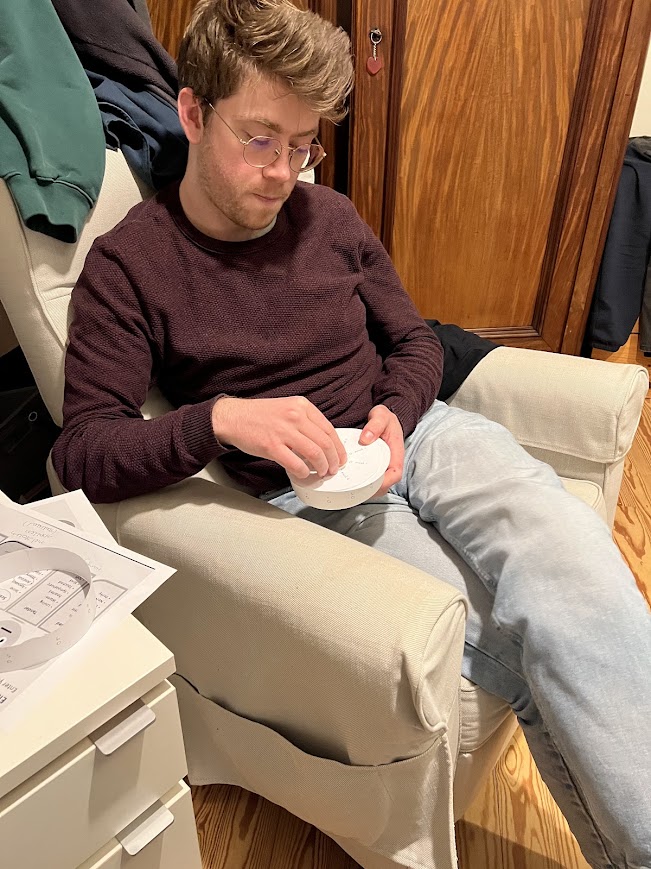
Images/IMG_6519.jpg
