WarreDV2004/UCD/Images/IMG_6520.jpg

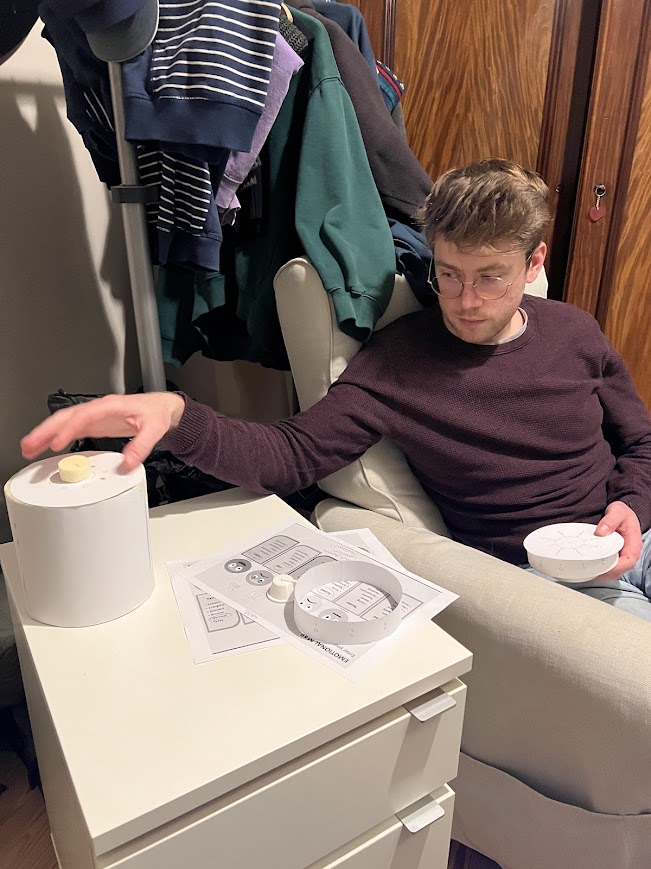
Images/IMG_6520.jpg
