WarreDV2004/UCD/Images/IMG_6521.jpg

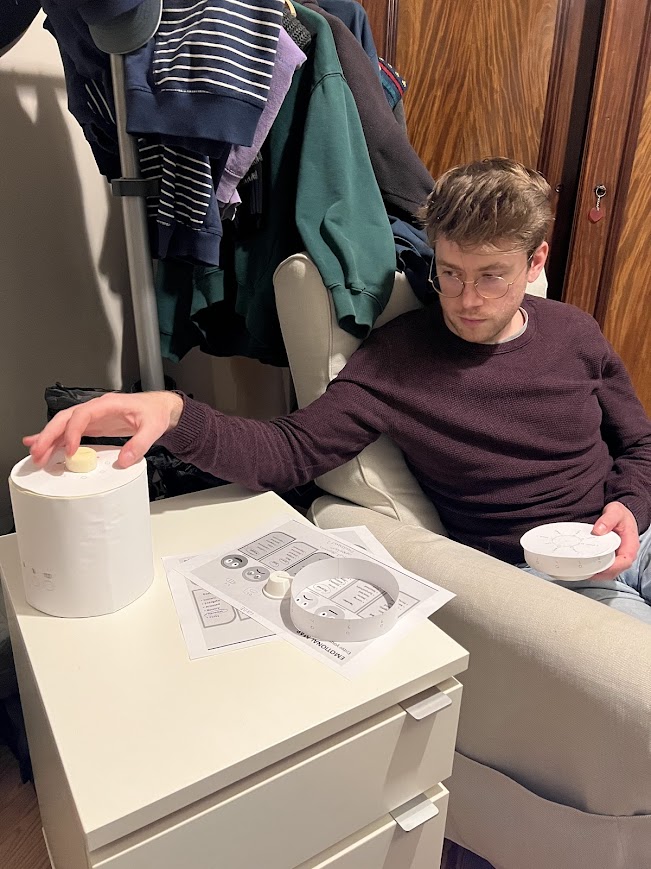
Images/IMG_6521.jpg
