WarreDV2004/UCD/Images/IMG_6522.jpg

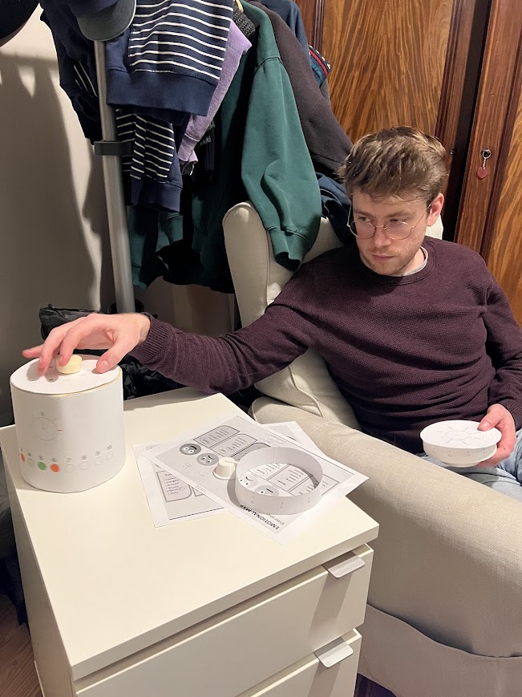
Images/IMG_6522.jpg
