WarreDV2004/UCD/Images/IMG_6555.jpg

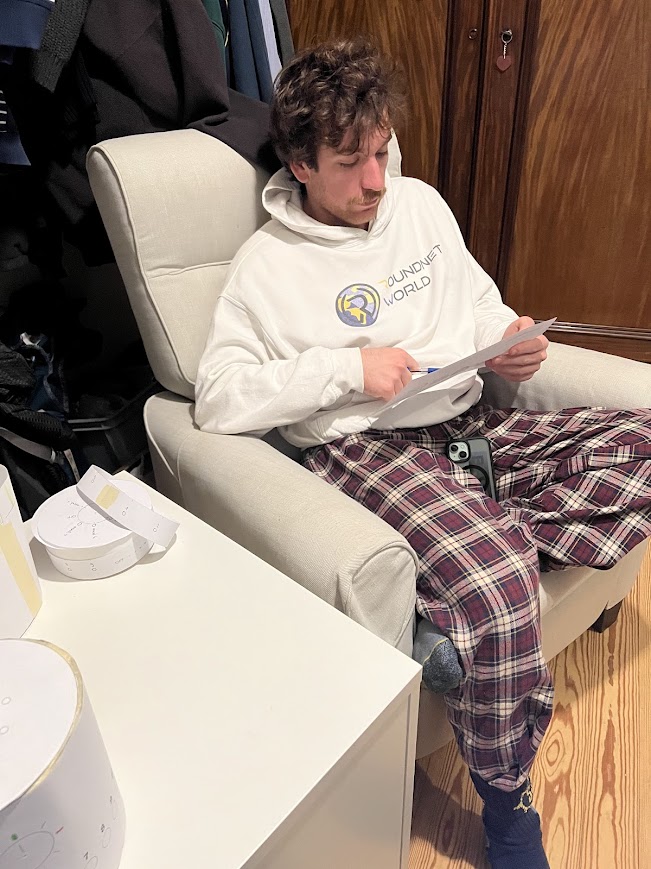
Images/IMG_6555.jpg
