WarreDV2004/UCD/Images/IMG_6557.jpg

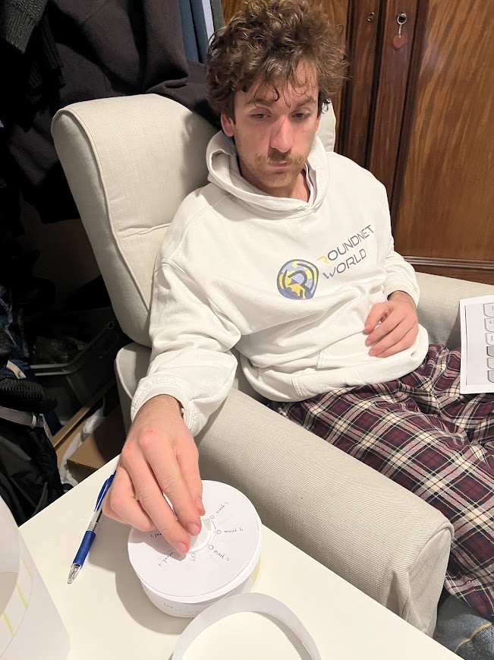
Images/IMG_6557.jpg
