WarreDV2004/UCD/Images/IMG_6558.jpg

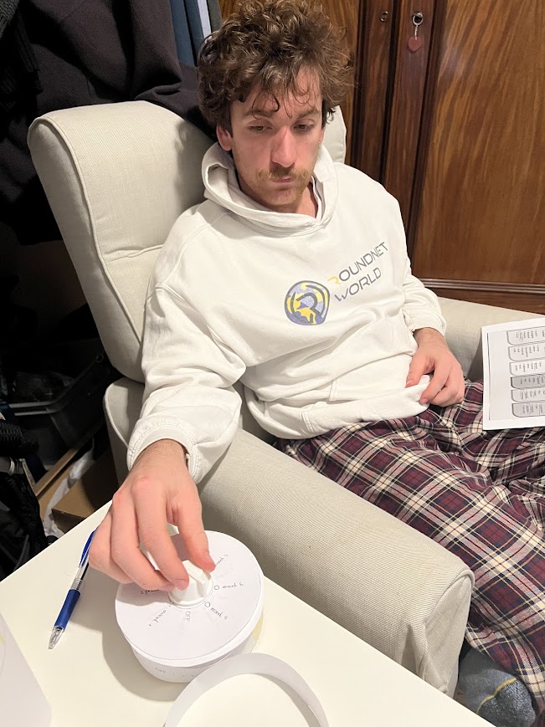
Images/IMG_6558.jpg
