WarreDV2004/UCD/Images/IMG_6560.jpg

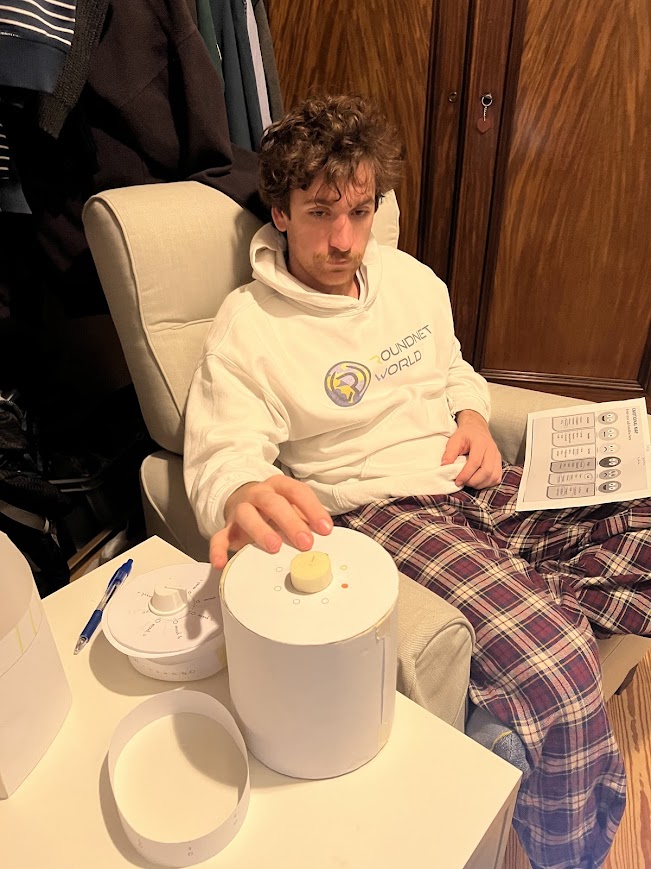
Images/IMG_6560.jpg
