WarreDV2004/UCD/Images/IMG_6561.jpg

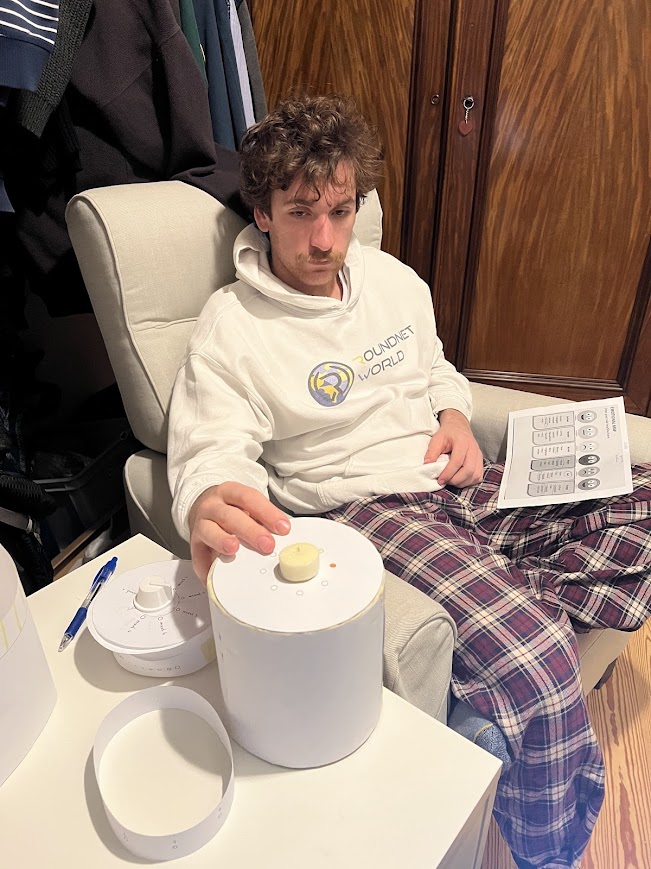
Images/IMG_6561.jpg
