WarreDV2004/UCD/Images/IMG_6563.jpg

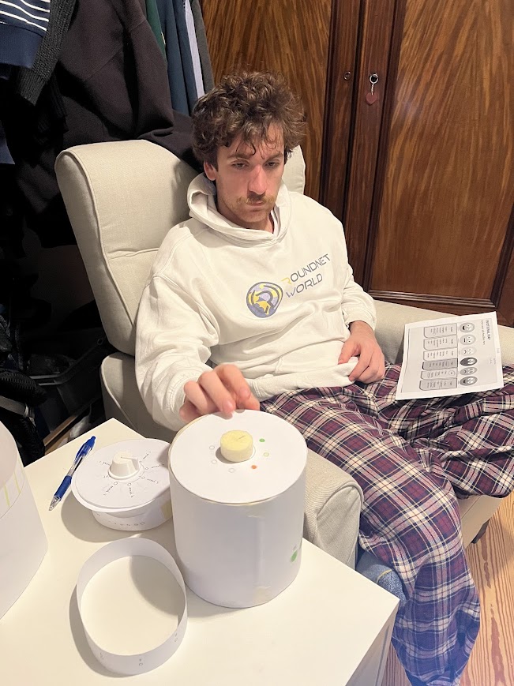
Images/IMG_6563.jpg
