WarreDV2004/UCD/Images/IMG_7355.jpeg

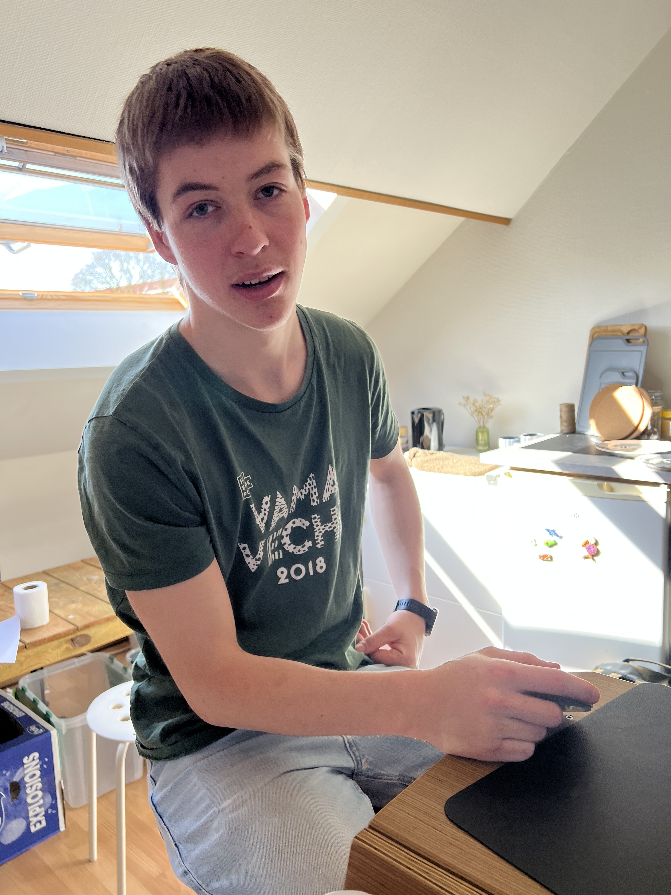
Images/IMG_7355.jpeg
