WarreDV2004/UCD/Images/IMG_7356.jpeg

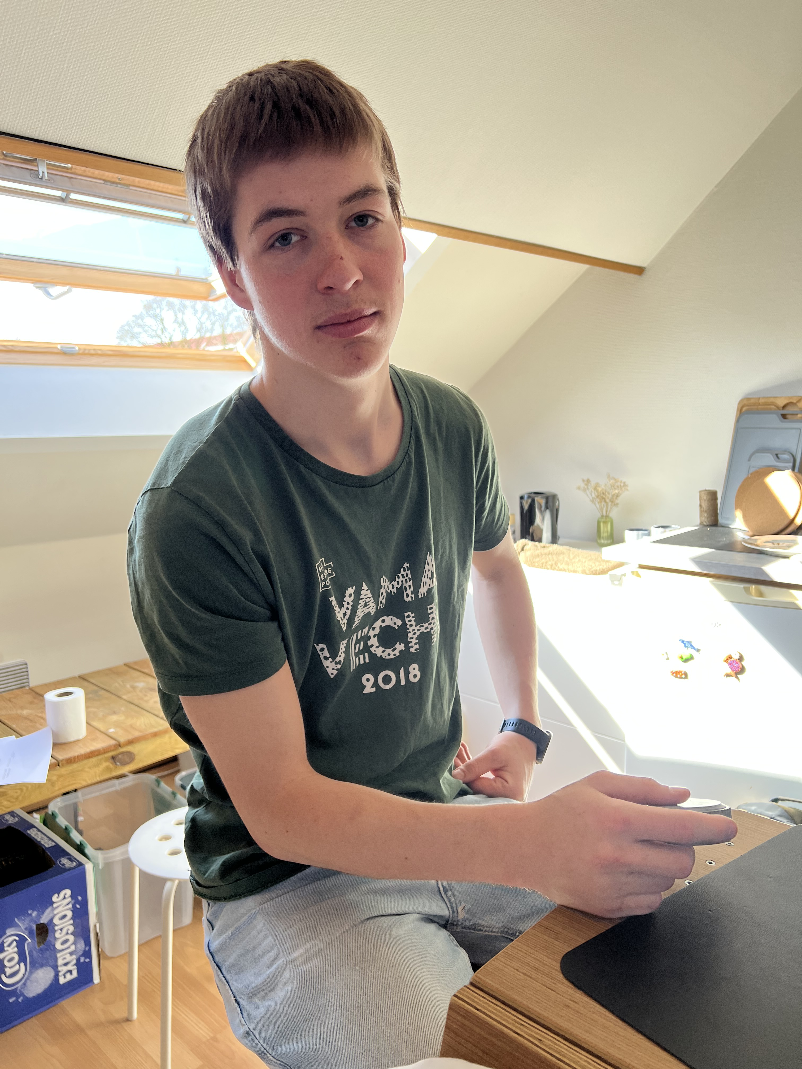
Images/IMG_7356.jpeg
