WarreDV2004/UCD/Images/IMG_7357.jpeg

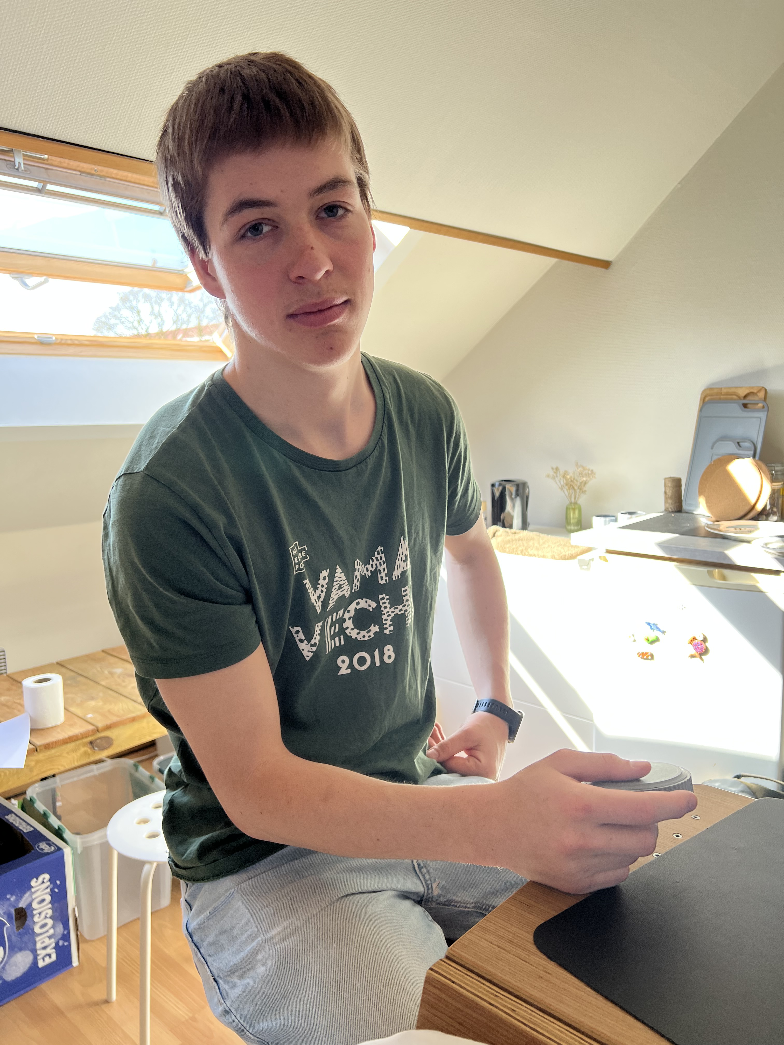
Images/IMG_7357.jpeg
