WarreDV2004/UCD/Images/IMG_7358.jpeg

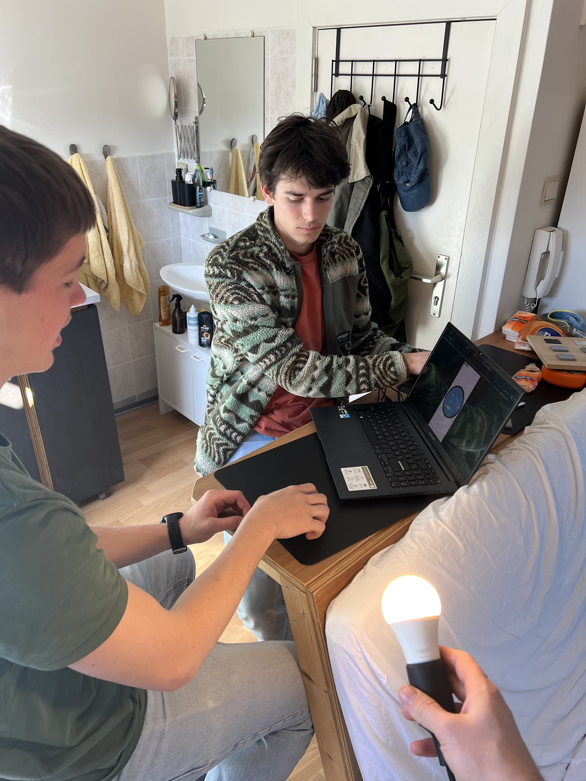
Images/IMG_7358.jpeg
