WarreDV2004/UCD/Images/IMG_7363.jpeg

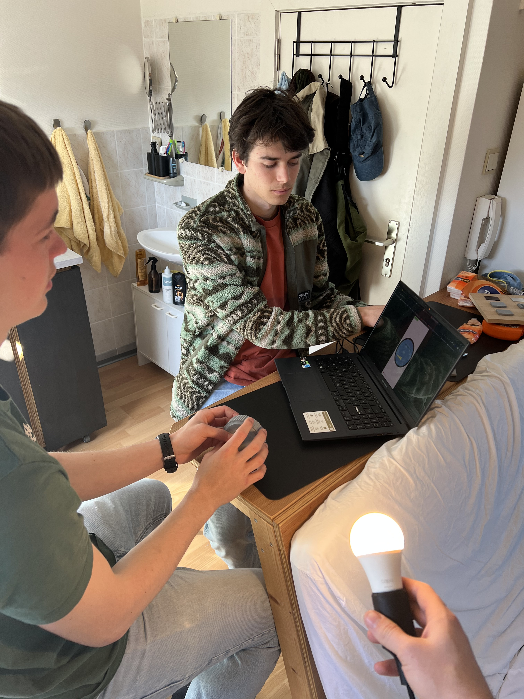
Images/IMG_7363.jpeg
