WarreDV2004/UCD/Images/IMG_7448.jpeg

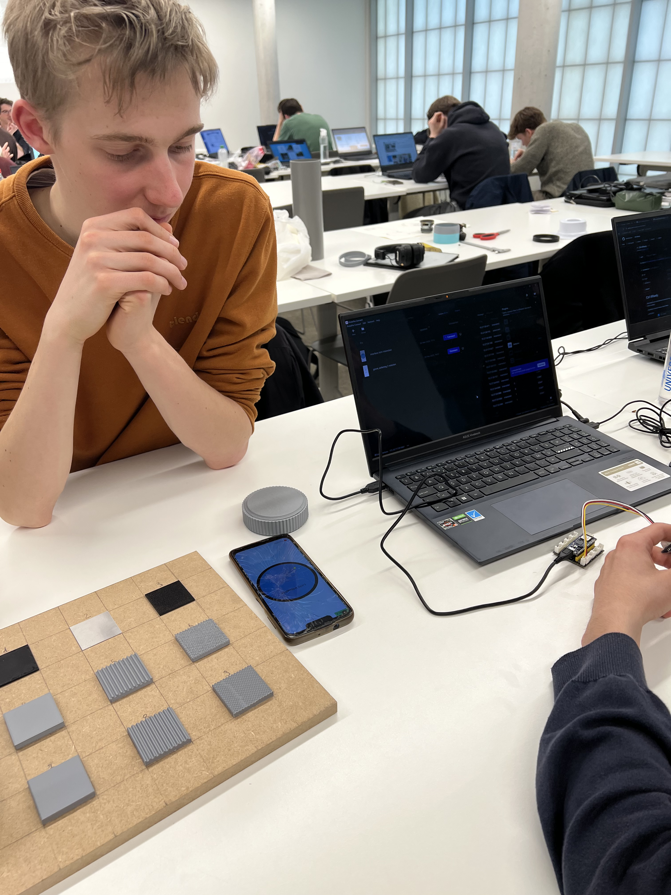
Images/IMG_7448.jpeg
