WarreDV2004/UCD/Images/IMG_7449.jpeg

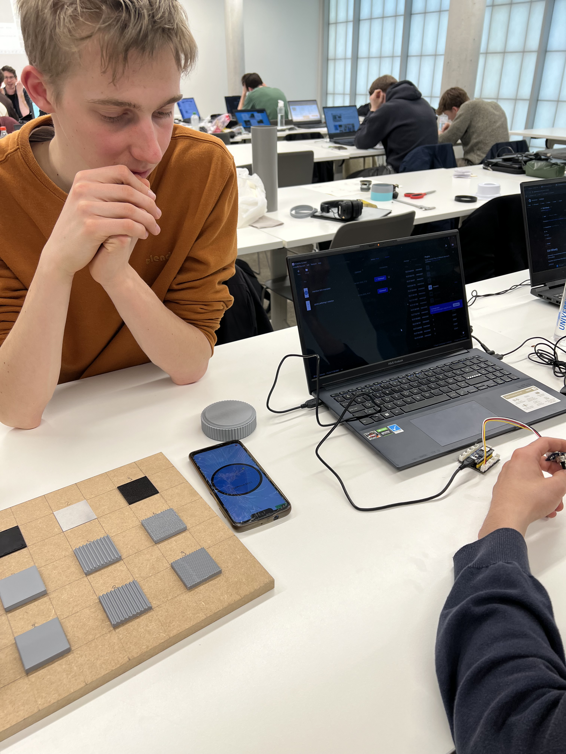
Images/IMG_7449.jpeg
