WarreDV2004/UCD/Images/IMG_7450.jpeg

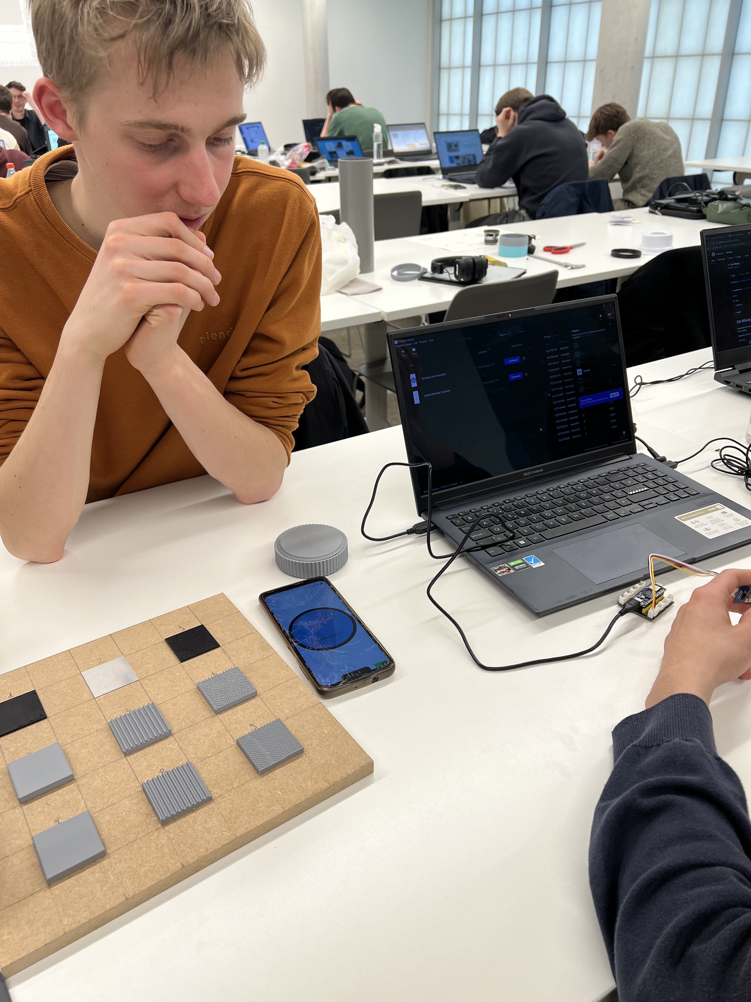
Images/IMG_7450.jpeg
