WarreDV2004/UCD/Images/match met cas.png

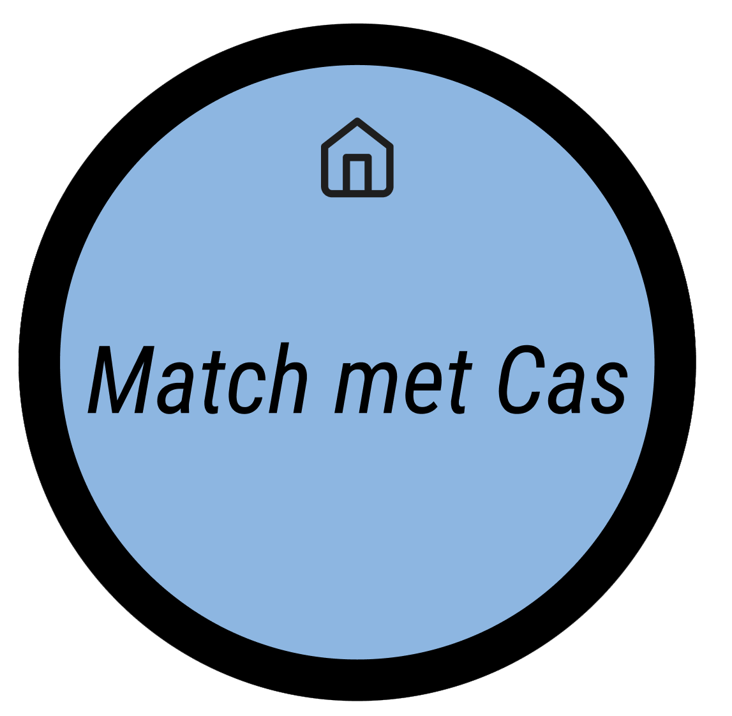
Images/match met cas.png
