WarreDV2004/UCD/Images/Schermafbeelding jack model 1.png

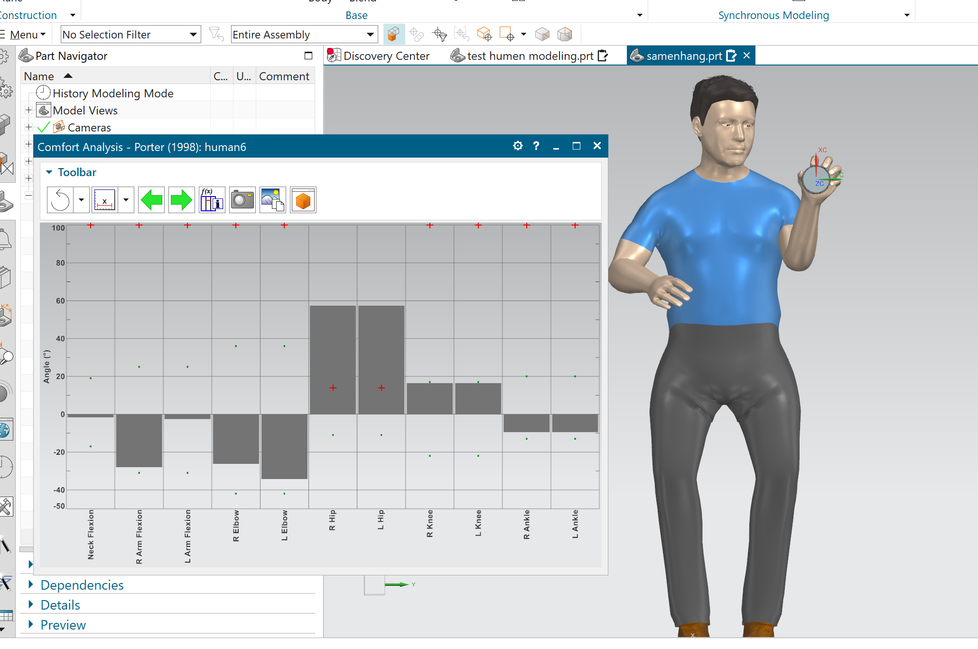
Images/Schermafbeelding jack model 1.png
