WarreDV2004/UCD/Images/Schermafbeelding jack model 2.png

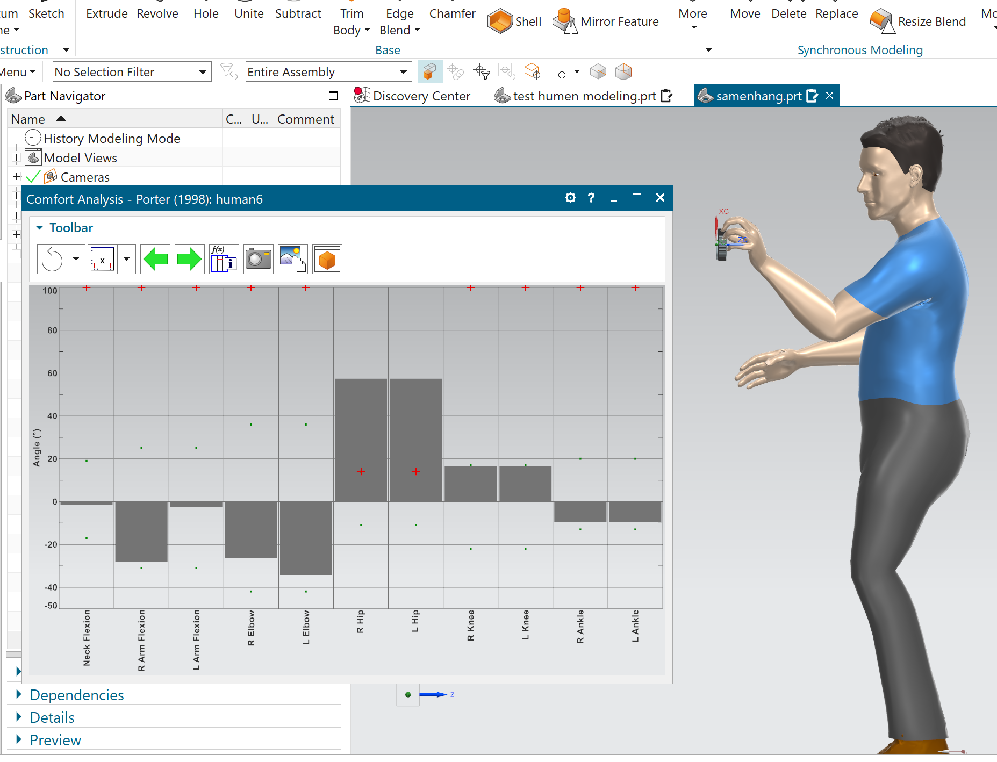
Images/Schermafbeelding jack model 2.png
