WarreDV2004/UCD/Images/IMG_7359.jpeg

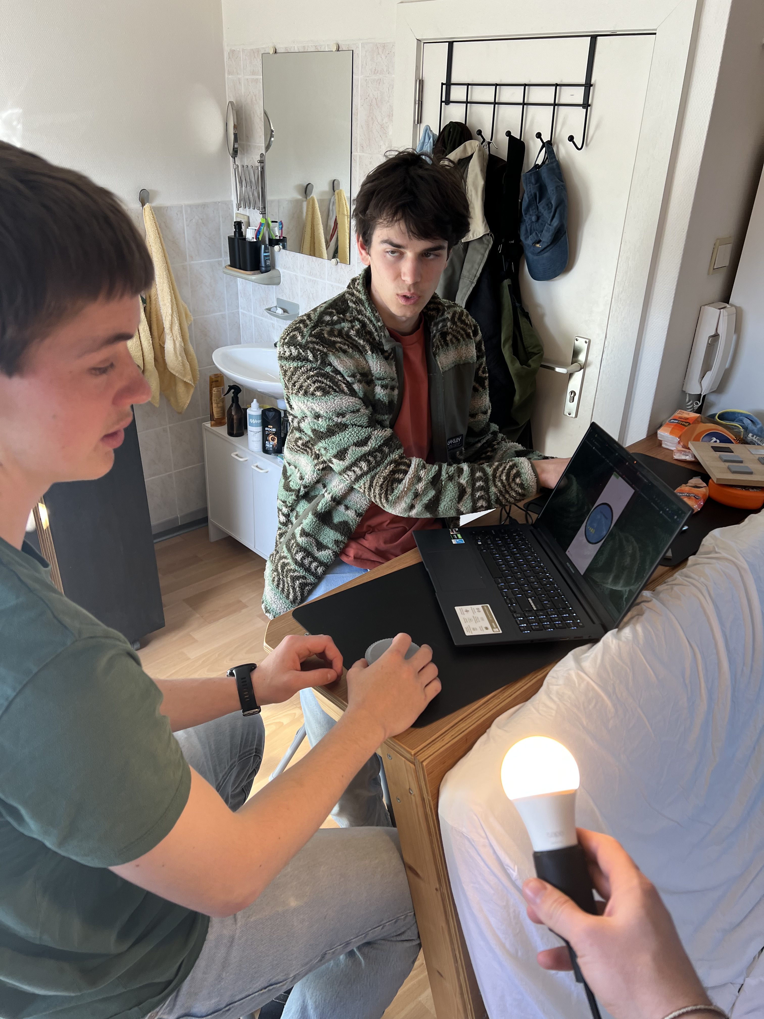
Images/IMG_7359.jpeg
