WarreDV2004/UCD/Images/IMG_7361.jpeg

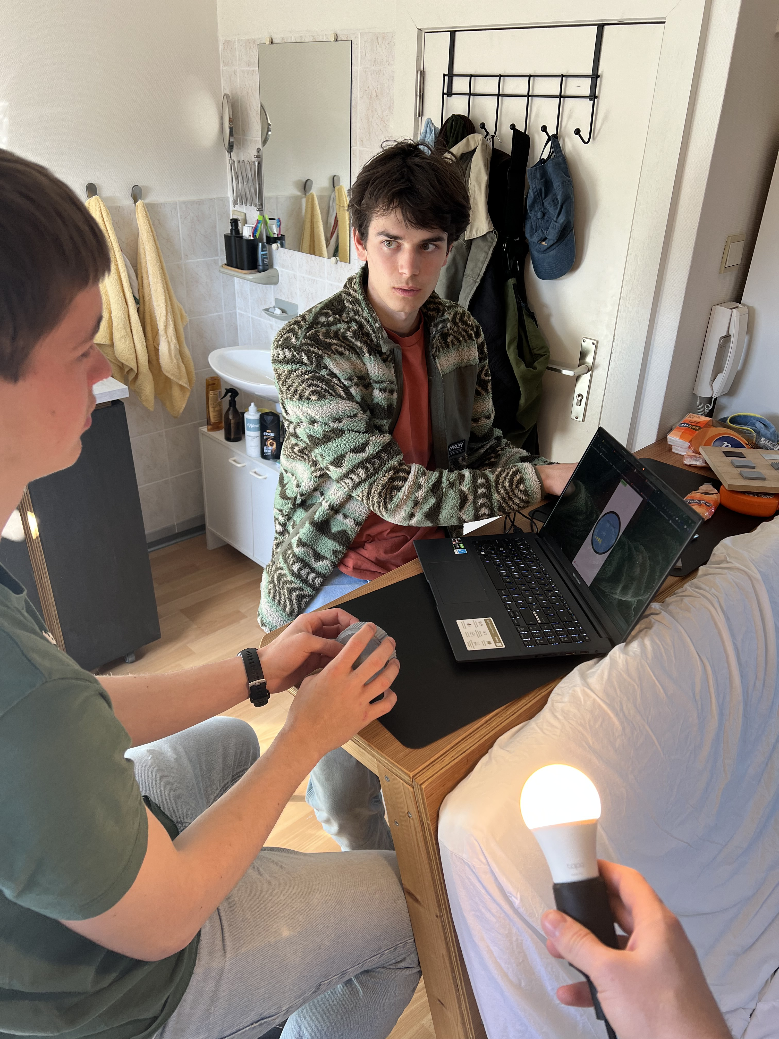
Images/IMG_7361.jpeg
